HynixCJR/LZ-1-Backplane/dp_to_hdmi.kicad_sch

## KiCad design dp_to_hdmi.kicad_sch (2026-07-11)

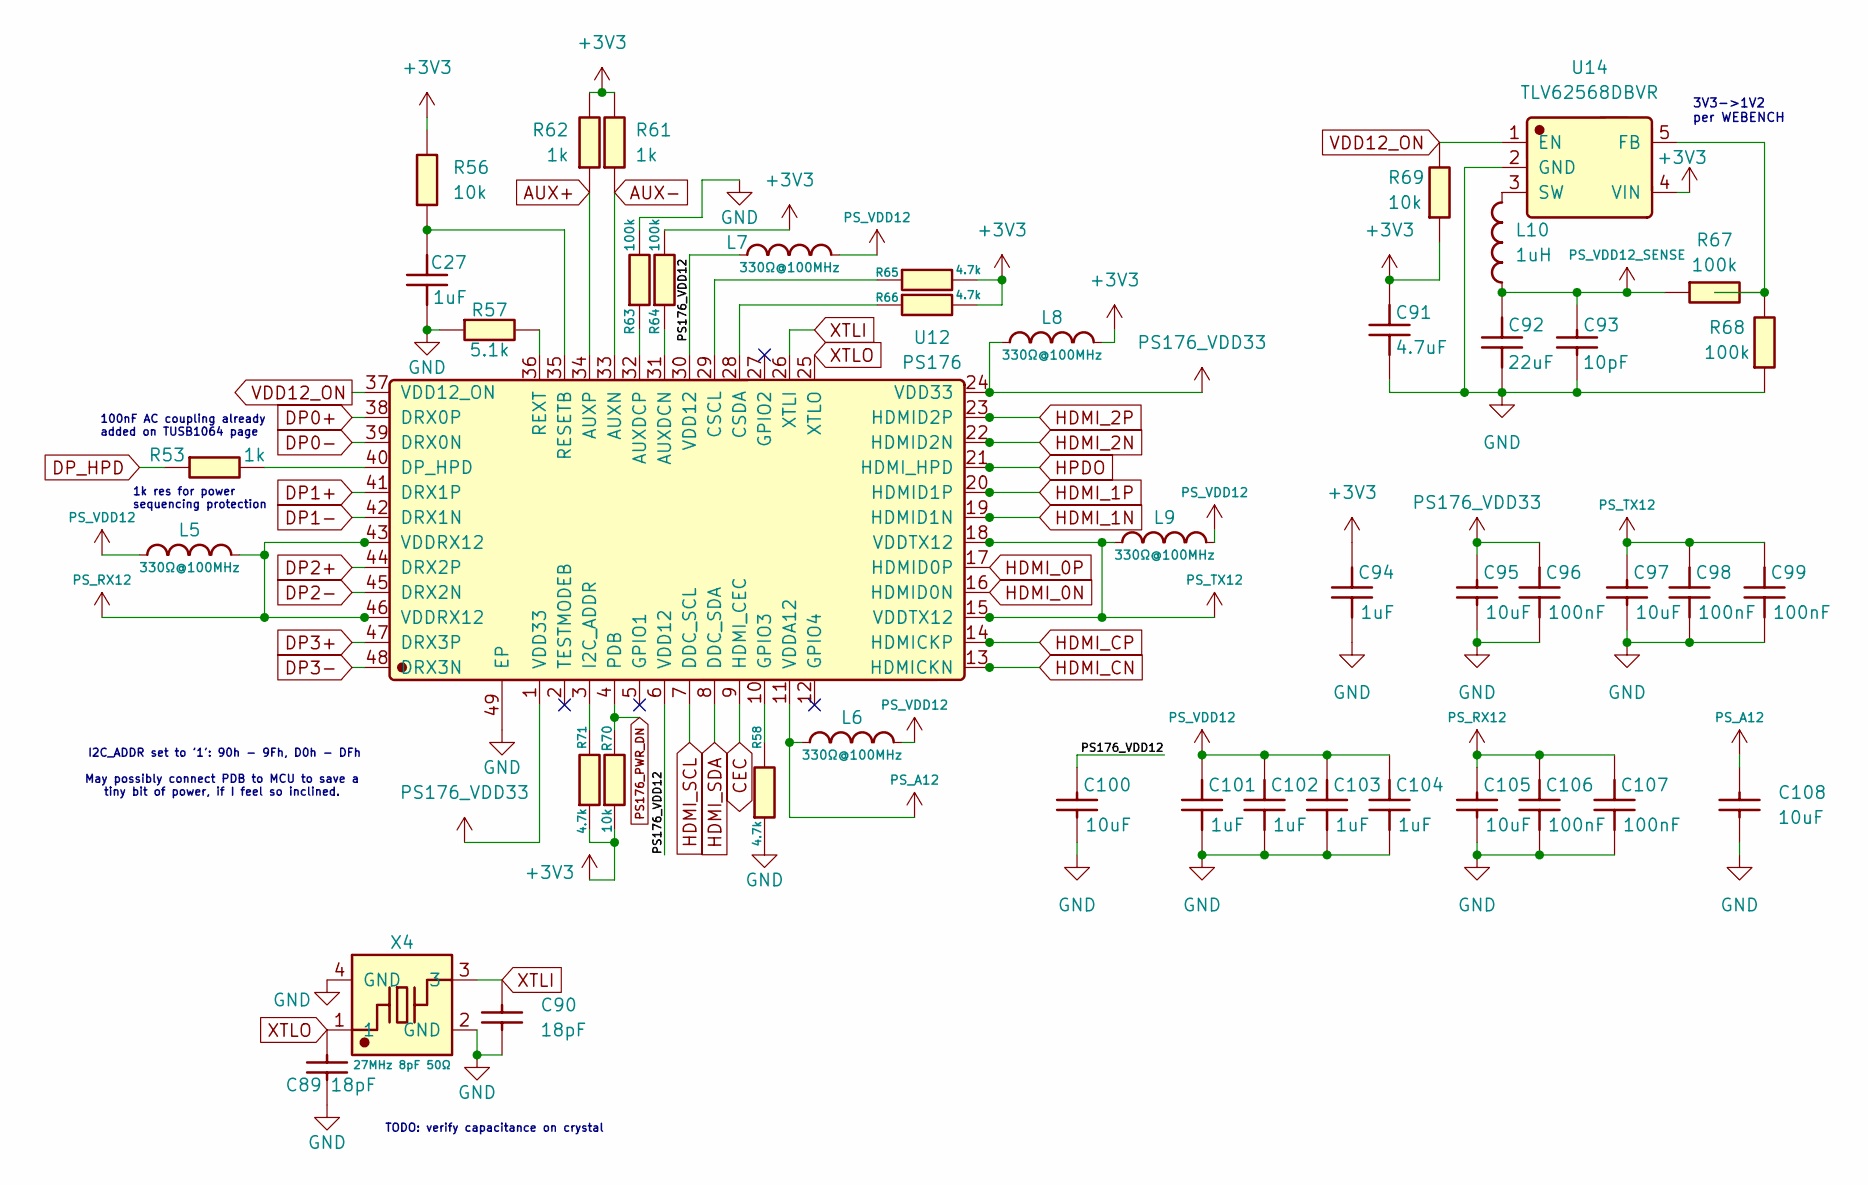
[picture p3: schematic dp_to_hdmi.kicad_sch]

Parts:
C27, C94, C101, C102, C103, C104: 1uF; C_0402_1005Metric; Manufacturer Part CL05A105KA5NQNC; LCSC C52923
C89, C90: 18pF; C_0402_1005Metric; Manufacturer Part 0402CG180J500NT; LCSC C1549
C91: 4.7uF; C_0603_1608Metric; Manufacturer Part CL10A475KO8NNNC; LCSC C19666
C92: 22uF; C_0603_1608Metric; Manufacturer Part CL10A226MQ8NRNC; LCSC C59461
C93: 10pF; C_0603_1608Metric; Manufacturer Part CL10C100JB8NNNC; LCSC C1634
C95, C97, C100, C105, C108: 10uF; C_0402_1005Metric; Manufacturer Part CL05A106MQ5NUNC; LCSC C15525
C96, C98, C99, C106, C107: 100nF; C_0402_1005Metric; Manufacturer Part CL05B104KB54PNC; LCSC C307331
L5, L6, L7, L8, L9: 330Ω@100MHz; BLM18KG331SN1D; Manufacturer Part BLM18KG331SN1D; LCSC C85832
L10: 1uH; TerminalBlock_Phoenix_PTSM-0,5-2-2,5-V-SMD_1x02-1MP_P2.50mm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; Manufacturer Part FTC252012S1R0MBCA; LCSC C5832370
R53: 1k; R_0402_1005Metric; Manufacturer Part 0402WGF1001TCE; LCSC C11702
R56, R69, R70: 10k; R_0402_1005Metric; Manufacturer Part 0402WGF1002TCE; LCSC C25744
R57: 5.1k; R_0402_1005Metric; Manufacturer Part 0402WGF5101TCE; LCSC C25905
R58, R65, R66, R71: 4.7k; R_0402_1005Metric; Manufacturer Part 0402WGF4701TCE; LCSC C25900
R61, R62: 1k; R_0402_1005Metric; Manufacturer Part 0402WGF5101TCE; LCSC C25905
R63, R64, R67, R68: 100k; R_0402_1005Metric; Manufacturer Part 0402WGF1003TCE; LCSC C25741
U12: PS176; Manufacturer Part PS176; LCSC C209703
U14: TLV62568DBVR; Manufacturer Part TLV62568DBVR; LCSC C163219
X4: 27MHz 8pF 50Ω; 5YMA27000121IF50E1; Manufacturer Part 5YMA27000121IF50E1; LCSC C3003248

Connections:
+3V3: C91.2, C94.2, L8.2, R56.2, R61.2, R62.2, R64.2, R65.2, R66.2, R69.1, R70.1, R71.1, U14.4 (VIN)
AUX+: R62.1, U12.34 (AUXP)
AUX-: R61.1, U12.33 (AUXN)
CEC: U12.9 (HDMI_CEC)
DP0+: U12.38 (DRX0P)
DP0-: U12.39 (DRX0N)
DP1+: U12.41 (DRX1P)
DP1-: U12.42 (DRX1N)
DP2+: U12.44 (DRX2P)
DP2-: U12.45 (DRX2N)
DP3+: U12.47 (DRX3P)
DP3-: U12.48 (DRX3N)
DP_HPD: R53.1
GND: C27.1, C89.1, C90.1, C91.1, C92.1, C93.1, C94.1, C95.1, C96.1, C97.1, C98.1, C99.1, C100.1, C101.1, C102.1, C103.1, C104.1, C105.1, C106.1, C107.1, C108.1, R57.1, R58.1, R63.2, R68.1, U12.49 (EP), U14.2 (GND), X4.2 (GND), X4.4 (GND)
HDMI_0N: U12.16 (HDMID0N)
HDMI_0P: U12.17 (HDMID0P)
HDMI_1N: U12.19 (HDMID1N)
HDMI_1P: U12.20 (HDMID1P)
HDMI_2N: U12.22 (HDMID2N)
HDMI_2P: U12.23 (HDMID2P)
HDMI_CN: U12.13 (HDMICKN)
HDMI_CP: U12.14 (HDMICKP)
HDMI_SCL: U12.7 (DDC_SCL)
HDMI_SDA: U12.8 (DDC_SDA)
HPDO: U12.21 (HDMI_HPD)
unnamed: C27.2, R56.1, U12.35 (RESETB)
unnamed: L10.2, U14.3 (SW)
unnamed: R53.2, U12.40 (DP_HPD)
unnamed: R57.2, U12.36 (REXT)
unnamed: R58.2, U12.10 (GPIO3)
unnamed: R63.1, U12.32 (AUXDCP)
unnamed: R64.1, U12.31 (AUXDCN)
unnamed: R65.1, U12.29 (CSCL)
unnamed: R66.1, U12.28 (CSDA)
unnamed: R67.2, R68.2, U14.5 (FB)
unnamed: R71.2, U12.3 (I2C_ADDR)
PS176_PWR_DN: R70.2, U12.4 (PDB)
PS176_VDD12: C100.2, L7.1, U12.6 (VDD12), U12.30 (VDD12)
PS176_VDD33: C95.2, C96.2, L8.1, U12.1 (VDD33), U12.24 (VDD33)
PS_A12: C108.2, L6.1, U12.11 (VDDA12)
PS_RX12: C105.2, C106.2, C107.2, L5.2, U12.43 (VDDRX12), U12.46 (VDDRX12)
PS_TX12: C97.2, C98.2, C99.2, L9.1, U12.15 (VDDTX12), U12.18 (VDDTX12)
PS_VDD12: C101.2, C102.2, C103.2, C104.2, L5.1, L6.2, L7.2, L9.2
PS_VDD12_SENSE: C92.2, C93.2, L10.1, R67.1
VDD12_ON: R69.2, U12.37 (VDD12_ON), U14.1 (EN)
XTLI: C90.2, U12.26 (XTLI), X4.3
XTLO: C89.2, U12.25 (XTLO), X4.1

Notes on the sheet:
1k res for power sequencing protection
3V3->1V2 per WEBENCH
May possibly connect PDB to MCU to save a tiny bit of power, if I feel so inclined.
I2C_ADDR set to '1': 90h - 9Fh, D0h - DFh
100nF AC coupling already added on TUSB1064 page
TODO: verify capacitance on crystal
