HynixCJR/LZ-1-Backplane/hdmi_to_csi.kicad_sch

## KiCad design hdmi_to_csi.kicad_sch (2026-07-11)

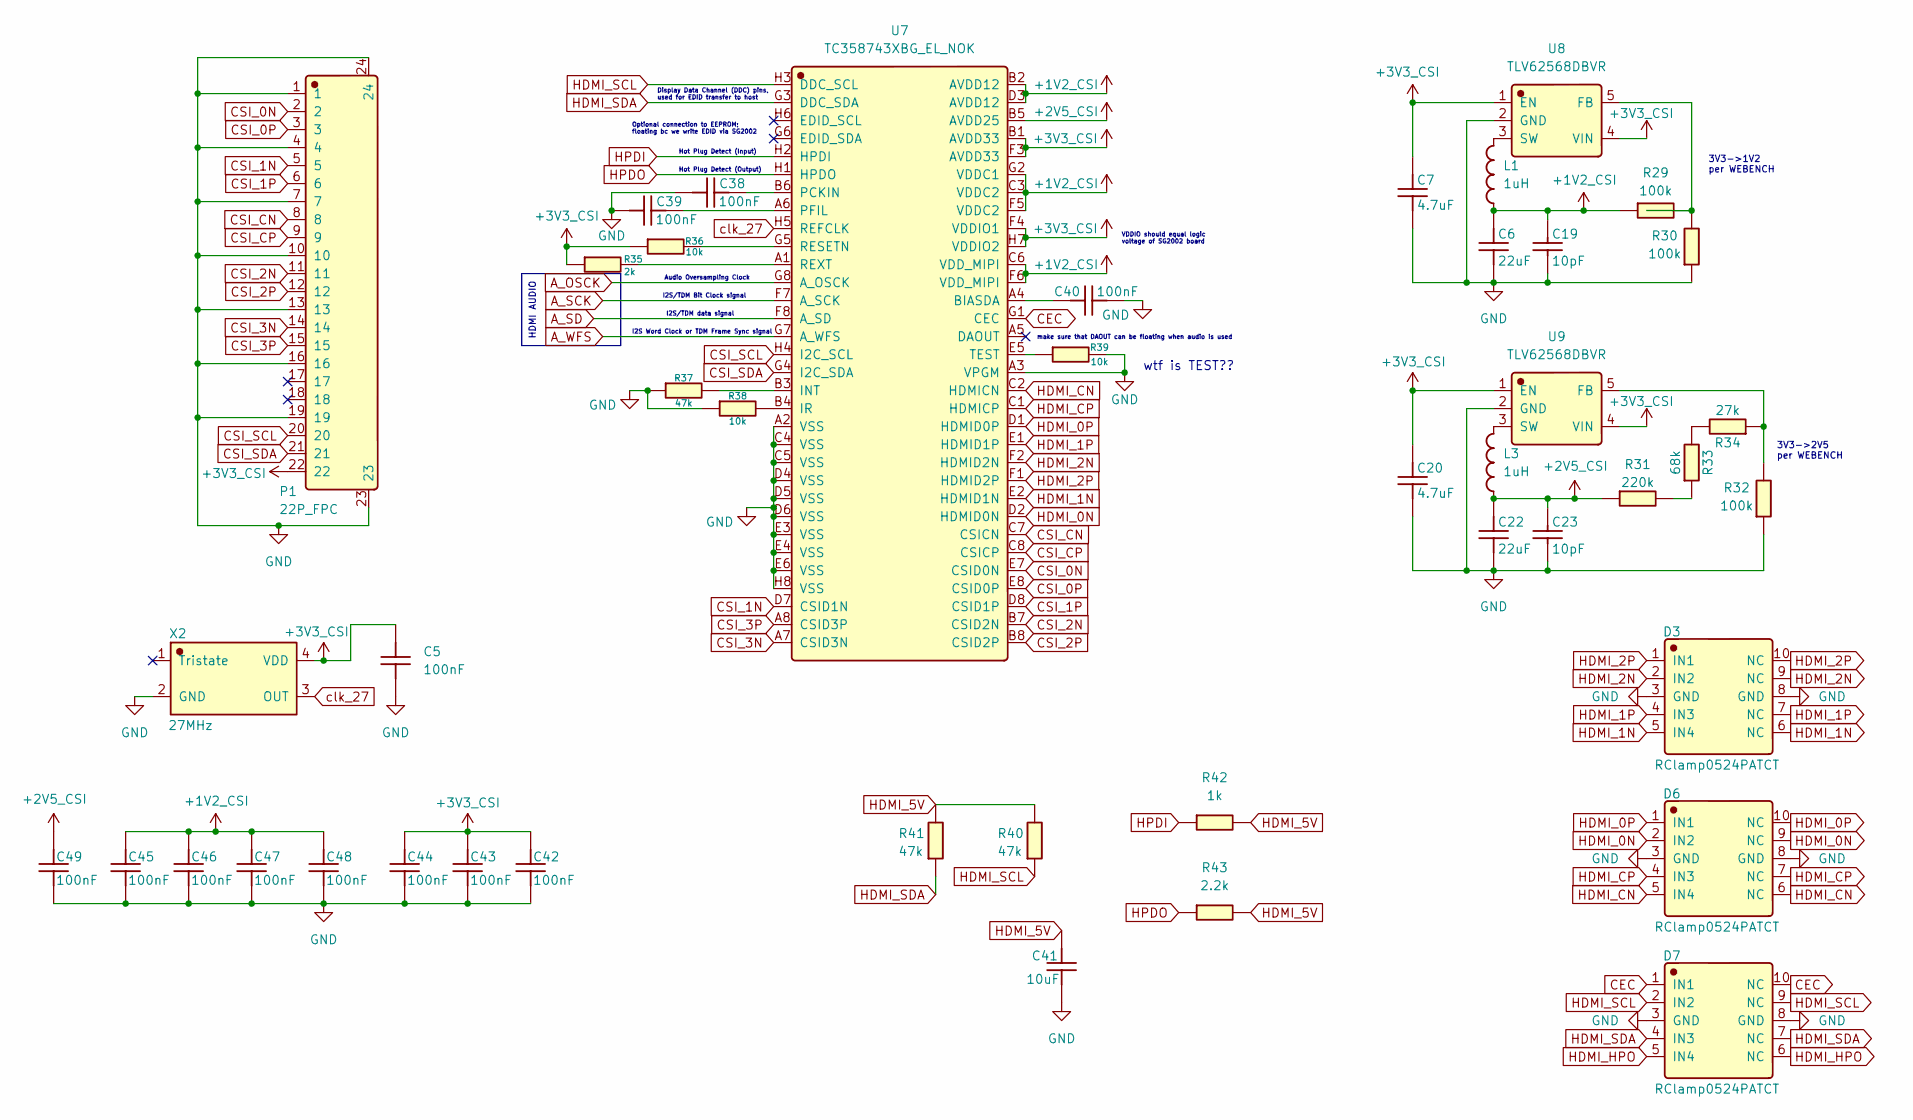
[picture p4: schematic hdmi_to_csi.kicad_sch]

Parts:
C5, C38, C39, C40, C42, C43, C44, C45, C46, C47, C48, C49: 100nF; C_0402_1005Metric; Manufacturer Part CL05B104KB54PNC; LCSC C307331
C6, C22: 22uF; C_0603_1608Metric; Manufacturer Part CL10A226MQ8NRNC; LCSC C59461
C7, C20: 4.7uF; C_0603_1608Metric; Manufacturer Part CL10A475KO8NNNC; LCSC C19666
C19, C23: 10pF; C_0603_1608Metric; Manufacturer Part CL10C100JB8NNNC; LCSC C1634
C41: 10uF; C_0603_1608Metric; Manufacturer Part CL10A106KP8NNNC; LCSC C19702
D3, D6, D7: RClamp0524PATCT; Manufacturer Part RClAMP0524PATCT; LCSC C40960
L1, L3: 1uH; TerminalBlock_Phoenix_PTSM-0,5-2-2,5-V-SMD_1x02-1MP_P2.50mm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; Manufacturer Part FTC252012S1R0MBCA; LCSC C5832370
P1: 22P_FPC; TSSOP-50_4.4x12.5mm_P0.5mm; Manufacturer Part AFC07-S22ECC-00; LCSC C11091
R29, R30, R32: 100k; R_0402_1005Metric; Manufacturer Part 0402WGF1003TCE; LCSC C25741
R31: 220k; R_0603_1608Metric; Manufacturer Part 0603WAF2203T5E; LCSC C22961
R33: 68k; R_0603_1608Metric; Manufacturer Part 0603WAF6802T5E; LCSC C23231
R34: 27k; R_0603_1608Metric; Manufacturer Part 0603WAF2702T5E; LCSC C22967
R35: 2k; R_0603_1608Metric; Manufacturer Part 0603WAF2001T5E; LCSC C22975
R36, R38, R39: 10k; R_0402_1005Metric; Manufacturer Part 0402WGF1002TCE; LCSC C25744
R37, R40, R41: 47k; R_0402_1005Metric; Manufacturer Part 0402WGF4702TCE; LCSC C25792
R42: 1k; R_0402_1005Metric; Manufacturer Part 0402WGF1001TCE; LCSC C11702
R43: 2.2k; R_0402_1005Metric; Manufacturer Part 0402WGF2201TCE; LCSC C25879
U7: TC358743XBG_EL_NOK; Manufacturer Part TC358743XBG(EL,NOK; LCSC C3008606
U8, U9: TLV62568DBVR; Manufacturer Part TLV62568DBVR; LCSC C163219
X2: 27MHz; Oscillator_SMD_Silicon_Labs_LGA-6_2.5x3.2mm_P1.25mm; Manufacturer Part XOS32027000LT00351005; LCSC C37635418

Connections:
+1V2_CSI: C6.2, C19.2, C45.2, C46.2, C47.2, C48.2, L1.1, R29.1, U7.B2 (AVDD12), U7.C3 (VDDC2), U7.C6 (VDD_MIPI), U7.D3 (AVDD12), U7.F5 (VDDC2), U7.F6 (VDD_MIPI), U7.G2 (VDDC1)
+2V5_CSI: C22.2, C23.2, C49.2, L3.1, R31.1, U7.B5 (AVDD25)
+3V3_CSI: C5.2, C7.2, C20.2, C42.2, C43.2, C44.2, P1.22, R35.1, R36.1, U7.B1 (AVDD33), U7.F3 (AVDD33), U7.F4 (VDDIO1), U7.H7 (VDDIO2), U8.1 (EN), U8.4 (VIN), U9.1 (EN), U9.4 (VIN), X2.4 (VDD)
A_OSCK: U7.G8 (A_OSCK)
A_SCK: U7.F7 (A_SCK)
A_SD: U7.F8 (A_SD)
A_WFS: U7.G7 (A_WFS)
CEC: D7.1 (IN1), D7.10 (NC), U7.G1 (CEC)
CSI_0N: P1.2, U7.E7 (CSID0N)
CSI_0P: P1.3, U7.E8 (CSID0P)
CSI_1N: P1.5, U7.D7 (CSID1N)
CSI_1P: P1.6, U7.D8 (CSID1P)
CSI_2N: P1.11, U7.B7 (CSID2N)
CSI_2P: P1.12, U7.B8 (CSID2P)
CSI_3N: P1.14, U7.A7 (CSID3N)
CSI_3P: P1.15, U7.A8 (CSID3P)
CSI_CN: P1.8, U7.C7 (CSICN)
CSI_CP: P1.9, U7.C8 (CSICP)
CSI_SCL: P1.20, U7.H4 (I2C_SCL)
CSI_SDA: P1.21, U7.G4 (I2C_SDA)
GND: C5.1, C6.1, C7.1, C19.1, C20.1, C22.1, C23.1, C38.1, C39.1, C40.2, C41.1, C42.1, C43.1, C44.1, C45.1, C46.1, C47.1, C48.1, C49.1, D3.3 (GND), D3.8 (GND), D6.3 (GND), D6.8 (GND), D7.3 (GND), D7.8 (GND), P1.1, P1.4, P1.7, P1.10, P1.13, P1.16, P1.19, P1.23, P1.24, R30.1, R32.1, R37.1, R38.1, R39.2, U7.A2 (VSS), U7.A3 (VPGM), U7.C4 (VSS), U7.C5 (VSS), U7.D4 (VSS), U7.D5 (VSS), U7.D6 (VSS), U7.E3 (VSS), U7.E4 (VSS), U7.E6 (VSS), U7.H8 (VSS), U8.2 (GND), U9.2 (GND), X2.2 (GND)
HDMI_0N: D6.2 (IN2), D6.9 (NC), U7.D2 (HDMID0N)
HDMI_0P: D6.1 (IN1), D6.10 (NC), U7.D1 (HDMID0P)
HDMI_1N: D3.5 (IN4), D3.6 (NC), U7.E2 (HDMID1N)
HDMI_1P: D3.4 (IN3), D3.7 (NC), U7.E1 (HDMID1P)
HDMI_2N: D3.2 (IN2), D3.9 (NC), U7.F2 (HDMID2N)
HDMI_2P: D3.1 (IN1), D3.10 (NC), U7.F1 (HDMID2P)
HDMI_5V: C41.2, R40.2, R41.2, R42.2, R43.2
HDMI_CN: D6.5 (IN4), D6.6 (NC), U7.C2 (HDMICN)
HDMI_CP: D6.4 (IN3), D6.7 (NC), U7.C1 (HDMICP)
HDMI_HPO: D7.5 (IN4), D7.6 (NC)
HDMI_SCL: D7.2 (IN2), D7.9 (NC), R40.1, U7.H3 (DDC_SCL)
HDMI_SDA: D7.4 (IN3), D7.7 (NC), R41.1, U7.G3 (DDC_SDA)
HPDI: R42.1, U7.H2 (HPDI)
HPDO: R43.1, U7.H1 (HPDO)
unnamed: C38.2, U7.B6 (PCKIN)
unnamed: C39.2, U7.A6 (PFIL)
unnamed: C40.1, U7.A4 (BIASDA)
unnamed: L1.2, U8.3 (SW)
unnamed: L3.2, U9.3 (SW)
unnamed: R29.2, R30.2, U8.5 (FB)
unnamed: R31.2, R33.1
unnamed: R32.2, R34.1, U9.5 (FB)
unnamed: R33.2, R34.2
unnamed: R35.2, U7.A1 (REXT)
unnamed: R36.2, U7.G5 (RESETN)
unnamed: R37.2, U7.B3 (INT)
unnamed: R38.2, U7.B4 (IR)
unnamed: R39.1, U7.E5 (TEST)
clk_27: U7.H5 (REFCLK), X2.3 (OUT)

Notes on the sheet:
Hot Plug Detect (Output)
wtf is TEST??
Optional connection to EEPROM; floating bc we write EDID via SG2002
VDDIO should equal logic voltage of SG2002 board
make sure that DAOUT can be floating when audio is used
HDMI AUDIO
3V3->2V5 per WEBENCH
Hot Plug Detect (Input)
I2S/TDM Bit Clock signal
I2S Word Clock or TDM Frame Sync signal
Audio Oversampling Clock
Display Data Channel (DDC) pins, used for EDID transfer to host
3V3->1V2 per WEBENCH
I2S/TDM data signal
