HynixCJR/LZ-1-Backplane/pcb_files/FAN_HEADER.kicad_sch

## KiCad design pcb_files/FAN_HEADER.kicad_sch (2026-08-20)

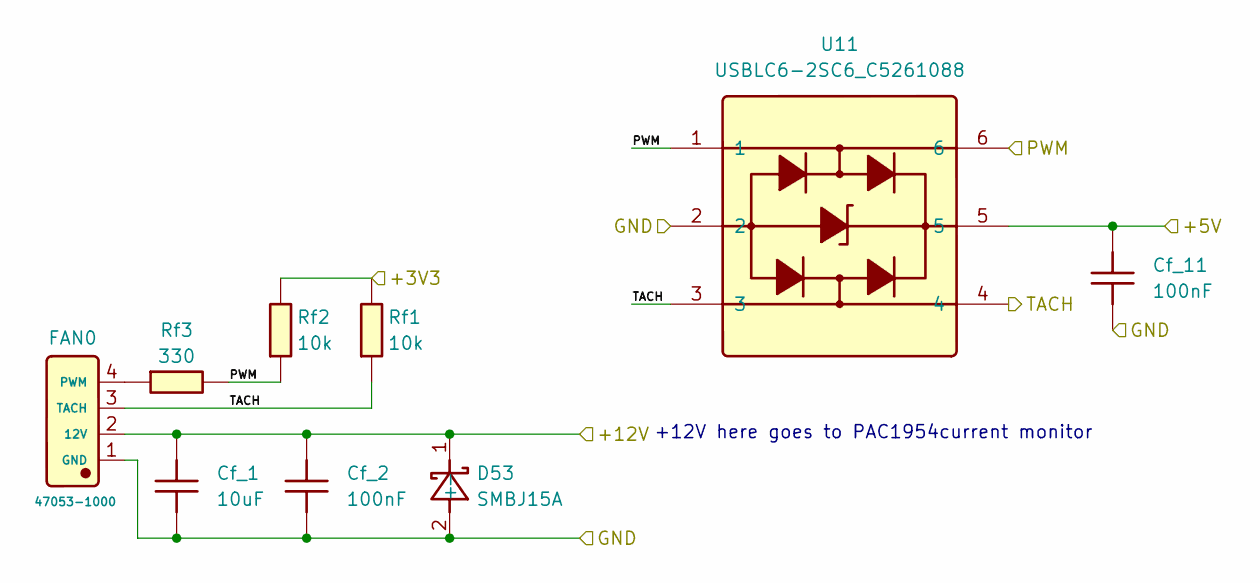
[picture p5: schematic FAN_HEADER.kicad_sch]

Parts:
Cf_1: 10uF; C_0603_1608Metric; Manufacturer Part CL10A106KP8NNNC; LCSC C19702
Cf_2, Cf_11: 100nF; C_0402_1005Metric; Manufacturer Part CL05B104KB54PNC; LCSC C307331
D53: SMBJ15A; SMBJ15A_C42370523; Manufacturer Part SMBJ15A; LCSC C42370523
FAN0: 47053-1000; Manufacturer Part 470531000; LCSC C240840
Rf1, Rf2: 10k; R_0402_1005Metric; Manufacturer Part 0402WGF1002TCE; LCSC C25744
Rf3: 330; R_0402_1005Metric; Manufacturer Part 0402WGF3300TCE; LCSC C25104
U11: USBLC6-2SC6_C5261088; Manufacturer Part USBLC6-2SC6; LCSC C5261088

Connections:
+3V3: Rf1.2, Rf2.2
+5V: Cf_11.2, U11.5
+12V: Cf_1.2, Cf_2.2, D53.1 (-), FAN0.2 (12V)
GND: Cf_1.1, Cf_2.1, Cf_11.1, D53.2 (+), FAN0.1 (GND), U11.2
unnamed: FAN0.4 (PWM), Rf3.1
PWM: Rf2.1, Rf3.2, U11.1, U11.6
TACH: FAN0.3 (TACH), Rf1.1, U11.3, U11.4

Notes on the sheet:
+12V here goes to PAC1954current monitor
