HynixCJR/LZ-1-Backplane/pcb_files/LT6911UXC.kicad_sch

## KiCad design pcb_files/LT6911UXC.kicad_sch (2026-07-25)

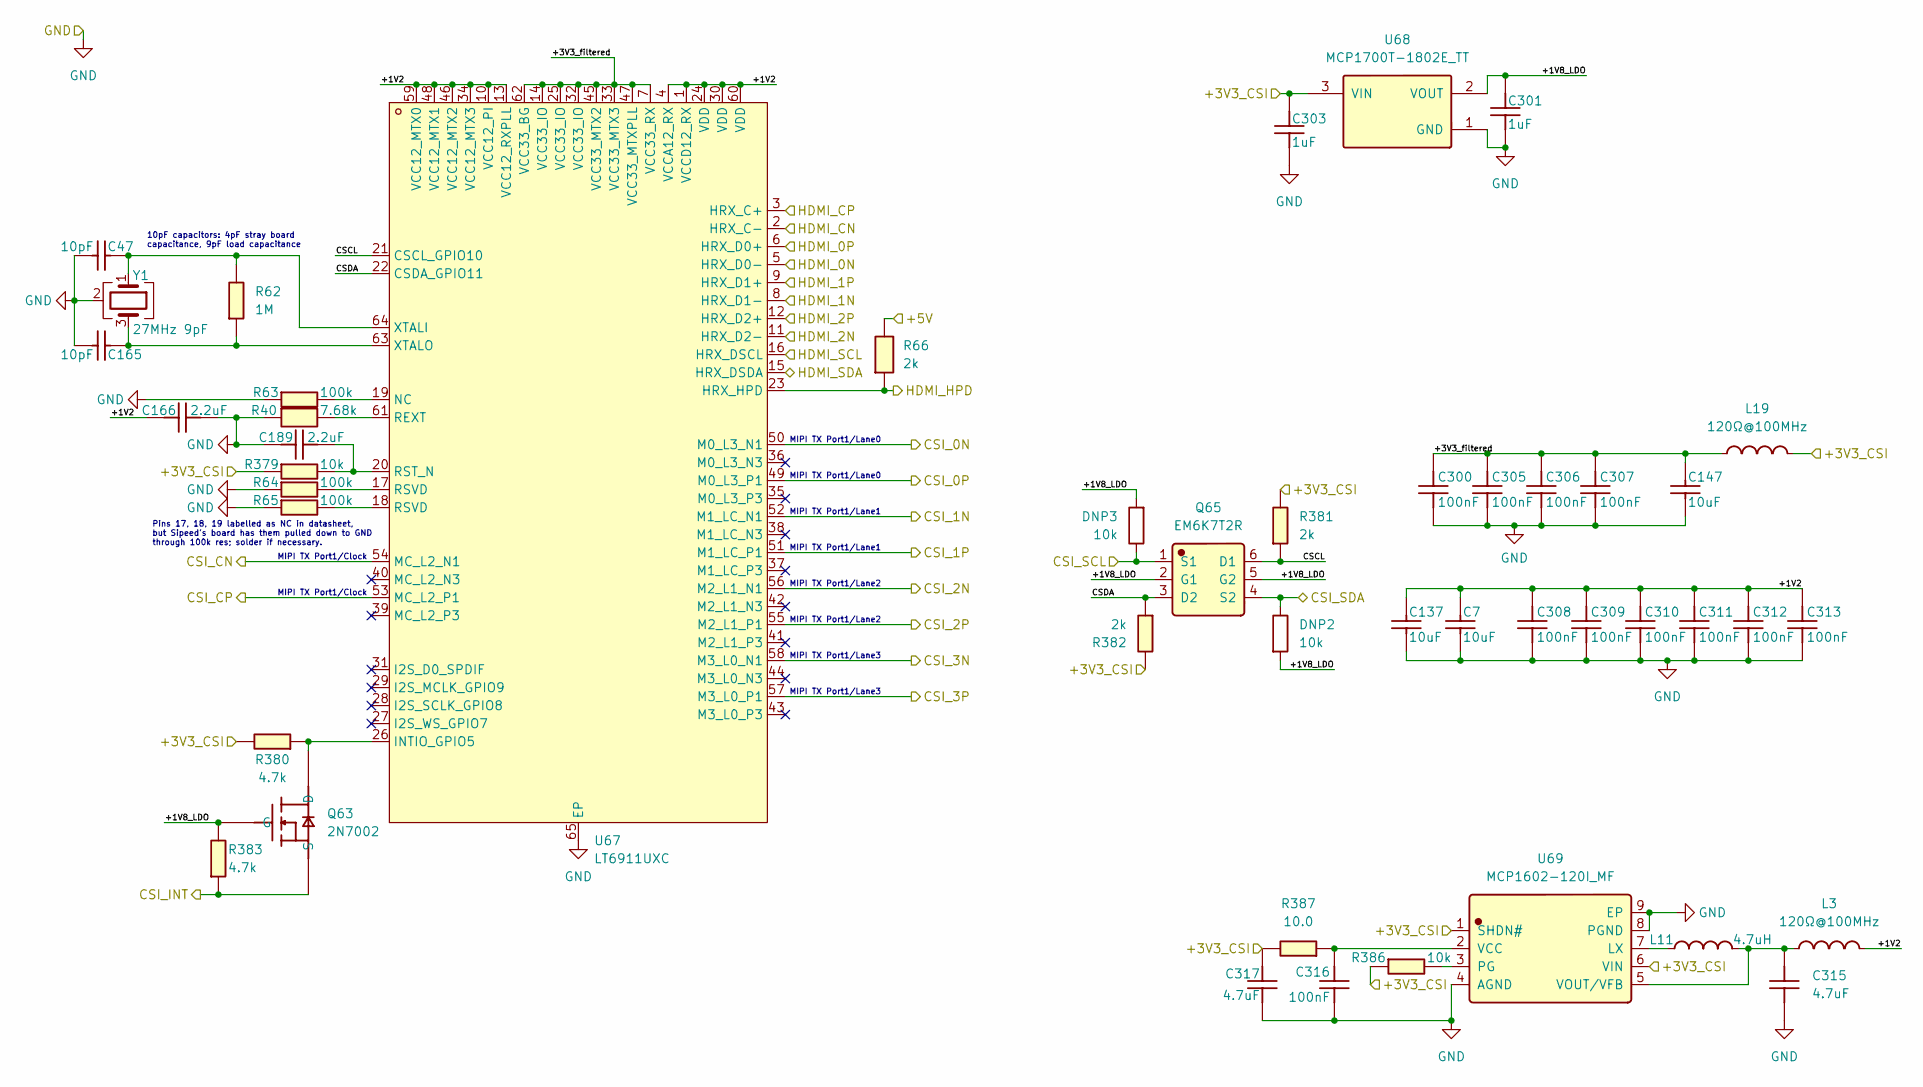
[picture p6: schematic LT6911UXC.kicad_sch]

Parts:
C7, C137, C147: 10uF; C_0402_1005Metric; Manufacturer Part CL05A106MQ5NUNC; LCSC C15525
C47, C165: 10pF; C_0603_1608Metric; Manufacturer Part CL10C100JB8NNNC; LCSC C1634
C166, C189: 2.2uF; C_0402_1005Metric; Manufacturer Part JMK105BJ225MVHF; LCSC C386010
C300, C305, C306, C307, C308, C309, C310, C311, C312, C313, C316: 100nF; C_0402_1005Metric; Manufacturer Part CL05B104KB54PNC; LCSC C307331
C301, C303: 1uF; C_0402_1005Metric; Manufacturer Part CL05A105KA5NQNC; LCSC C52923
C315, C317: 4.7uF; C_0402_1005Metric; Manufacturer Part CL05A475MP5NRNC; LCSC C23733
DNP2, DNP3: 10k; R_0402_1005Metric
L3, L19: 120Ω@100MHz; L_0805_2012Metric; Manufacturer Part GDPZ2012M121-4A0TF; LCSC C51018428
L11: 4.7uH; PIM201608S4R7MBCA; Manufacturer Part PIM201608S4R7MBCA; LCSC C53514738
Q63: 2N7002; 2N7002_C916396; Manufacturer Part 2N7002; LCSC C916396
Q65: EM6K7T2R; Manufacturer Part EM6K7T2R; LCSC C253325
R40: 7.68k; R_0402_1005Metric; Manufacturer Part CL0402FN7K68P; LCSC C48996795
R62: 1M; R_0402_1005Metric; Manufacturer Part 0402WGF1004TCE; LCSC C26083
R63, R64, R65: 100k; R_0402_1005Metric; Manufacturer Part 0402WGF1003TCE; LCSC C25741
R66: 2k; R_0402_1005Metric; Manufacturer Part 1RC0402J0202; LCSC C54531046
R379, R386: 10k; R_0402_1005Metric; Manufacturer Part 0402WGF1002TCE; LCSC C25744
R380, R383: 4.7k; R_0402_1005Metric; Manufacturer Part 0402WGF4701TCE; LCSC C25900
R381, R382: 2k; R_0603_1608Metric; Manufacturer Part 0603WAF2001T5E; LCSC C22975
R387: 10.0; R_0402_1005Metric; Manufacturer Part 0402WGF100JTCE; LCSC C25077
U67: LT6911UXC; QFN-64_L7.5-W7.5-P0.40-TL-EP6.2; MPN LT6911UXC; LCSC Part C9900155845
U68: MCP1700T-1802E_TT; Manufacturer Part MCP1700T-1802E/TT; LCSC C150796
U69: MCP1602-120I_MF; Manufacturer Part MCP1602-120I/MF; LCSC C635082
Y1: 27MHz 9pF; Crystal_SMD_3225-4Pin_3.2x2.5mm; MPN XTM32027000FT00351001; LCSC C37635384

Connections:
+1V2: C7.2, C137.2, C166.2, C308.2, C309.2, C310.2, C311.2, C312.2, C313.2, L3.2, U67.1 (VCCD12_RX), U67.4 (VCCA12_RX), U67.10 (VCC12_PI), U67.13 (VCC12_RXPLL), U67.24 (VDD), U67.30 (VDD), U67.34 (VCC12_MTX3), U67.46 (VCC12_MTX2), U67.48 (VCC12_MTX1), U67.59 (VCC12_MTX0), U67.60 (VDD)
+1V8_LDO: C301.2, DNP2.2, DNP3.2, Q63.1 (G), Q65.2 (G1), Q65.5 (G2), R383.2, U68.2 (VOUT)
+3V3_CSI: C303.2, C317.2, L19.2, R379.1, R380.2, R381.2, R382.2, R386.1, R387.2, U68.3 (VIN), U69.1 (SHDN#), U69.6 (VIN)
+3V3_filtered: C147.2, C300.2, C305.2, C306.2, C307.2, L19.1, U67.7 (VCC33_RX), U67.14 (VCC33_IO), U67.25 (VCC33_IO), U67.32 (VCC33_IO), U67.33 (VCC33_MTX3), U67.45 (VCC33_MTX2), U67.47 (VCC33_MTXPLL), U67.62 (VCC33_BG)
+5V: R66.2
CSCL: Q65.6 (D1), R381.1, U67.21 (CSCL_GPIO10)
CSDA: Q65.3 (D2), R382.1, U67.22 (CSDA_GPIO11)
CSI_0N: U67.50 (M0_L3_N1)
CSI_0P: U67.49 (M0_L3_P1)
CSI_1N: U67.52 (M1_LC_N1)
CSI_1P: U67.51 (M1_LC_P1)
CSI_2N: U67.56 (M2_L1_N1)
CSI_2P: U67.55 (M2_L1_P1)
CSI_3N: U67.58 (M3_L0_N1)
CSI_3P: U67.57 (M3_L0_P1)
CSI_CN: U67.54 (MC_L2_N1)
CSI_CP: U67.53 (MC_L2_P1)
CSI_INT: Q63.2 (S), R383.1
CSI_SCL: DNP3.1, Q65.1 (S1)
CSI_SDA: DNP2.1, Q65.4 (S2)
GND: C7.1, C47.1, C137.1, C147.1, C165.2, C166.1, C189.2, C300.1, C301.1, C303.1, C305.1, C306.1, C307.1, C308.1, C309.1, C310.1, C311.1, C312.1, C313.1, C315.1, C316.1, C317.1, R40.1, R63.1, R64.1, R65.1, U67.65 (EP), U68.1 (GND), U69.4 (AGND), U69.8 (PGND), U69.9 (EP), Y1.2 (G), Y1.4 (G)
HDMI_0N: U67.5 (HRX_D0-)
HDMI_0P: U67.6 (HRX_D0+)
HDMI_1N: U67.8 (HRX_D1-)
HDMI_1P: U67.9 (HRX_D1+)
HDMI_2N: U67.11 (HRX_D2-)
HDMI_2P: U67.12 (HRX_D2+)
HDMI_CN: U67.2 (HRX_C-)
HDMI_CP: U67.3 (HRX_C+)
HDMI_HPD: R66.1, U67.23 (HRX_HPD)
HDMI_SCL: U67.16 (HRX_DSCL)
HDMI_SDA: U67.15 (HRX_DSDA)
unnamed: C47.2, R62.2, U67.64 (XTALI), Y1.1
unnamed: C165.1, R62.1, U67.63 (XTALO), Y1.3
unnamed: C189.1, R379.2, U67.20 (RST_N)
unnamed: C315.2, L3.1, L11.2, U69.5 (VOUT/VFB)
unnamed: C316.2, R387.1, U69.2 (VCC)
unnamed: L11.1, U69.7 (LX)
unnamed: Q63.3 (D), R380.1, U67.26 (INTIO_GPIO5)
unnamed: R40.2, U67.61 (REXT)
unnamed: R63.2, U67.19 (NC)
unnamed: R64.2, U67.17 (RSVD)
unnamed: R65.2, U67.18 (RSVD)
unnamed: R386.2, U69.3 (PG)

Notes on the sheet:
MIPI TX Port1/Lane0
MIPI TX Port1/Lane2
MIPI TX Port1/Lane3
MIPI TX Port1/Lane1
MIPI TX Port1/Clock
10pF capacitors: 4pF stray board capacitance, 9pF load capacitance
Pins 17, 18, 19 labelled as NC in datasheet, but Sipeed's board has them pulled down to GND through 100k res; solder if necessary.
