HynixCJR/LZ-1-Backplane/pcb_files/MCP6002.kicad_sch

## KiCad design pcb_files/MCP6002.kicad_sch (2026-07-26)

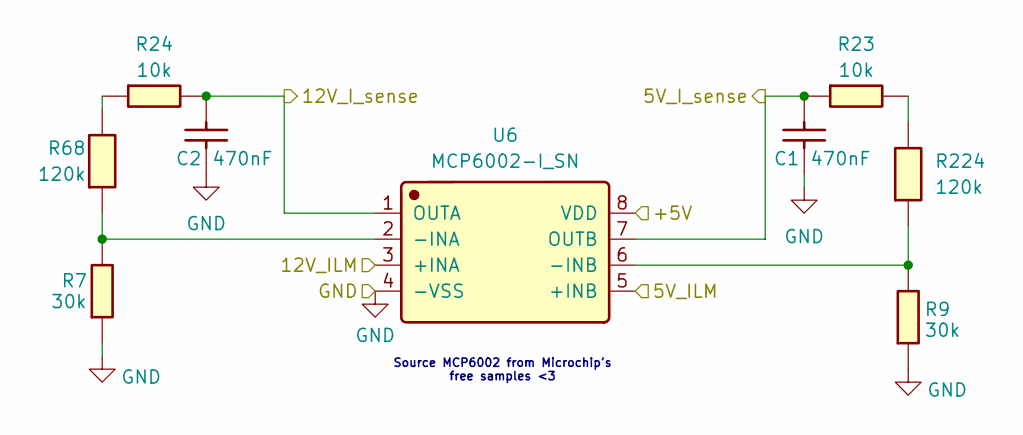
[picture p8: schematic MCP6002.kicad_sch]

Parts:
C1, C2: 470nF; C_0603_1608Metric; Manufacturer Part CL10B474KA8NNNC; LCSC C1623
R7, R9: 30k; R_0603_1608Metric; Manufacturer Part 0603WAF3002T5E; LCSC C22984
R23, R24: 10k; R_0402_1005Metric; Manufacturer Part 0402WGF1002TCE; LCSC C25744
R68, R224: 120k; R_0402_1005Metric; Manufacturer Part HRC0402F1203DNTO; LCSC C54920620
U6: MCP6002-I_SN; Manufacturer Part MCP6002-I/SN; LCSC C116706

Connections:
5V_ILM: U6.5 (+INB)
5V_I_sense: C1.2, R23.1, U6.7 (OUTB)
12V_ILM: U6.3 (+INA)
12V_I_sense: C2.2, R24.2, U6.1 (OUTA)
+5V: U6.8 (VDD)
GND: C1.1, C2.1, R7.1, R9.1, U6.4 (-VSS)
unnamed: R24.1, R68.2
unnamed: R7.2, R68.1, U6.2 (-INA)
unnamed: R9.2, R224.1, U6.6 (-INB)
unnamed: R23.2, R224.2

Notes on the sheet:
Source MCP6002 from Microchip's free samples <3
