HynixCJR/LZ-1-Backplane/pcb_files/MCP9808.kicad_sch

## KiCad design pcb_files/MCP9808.kicad_sch (2026-08-17)

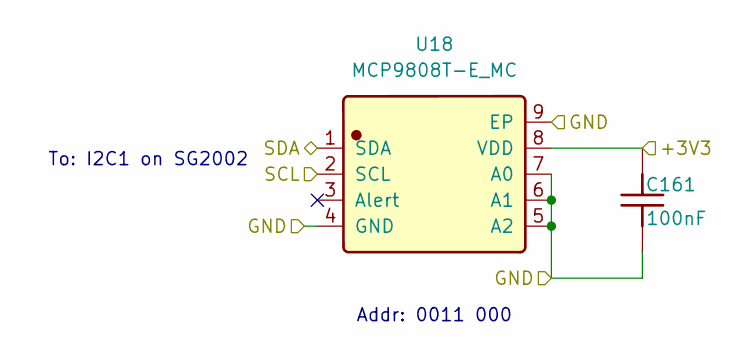
[picture p9: schematic MCP9808.kicad_sch]

Parts:
C161: 100nF; C_0402_1005Metric; Manufacturer Part CL05B104KB54PNC; LCSC C307331
U18: MCP9808T-E_MC; Manufacturer Part MCP9808T-E/MC; LCSC C194710

Connections:
+3V3: C161.1, U18.8 (VDD)
GND: C161.2, U18.4 (GND), U18.5 (A2), U18.6 (A1), U18.7 (A0), U18.9 (EP)
SCL: U18.2 (SCL)
SDA: U18.1 (SDA)

Notes on the sheet:
To: I2C1 on SG2002
Addr: 0011 000
