HynixCJR/LZ-1-Backplane/pcb_files/PAC1954_FANS.kicad_sch

## KiCad design pcb_files/PAC1954_FANS.kicad_sch (2026-08-20)

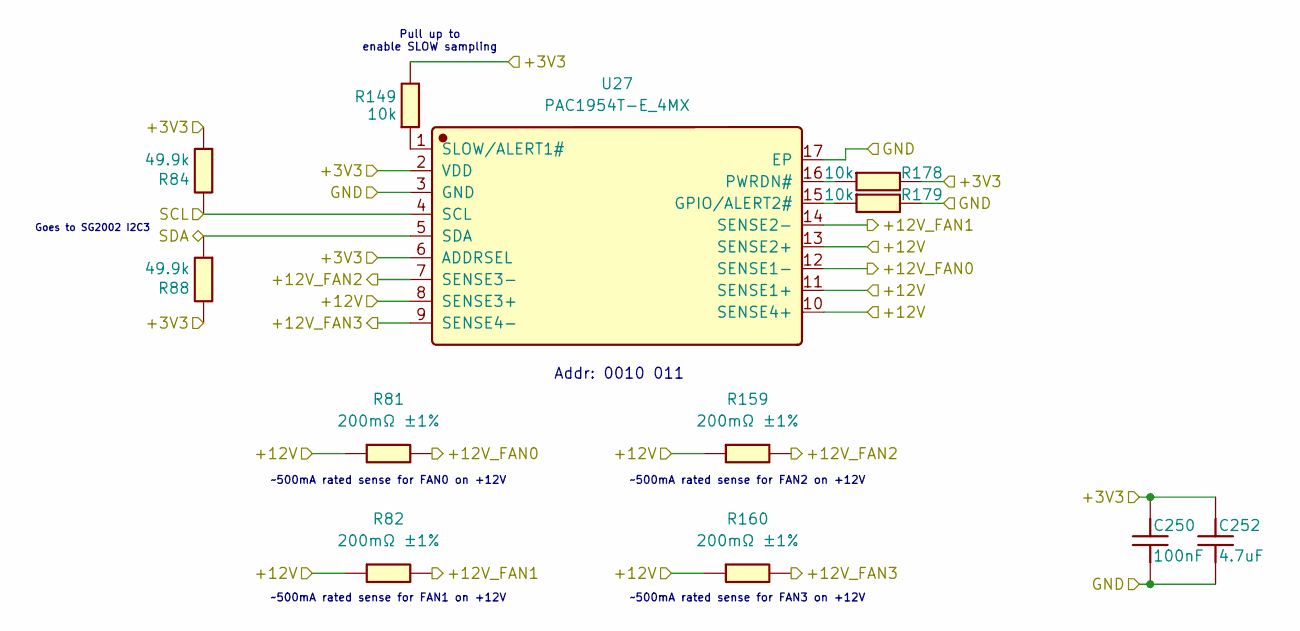
[picture p10: schematic PAC1954_FANS.kicad_sch]

Parts:
C250: 100nF; C_0402_1005Metric; Manufacturer Part CL05B104KB54PNC; LCSC C307331
C252: 4.7uF; C_0402_1005Metric; Manufacturer Part CL05A475MP5NRNC; LCSC C23733
R81, R82, R159, R160: 200mΩ ±1%; RL12FTNR200; Manufacturer Part RL12FTNR200; LCSC C160920
R84, R88: 49.9k; R_0402_1005Metric; Manufacturer Part RMS04FT4992; LCSC C208898
R149, R178, R179: 10k; R_0402_1005Metric; Manufacturer Part 0402WGF1002TCE; LCSC C25744
U27: PAC1954T-E_4MX; Manufacturer Part PAC1954T-E/4MX; LCSC C3687526

Connections:
+3V3: C250.2, C252.2, R84.1, R88.2, R149.2, R178.2, U27.2 (VDD), U27.6 (ADDRSEL)
+12V: R81.1, R82.1, R159.1, R160.1, U27.8 (SENSE3+), U27.10 (SENSE4+), U27.11 (SENSE1+), U27.13 (SENSE2+)
+12V_FAN0: R81.2, U27.12 (SENSE1-)
+12V_FAN1: R82.2, U27.14 (SENSE2-)
+12V_FAN2: R159.2, U27.7 (SENSE3-)
+12V_FAN3: R160.2, U27.9 (SENSE4-)
GND: C250.1, C252.1, R179.2, U27.3 (GND), U27.17 (EP)
unnamed: R149.1, U27.1 (SLOW/ALERT1#)
unnamed: R178.1, U27.16 (PWRDN#)
unnamed: R179.1, U27.15 (GPIO/ALERT2#)
SCL: R84.2, U27.4 (SCL)
SDA: R88.1, U27.5 (SDA)

Notes on the sheet:
~500mA rated sense for FAN3 on +12V
~500mA rated sense for FAN1 on +12V
Addr: 0010 011
Goes to SG2002 I2C3
~500mA rated sense for FAN2 on +12V
~500mA rated sense for FAN0 on +12V
Pull up to enable SLOW sampling
