HynixCJR/LZ-1-Backplane/pcb_files/PAC1954_HUB.kicad_sch

## KiCad design pcb_files/PAC1954_HUB.kicad_sch (2026-08-20)

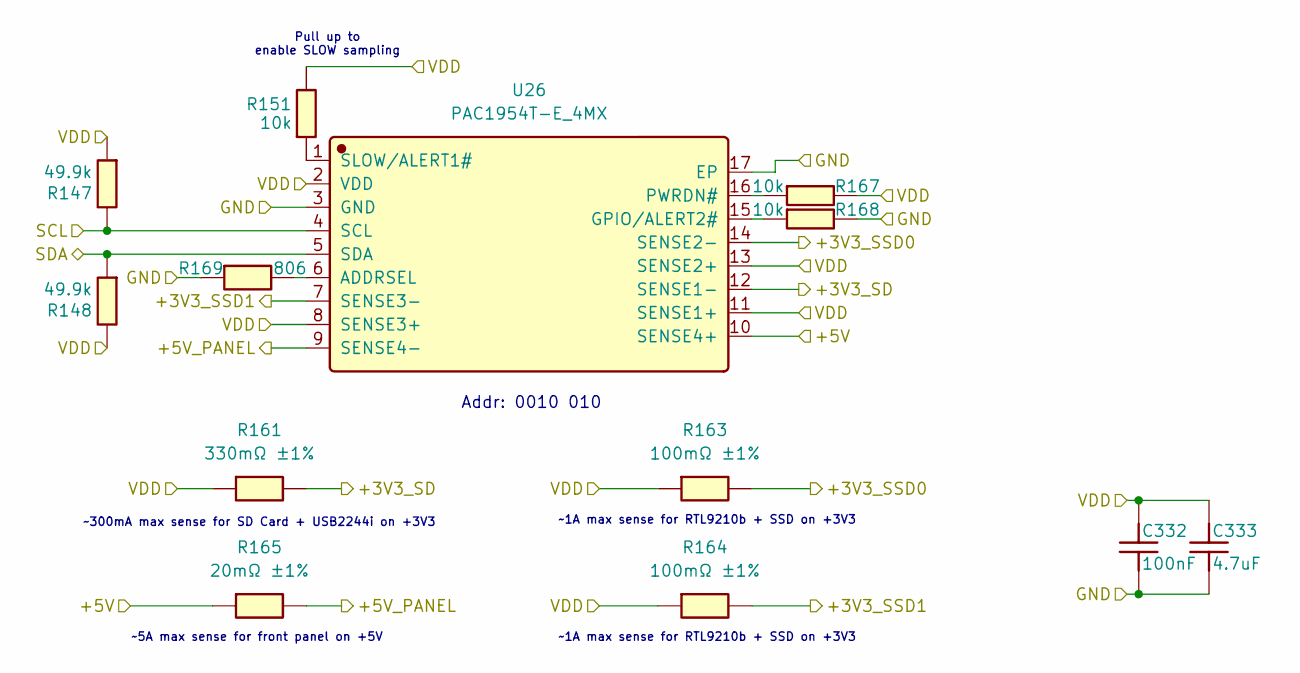
[picture p11: schematic PAC1954_HUB.kicad_sch]

Parts:
C332: 100nF; C_0402_1005Metric; Manufacturer Part CL05B104KB54PNC; LCSC C307331
C333: 4.7uF; C_0402_1005Metric; Manufacturer Part CL05A475MP5NRNC; LCSC C23733
R147, R148: 49.9k; R_0402_1005Metric; Manufacturer Part RMS04FT4992; LCSC C208898
R151, R167, R168: 10k; R_0402_1005Metric; Manufacturer Part 0402WGF1002TCE; LCSC C25744
R161: 330mΩ ±1%; R_2512_6332Metric; Manufacturer Part RBJ-12MR330FT; LCSC C19269965
R163, R164: 100mΩ ±1%; R_2512_6332Metric; Manufacturer Part JER2512F2R100; LCSC C49164916
R165: 20mΩ ±1%; R_0603_1608Metric; Manufacturer Part RBL06FTR020; LCSC C911681
R169: 806; R_0402_1005Metric; Manufacturer Part CR0402FF8060G; LCSC C5452451
U26: PAC1954T-E_4MX; Manufacturer Part PAC1954T-E/4MX; LCSC C3687526

Connections:
+3V3_SD: R161.2, U26.12 (SENSE1-)
+3V3_SSD0: R163.2, U26.14 (SENSE2-)
+3V3_SSD1: R164.2, U26.7 (SENSE3-)
+5V: R165.1, U26.10 (SENSE4+)
+5V_PANEL: R165.2, U26.9 (SENSE4-)
GND: C332.1, C333.1, R168.2, R169.1, U26.3 (GND), U26.17 (EP)
unnamed: R151.1, U26.1 (SLOW/ALERT1#)
unnamed: R167.1, U26.16 (PWRDN#)
unnamed: R168.1, U26.15 (GPIO/ALERT2#)
unnamed: R169.2, U26.6 (ADDRSEL)
SCL: R147.2, U26.4 (SCL)
SDA: R148.1, U26.5 (SDA)
VDD: C332.2, C333.2, R147.1, R148.2, R151.2, R161.1, R163.1, R164.1, R167.2, U26.2 (VDD), U26.8 (SENSE3+), U26.11 (SENSE1+), U26.13 (SENSE2+)

Notes on the sheet:
~1A max sense for RTL9210b + SSD on +3V3
~5A max sense for front panel on +5V
Pull up to enable SLOW sampling
Addr: 0010 010
~300mA max sense for SD Card + USB2244i on +3V3
