HynixCJR/LZ-1-Backplane/pcb_files/PAC1954_IPKVM_DISP.kicad_sch

## KiCad design pcb_files/PAC1954_IPKVM_DISP.kicad_sch (2026-08-31, an earlier design)

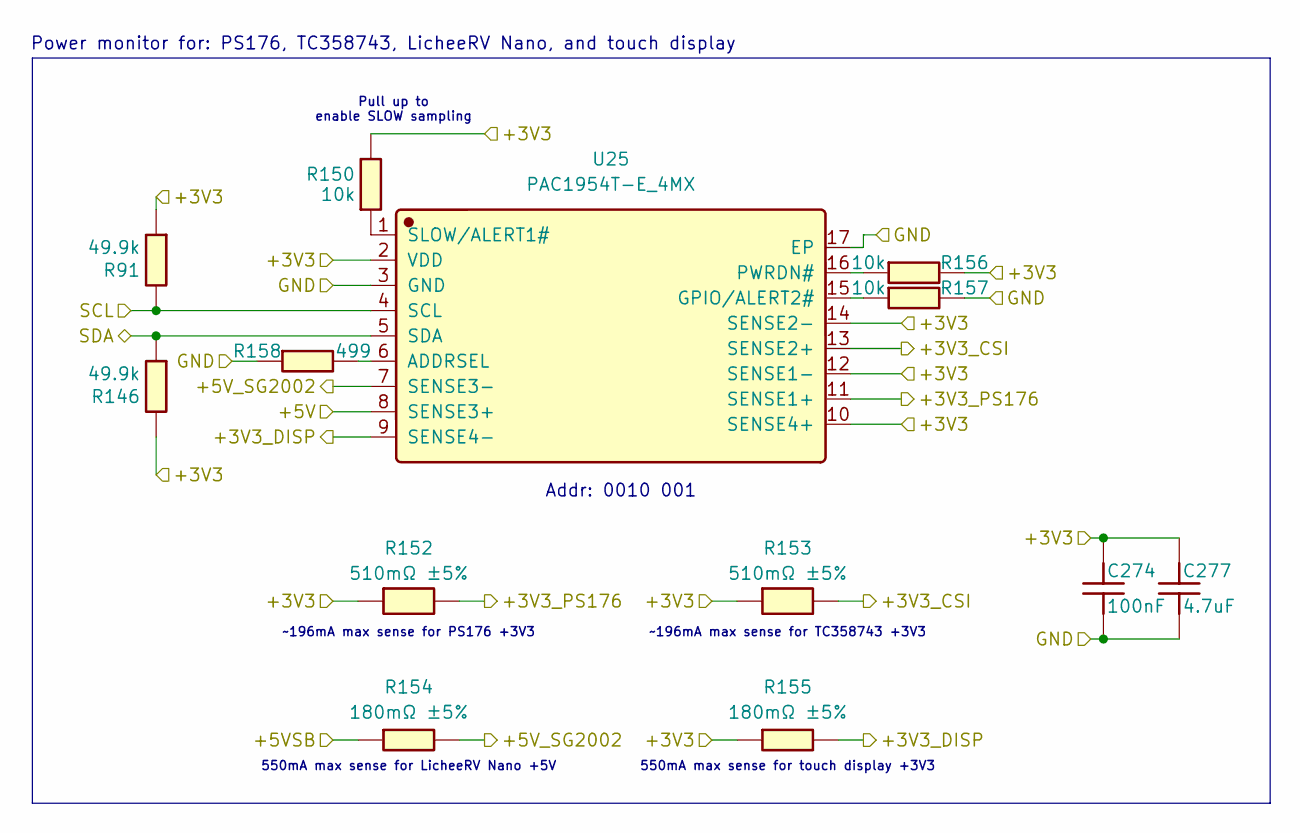
[picture p12: schematic PAC1954_IPKVM_DISP.kicad_sch]

Parts:
C274: 100nF; C_0402_1005Metric; Manufacturer Part CL05B104KB54PNC; LCSC C307331
C277: 4.7uF; C_0402_1005Metric; Manufacturer Part CL05A475MP5NRNC; LCSC C23733
R91, R146: 49.9k; R_0402_1005Metric; Manufacturer Part RMS04FT4992; LCSC C208898
R150, R156, R157: 10k; R_0402_1005Metric; Manufacturer Part 0402WGF1002TCE; LCSC C25744
R152, R153: 510mΩ ±5%; R_1210_3225Metric; Manufacturer Part RBR-1210SR510JT; LCSC C19269960
R154, R155: 180mΩ ±5%; R_0508_1220Metric; Manufacturer Part LTR10EVHJLR18; LCSC C253348
R158: 499; R_0402_1005Metric; Manufacturer Part CL0402FN499RP; LCSC C48996782
U25: PAC1954T-E_4MX; Manufacturer Part PAC1954T-E/4MX; LCSC C3687526

Connections:
+3V3: C274.2, C277.2, R91.1, R146.2, R150.2, R152.1, R153.1, R155.1, R156.2, U25.2 (VDD), U25.10 (SENSE4+), U25.12 (SENSE1-), U25.14 (SENSE2-)
+3V3_CSI: R153.2, U25.13 (SENSE2+)
+3V3_DISP: R155.2, U25.9 (SENSE4-)
+3V3_PS176: R152.2, U25.11 (SENSE1+)
+5V: U25.8 (SENSE3+)
+5VSB: R154.1
+5V_SG2002: R154.2, U25.7 (SENSE3-)
GND: C274.1, C277.1, R157.2, R158.1, U25.3 (GND), U25.17 (EP)
unnamed: R150.1, U25.1 (SLOW/ALERT1#)
unnamed: R156.1, U25.16 (PWRDN#)
unnamed: R157.1, U25.15 (GPIO/ALERT2#)
unnamed: R158.2, U25.6 (ADDRSEL)
SCL: R91.2, U25.4 (SCL)
SDA: R146.1, U25.5 (SDA)

Notes on the sheet:
550mA max sense for touch display +3V3
~196mA max sense for TC358743 +3V3
Power monitor for: PS176, TC358743, LicheeRV Nano, and touch display
~196mA max sense for PS176 +3V3
Pull up to enable SLOW sampling
Addr: 0010 001
550mA max sense for LicheeRV Nano +5V
