HynixCJR/LZ-1-Backplane/pcb_files/PAC1954_PSU_PD.kicad_sch

## KiCad design pcb_files/PAC1954_PSU_PD.kicad_sch (2026-08-26)

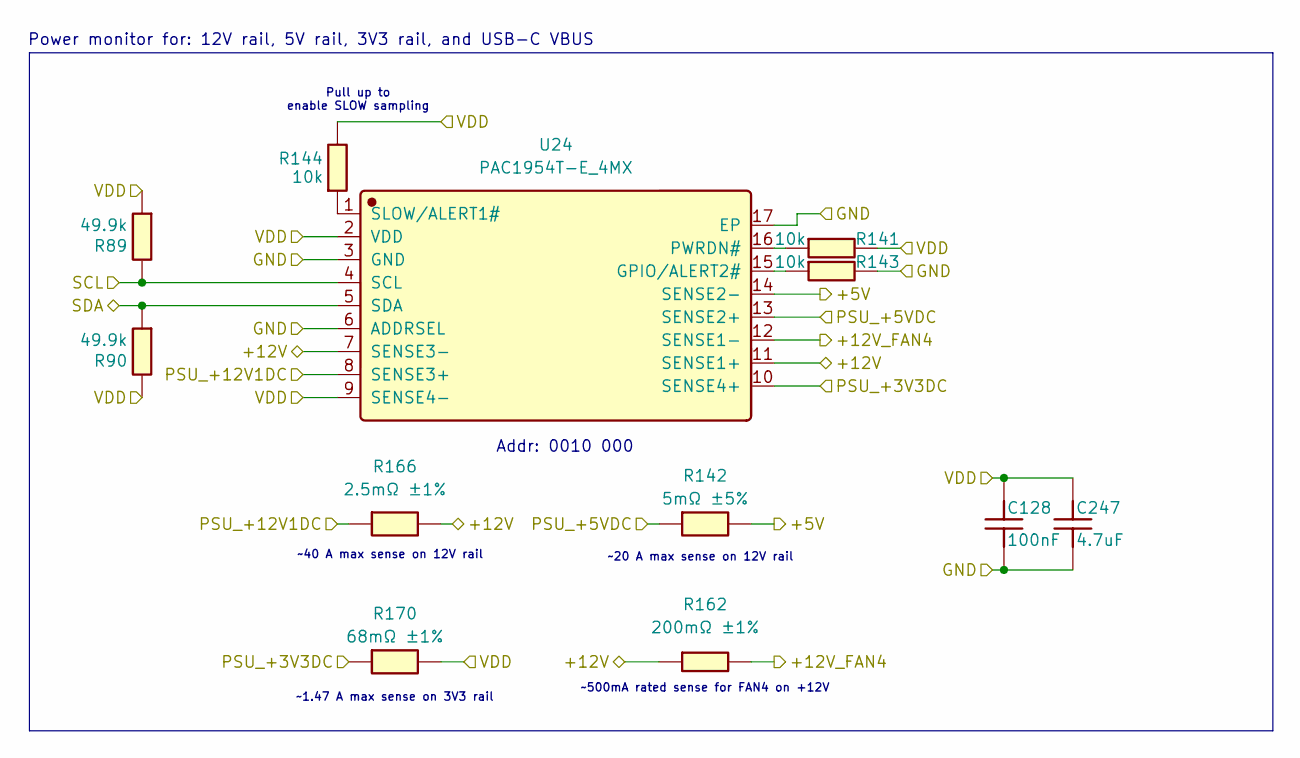
[picture p13: schematic PAC1954_PSU_PD.kicad_sch]

Parts:
C128: 100nF; C_0402_1005Metric; Manufacturer Part CL05B104KB54PNC; LCSC C307331
C247: 4.7uF; C_0402_1005Metric; Manufacturer Part CL05A475MP5NRNC; LCSC C23733
R89, R90: 49.9k; R_0402_1005Metric; Manufacturer Part RMS04FT4992; LCSC C208898
R141, R143, R144: 10k; R_0402_1005Metric; Manufacturer Part 0402WGF1002TCE; LCSC C25744
R142: 5mΩ ±5%; R_1206_3216Metric; Manufacturer Part FMF06JTHR005-LH; LCSC C2874764
R162: 200mΩ ±1%; RL12FTNR200; Manufacturer Part RL12FTNR200; LCSC C160920
R166: 2.5mΩ ±1%; R_2512_6332Metric; Manufacturer Part JER2512F3R2R5L; LCSC C49164684
R170: 68mΩ ±1%; R_1206_3216Metric; Manufacturer Part YHR1206SE1WR068F5; LCSC C42454045
U24: PAC1954T-E_4MX; Manufacturer Part PAC1954T-E/4MX; LCSC C3687526

Connections:
+5V: R142.2, U24.14 (SENSE2-)
+12V: R162.1, R166.2, U24.7 (SENSE3-), U24.11 (SENSE1+)
+12V_FAN4: R162.2, U24.12 (SENSE1-)
GND: C128.1, C247.1, R143.2, U24.3 (GND), U24.6 (ADDRSEL), U24.17 (EP)
unnamed: R141.1, U24.16 (PWRDN#)
unnamed: R143.1, U24.15 (GPIO/ALERT2#)
unnamed: R144.1, U24.1 (SLOW/ALERT1#)
PSU_+3V3DC: R170.1, U24.10 (SENSE4+)
PSU_+5VDC: R142.1, U24.13 (SENSE2+)
PSU_+12V1DC: R166.1, U24.8 (SENSE3+)
SCL: R89.2, U24.4 (SCL)
SDA: R90.1, U24.5 (SDA)
VDD: C128.2, C247.2, R89.1, R90.2, R141.2, R144.2, R170.2, U24.2 (VDD), U24.9 (SENSE4-)

Notes on the sheet:
~40 A max sense on 12V rail
~500mA rated sense for FAN4 on +12V
Addr: 0010 000
Pull up to enable SLOW sampling
~20 A max sense on 12V rail
~1.47 A max sense on 3V3 rail
Power monitor for: 12V rail, 5V rail, 3V3 rail, and USB-C VBUS
