HynixCJR/LZ-1-Backplane/pcb_files/PORT4_USB.kicad_sch

## KiCad design pcb_files/PORT4_USB.kicad_sch (2026-07-31)

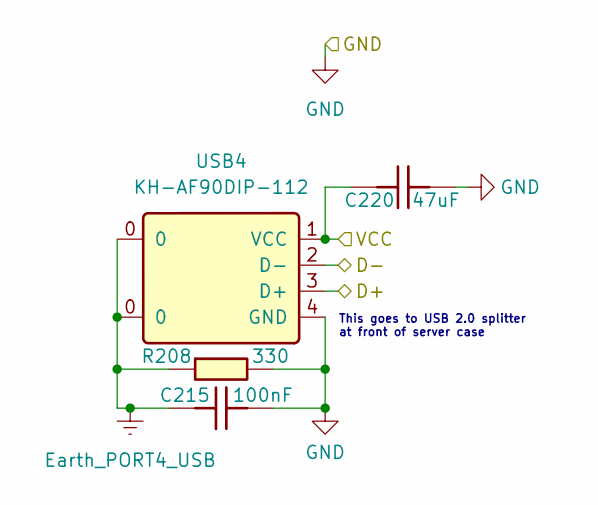
[picture p14: schematic PORT4_USB.kicad_sch]

Parts:
C215: 100nF; C_0402_1005Metric; Manufacturer Part CL05B104KB54PNC; LCSC C307331
C220: 47uF; C_1206_3216Metric; Manufacturer Part CL31A476MPHNNNE; LCSC C96123
R208: 330; R_0402_1005Metric; Manufacturer Part 0402WGF3300TCE; LCSC C25104
USB4: KH-AF90DIP-112; Manufacturer Part KH-AF90DIP-112; LCSC C503996

Connections:
D+: USB4.3 (D+)
D-: USB4.2 (D-)
Earth_PORT4_USB: C215.1, R208.1, USB4.0
GND: C215.2, C220.1, R208.2, USB4.4 (GND)
VCC: C220.2, USB4.1 (VCC)

Notes on the sheet:
This goes to USB 2.0 splitter at front of server case
