HynixCJR/LZ-1-Backplane/pcb_files/PORT5_USB.kicad_sch

## KiCad design pcb_files/PORT5_USB.kicad_sch (2026-08-01)

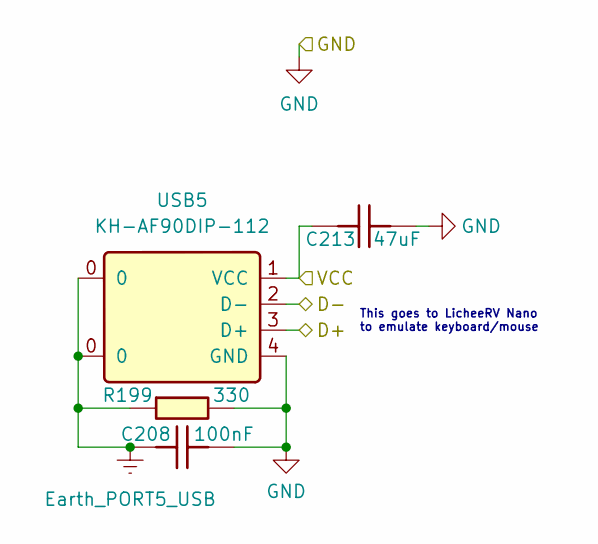
[picture p15: schematic PORT5_USB.kicad_sch]

Parts:
C208: 100nF; C_0402_1005Metric; Manufacturer Part CL05B104KB54PNC; LCSC C307331
C213: 47uF; C_1206_3216Metric; Manufacturer Part CL31A476MPHNNNE; LCSC C96123
R199: 330; R_0402_1005Metric; Manufacturer Part 0402WGF3300TCE; LCSC C25104
USB5: KH-AF90DIP-112; Manufacturer Part KH-AF90DIP-112; LCSC C503996

Connections:
D+: USB5.3 (D+)
D-: USB5.2 (D-)
Earth_PORT5_USB: C208.1, R199.1, USB5.0
GND: C208.2, C213.1, R199.2, USB5.4 (GND)
VCC: C213.2, USB5.1 (VCC)

Notes on the sheet:
This goes to LicheeRV Nano to emulate keyboard/mouse
