HynixCJR/LZ-1-Backplane/pcb_files/PS176.kicad_sch

## KiCad design pcb_files/PS176.kicad_sch (2026-07-25)

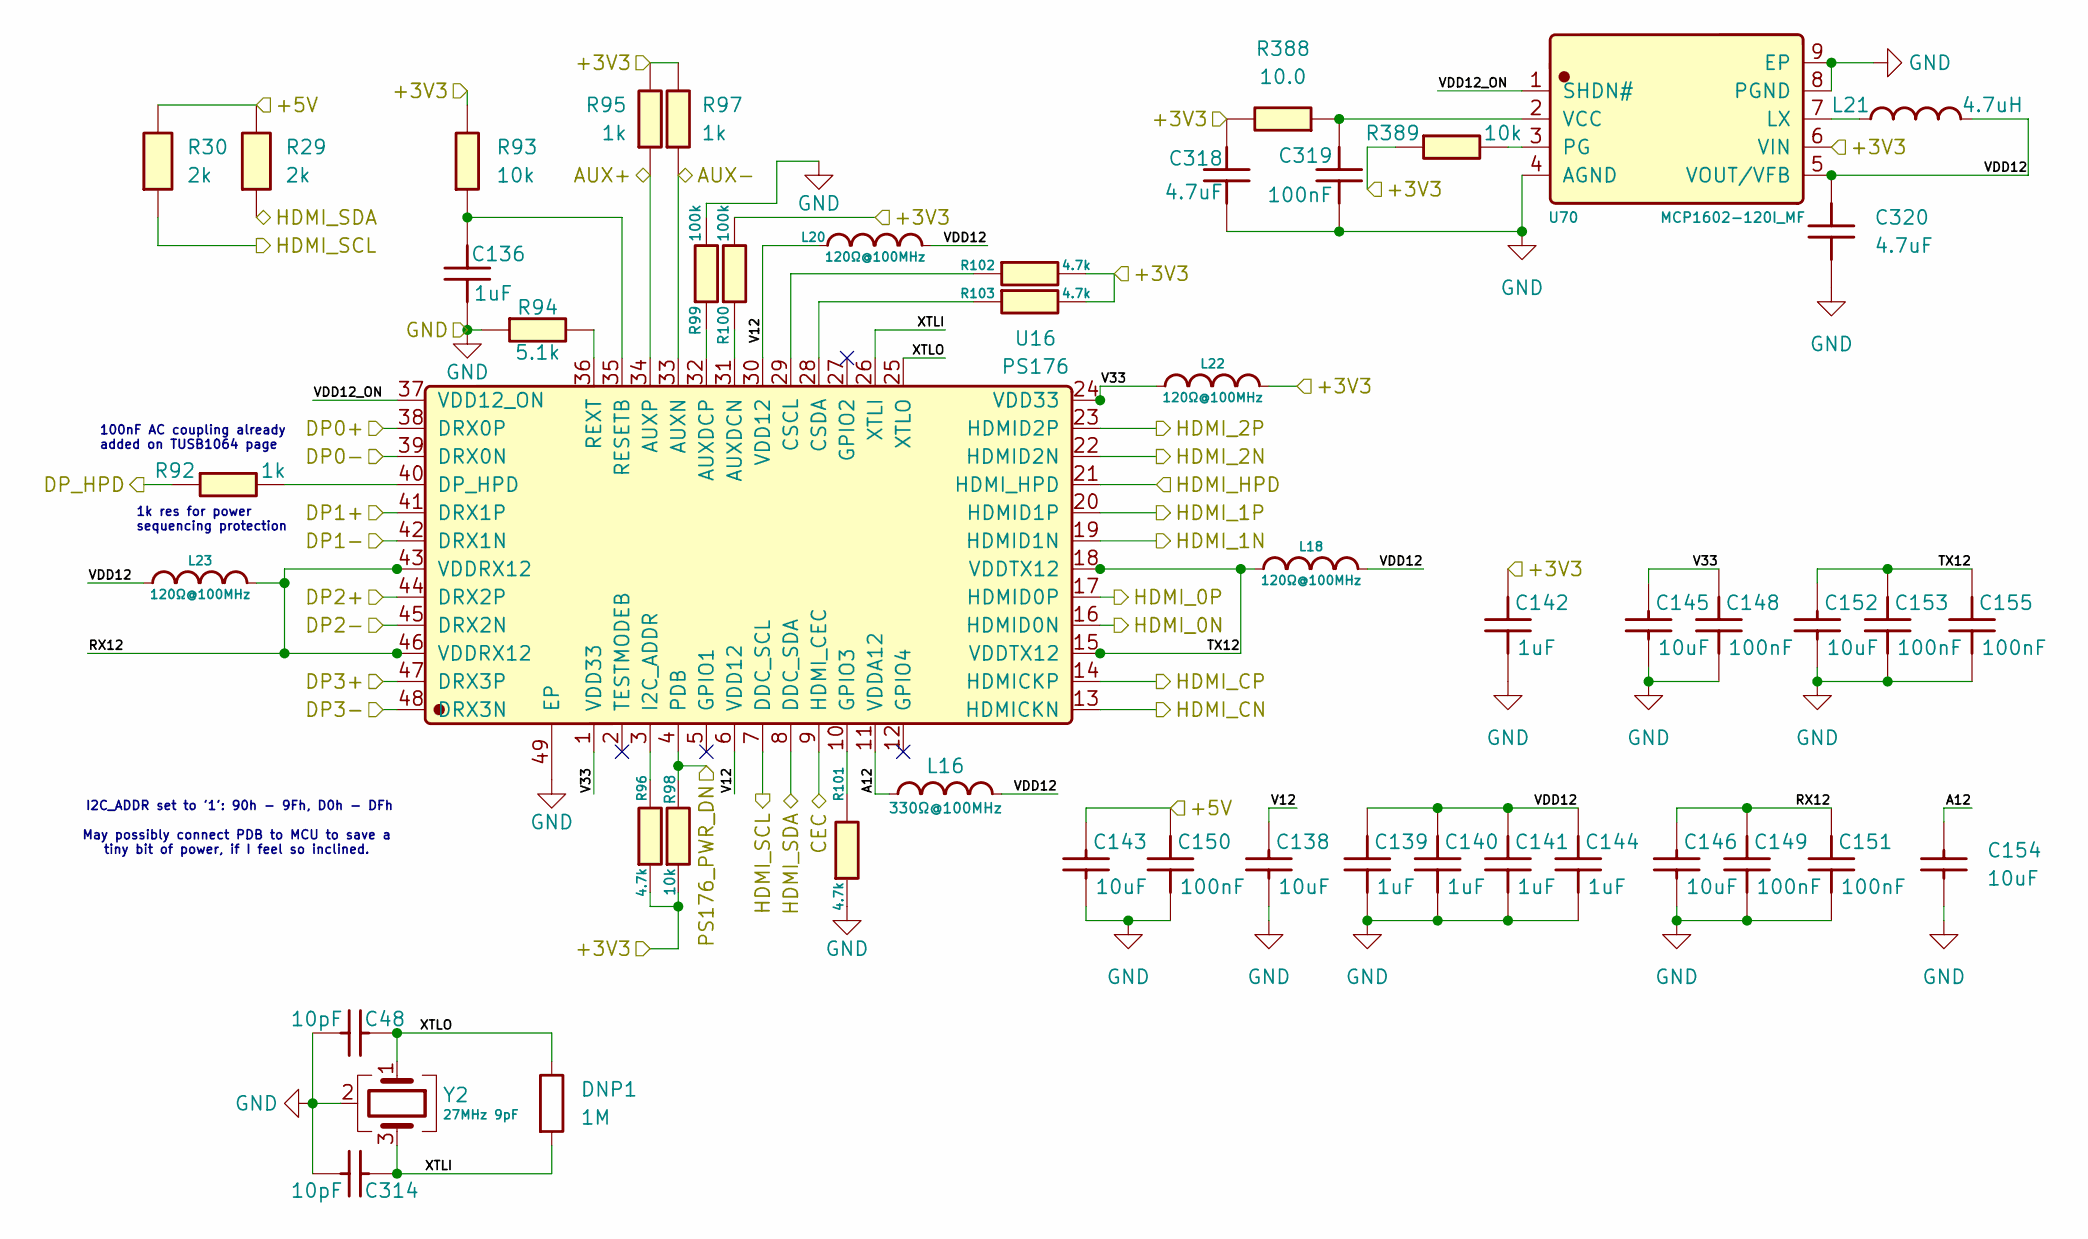
[picture p17: schematic PS176.kicad_sch]

Parts:
C48, C314: 10pF; C_0603_1608Metric; Manufacturer Part CL10C100JB8NNNC; LCSC C1634
C136, C139, C140, C141, C142, C144: 1uF; C_0402_1005Metric; Manufacturer Part CL05A105KA5NQNC; LCSC C52923
C138, C143, C145, C146, C152, C154: 10uF; C_0402_1005Metric; Manufacturer Part CL05A106MQ5NUNC; LCSC C15525
C148, C149, C150, C151, C153, C155, C319: 100nF; C_0402_1005Metric; Manufacturer Part CL05B104KB54PNC; LCSC C307331
C318, C320: 4.7uF; C_0402_1005Metric; Manufacturer Part CL05A475MP5NRNC; LCSC C23733
DNP1: 1M; R_0402_1005Metric
L16: 330Ω@100MHz; BLM18KG331SN1D; Manufacturer Part BLM18KG331SN1D; LCSC C85832
L18, L20, L22, L23: 120Ω@100MHz; L_0805_2012Metric; Manufacturer Part GDPZ2012M121-4A0TF; LCSC C51018428
L21: 4.7uH; PIM201608S4R7MBCA; Manufacturer Part PIM201608S4R7MBCA; LCSC C53514738
R29, R30: 2k; R_0402_1005Metric; Manufacturer Part 1RC0402J0202; LCSC C54531046
R92: 1k; R_0402_1005Metric; Manufacturer Part 0402WGF1001TCE; LCSC C11702
R93, R98, R389: 10k; R_0402_1005Metric; Manufacturer Part 0402WGF1002TCE; LCSC C25744
R94: 5.1k; R_0402_1005Metric; Manufacturer Part 0402WGF5101TCE; LCSC C25905
R95, R97: 1k; R_0402_1005Metric; Manufacturer Part 0402WGF5101TCE; LCSC C25905
R96, R101, R102, R103: 4.7k; R_0402_1005Metric; Manufacturer Part 0402WGF4701TCE; LCSC C25900
R99, R100: 100k; R_0402_1005Metric; Manufacturer Part 0402WGF1003TCE; LCSC C25741
R388: 10.0; R_0402_1005Metric; Manufacturer Part 0402WGF100JTCE; LCSC C25077
U16: PS176; Manufacturer Part PS176; LCSC C209703
U70: MCP1602-120I_MF; Manufacturer Part MCP1602-120I/MF; LCSC C635082
Y2: 27MHz 9pF; Crystal_SMD_3225-4Pin_3.2x2.5mm; MPN XTM32027000FT00351001; LCSC C37635384

Connections:
+3V3: C142.2, C318.2, L22.2, R93.2, R95.2, R96.1, R97.2, R98.1, R100.2, R102.2, R103.2, R388.2, R389.1, U70.6 (VIN)
+5V: C143.2, C150.2, R29.2, R30.2
A12: C154.2, L16.1, U16.11 (VDDA12)
AUX+: R95.1, U16.34 (AUXP)
AUX-: R97.1, U16.33 (AUXN)
CEC: U16.9 (HDMI_CEC)
DP0+: U16.38 (DRX0P)
DP0-: U16.39 (DRX0N)
DP1+: U16.41 (DRX1P)
DP1-: U16.42 (DRX1N)
DP2+: U16.44 (DRX2P)
DP2-: U16.45 (DRX2N)
DP3+: U16.47 (DRX3P)
DP3-: U16.48 (DRX3N)
DP_HPD: R92.1
GND: C48.1, C136.1, C138.1, C139.1, C140.1, C141.1, C142.1, C143.1, C144.1, C145.1, C146.1, C148.1, C149.1, C150.1, C151.1, C152.1, C153.1, C154.1, C155.1, C314.2, C318.1, C319.1, C320.1, R94.1, R99.2, R101.1, U16.49 (EP), U70.4 (AGND), U70.8 (PGND), U70.9 (EP), Y2.2 (G), Y2.4 (G)
HDMI_0N: U16.16 (HDMID0N)
HDMI_0P: U16.17 (HDMID0P)
HDMI_1N: U16.19 (HDMID1N)
HDMI_1P: U16.20 (HDMID1P)
HDMI_2N: U16.22 (HDMID2N)
HDMI_2P: U16.23 (HDMID2P)
HDMI_CN: U16.13 (HDMICKN)
HDMI_CP: U16.14 (HDMICKP)
HDMI_HPD: U16.21 (HDMI_HPD)
HDMI_SCL: R30.1, U16.7 (DDC_SCL)
HDMI_SDA: R29.1, U16.8 (DDC_SDA)
unnamed: C136.2, R93.1, U16.35 (RESETB)
unnamed: C319.2, R388.1, U70.2 (VCC)
unnamed: L21.1, U70.7 (LX)
unnamed: R92.2, U16.40 (DP_HPD)
unnamed: R94.2, U16.36 (REXT)
unnamed: R96.2, U16.3 (I2C_ADDR)
unnamed: R99.1, U16.32 (AUXDCP)
unnamed: R100.1, U16.31 (AUXDCN)
unnamed: R101.2, U16.10 (GPIO3)
unnamed: R102.1, U16.29 (CSCL)
unnamed: R103.1, U16.28 (CSDA)
unnamed: R389.2, U70.3 (PG)
PS176_PWR_DN: R98.2, U16.4 (PDB)
RX12: C146.2, C149.2, C151.2, L23.2, U16.43 (VDDRX12), U16.46 (VDDRX12)
TX12: C152.2, C153.2, C155.2, L18.1, U16.15 (VDDTX12), U16.18 (VDDTX12)
V12: C138.2, L20.1, U16.6 (VDD12), U16.30 (VDD12)
V33: C145.2, C148.2, L22.1, U16.1 (VDD33), U16.24 (VDD33)
VDD12: C139.2, C140.2, C141.2, C144.2, C320.2, L16.2, L18.2, L20.2, L21.2, L23.1, U70.5 (VOUT/VFB)
VDD12_ON: U16.37 (VDD12_ON), U70.1 (SHDN#)
XTLI: C314.1, DNP1.2, U16.26 (XTLI), Y2.3
XTLO: C48.2, DNP1.1, U16.25 (XTLO), Y2.1

Notes on the sheet:
1k res for power sequencing protection
May possibly connect PDB to MCU to save a tiny bit of power, if I feel so inclined.
I2C_ADDR set to '1': 90h - 9Fh, D0h - DFh
100nF AC coupling already added on TUSB1064 page
