HynixCJR/LZ-1-Backplane/pcb_files/PSU_CONN.kicad_sch

## KiCad design pcb_files/PSU_CONN.kicad_sch (2026-07-21)

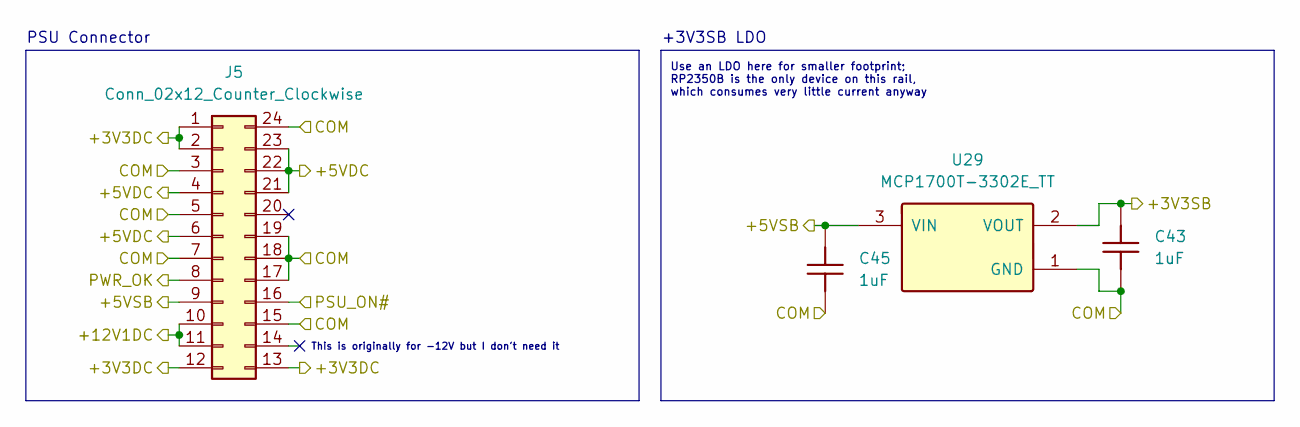
[picture p18: schematic PSU_CONN.kicad_sch]

Parts:
C43, C45: 1uF; C_0402_1005Metric; Manufacturer Part CL05A105KA5NQNC; LCSC C52923
J5: Conn_02x12_Counter_Clockwise; Molex_Mini-Fit_Jr_5566-24A_2x12_P4.20mm_Vertical
U29: MCP1700T-3302E_TT; Manufacturer Part MCP1700T-3302E/TT; LCSC C39051

Connections:
+3V3DC: J5.1, J5.2, J5.12, J5.13
+3V3SB: C43.2, U29.2 (VOUT)
+5VDC: J5.4, J5.6, J5.21, J5.22, J5.23
+5VSB: C45.2, J5.9, U29.3 (VIN)
+12V1DC: J5.10, J5.11
COM: C43.1, C45.1, J5.3, J5.5, J5.7, J5.15, J5.17, J5.18, J5.19, J5.24, U29.1 (GND)
PSU_ON#: J5.16
PWR_OK: J5.8

Notes on the sheet:
This is originally for -12V but I don't need it
Use an LDO here for smaller footprint; RP2350B is the only device on this rail, which consumes very little current anyway
PSU Connector
+3V3SB LDO
