HynixCJR/LZ-1-Backplane/pcb_files/RP2350B_0.kicad_sch

## KiCad design pcb_files/RP2350B_0.kicad_sch (2026-08-26)

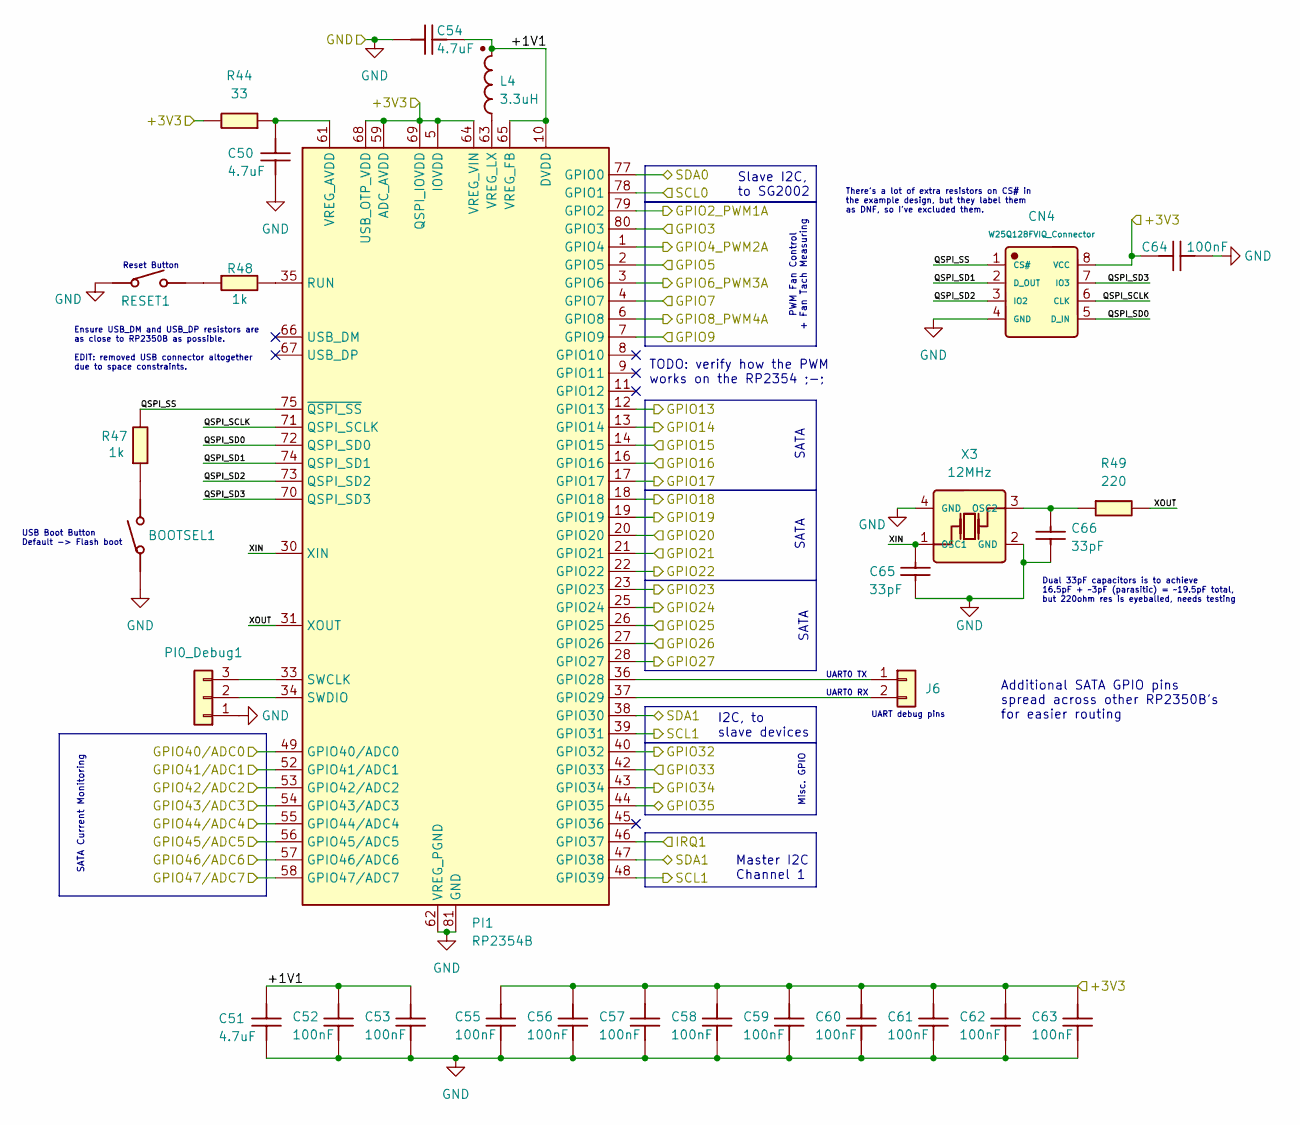
[picture p19: schematic RP2350B_0.kicad_sch]

Parts:
BOOTSEL1: TS-1088-AR02016; Manufacturer Part TS-1088-AR02016; LCSC C720477
C50, C51, C54: 4.7uF; C_0402_1005Metric; Manufacturer Part CL05A475MP5NRNC; LCSC C23733
C52, C53, C55, C56, C57, C58, C59, C60, C61, C62, C63, C64: 100nF; C_0402_1005Metric; Manufacturer Part CL05B104KB54PNC; LCSC C307331
C65, C66: 33pF; C_0402_1005Metric; Manufacturer Part 0402CG330J500NT; LCSC C1562
CN4: W25Q128FVIQ_Connector; H2541FV-C762-2X04P; Manufacturer Part H2541FV-C762-2x04P; LCSC C22387106
J6: Conn_01x02; PinHeader_1x02_P2.54mm_Vertical
L4: 3.3uH; AOTA-B201610S3R3-101-T; Manufacturer Part AOTA-B201610S3R3-101-T; LCSC C42411119
PI0_Debug1: Conn_01x03; PinHeader_1x03_P2.54mm_Vertical
PI1: RP2354B; RP2350B_C42415655
R44: 33; R_0402_1005Metric; Manufacturer Part 0402WGF330JTCE; LCSC C25105
R47, R48: 1k; R_0402_1005Metric; Manufacturer Part 0402WGF1001TCE; LCSC C11702
R49: 220; R_0603_1608Metric; Manufacturer Part 0603WAF2200T5E; LCSC C22962
RESET1: TS-1088-AR02016; Manufacturer Part TS-1088-AR02016; LCSC C720477
X3: 12MHz; X322512MSB4SI; Manufacturer Part X322512MSB4SI; LCSC C9002

Connections:
+1V1: C51.1, C52.2, C53.2, C54.2, L4.2, PI1.10 (DVDD), PI1.32 (DVDD), PI1.51 (DVDD), PI1.65 (VREG_FB)
+3V3: C55.2, C56.2, C57.2, C58.2, C59.2, C60.2, C61.2, C62.2, C63.2, C64.2, CN4.8 (VCC), PI1.5 (IOVDD), PI1.15 (IOVDD), PI1.24 (IOVDD), PI1.29 (IOVDD), PI1.41 (IOVDD), PI1.50 (IOVDD), PI1.59 (ADC_AVDD), PI1.60 (IOVDD), PI1.64 (VREG_VIN), PI1.68 (USB_OTP_VDD), PI1.69 (QSPI_IOVDD), PI1.76 (IOVDD), R44.2
GND: BOOTSEL1.1, C50.2, C51.2, C52.1, C53.1, C54.1, C55.1, C56.1, C57.1, C58.1, C59.1, C60.1, C61.1, C62.1, C63.1, C64.1, C65.1, C66.1, CN4.4 (GND), PI0_Debug1.1, PI1.62 (VREG_PGND), PI1.81 (GND), RESET1.1, X3.2 (GND), X3.4 (GND)
GPIO2_PWM1A: PI1.79 (GPIO2)
GPIO3: PI1.80 (GPIO3)
GPIO4_PWM2A: PI1.1 (GPIO4)
GPIO5: PI1.2 (GPIO5)
GPIO6_PWM3A: PI1.3 (GPIO6)
GPIO7: PI1.4 (GPIO7)
GPIO8_PWM4A: PI1.6 (GPIO8)
GPIO9: PI1.7 (GPIO9)
GPIO13: PI1.12 (GPIO13)
GPIO14: PI1.13 (GPIO14)
GPIO15: PI1.14 (GPIO15)
GPIO16: PI1.16 (GPIO16)
GPIO17: PI1.17 (GPIO17)
GPIO18: PI1.18 (GPIO18)
GPIO19: PI1.19 (GPIO19)
GPIO20: PI1.20 (GPIO20)
GPIO21: PI1.21 (GPIO21)
GPIO22: PI1.22 (GPIO22)
GPIO23: PI1.23 (GPIO23)
GPIO24: PI1.25 (GPIO24)
GPIO25: PI1.26 (GPIO25)
GPIO26: PI1.27 (GPIO26)
GPIO27: PI1.28 (GPIO27)
GPIO32: PI1.40 (GPIO32)
GPIO33: PI1.42 (GPIO33)
GPIO34: PI1.43 (GPIO34)
GPIO35: PI1.44 (GPIO35)
GPIO40/ADC0: PI1.49 (GPIO40/ADC0)
GPIO41/ADC1: PI1.52 (GPIO41/ADC1)
GPIO42/ADC2: PI1.53 (GPIO42/ADC2)
GPIO43/ADC3: PI1.54 (GPIO43/ADC3)
GPIO44/ADC4: PI1.55 (GPIO44/ADC4)
GPIO45/ADC5: PI1.56 (GPIO45/ADC5)
GPIO46/ADC6: PI1.57 (GPIO46/ADC6)
GPIO47/ADC7: PI1.58 (GPIO47/ADC7)
IRQ1: PI1.46 (GPIO37)
unnamed: BOOTSEL1.2, R47.1
unnamed: C50.1, PI1.61 (VREG_AVDD), R44.1
unnamed: C66.2, R49.1, X3.3 (OSC2)
unnamed: J6.1, PI1.36 (GPIO28)
unnamed: J6.2, PI1.37 (GPIO29)
unnamed: L4.1, PI1.63 (VREG_LX)
unnamed: PI0_Debug1.2, PI1.34 (SWDIO)
unnamed: PI0_Debug1.3, PI1.33 (SWCLK)
unnamed: PI1.35 (RUN), R48.2
unnamed: R48.1, RESET1.2
QSPI_SCLK: CN4.6 (CLK), PI1.71 (QSPI_SCLK)
QSPI_SD0: CN4.5 (D_IN), PI1.72 (QSPI_SD0)
QSPI_SD1: CN4.2 (D_OUT), PI1.74 (QSPI_SD1)
QSPI_SD2: CN4.3 (IO2), PI1.73 (QSPI_SD2)
QSPI_SD3: CN4.7 (IO3), PI1.70 (QSPI_SD3)
QSPI_SS: CN4.1 (CS#), PI1.75 (~QSPI_SS), R47.2
SCL0: PI1.78 (GPIO1)
SCL1: PI1.39 (GPIO31), PI1.48 (GPIO39)
SDA0: PI1.77 (GPIO0)
SDA1: PI1.38 (GPIO30), PI1.47 (GPIO38)
XIN: C65.2, PI1.30 (XIN), X3.1 (OSC1)
XOUT: PI1.31 (XOUT), R49.2

Notes on the sheet:
Additional SATA GPIO pins spread across other RP2350B's for easier routing
Reset Button
I2C, to slave devices
Dual 33pF capacitors is to achieve 16.5pF + ~3pF (parasitic) = ~19.5pF total, but 220ohm res is eyeballed, needs testing
UART debug pins
SATA
There's a lot of extra resistors on CS# in the example design, but they label them as DNF, so I've excluded them.
TODO: verify how the PWM works on the RP2354 ;-;
Ensure USB_DM and USB_DP resistors are as close to RP2350B as possible. EDIT: removed USB connector altogether due to space constraints.
Misc. GPIO
Slave I2C, to SG2002
PWM Fan Control + Fan Tach Measuring
SATA Current Monitoring
UART0 TX
USB Boot Button Default -> Flash boot
UART0 RX
Master I2C Channel 1
