HynixCJR/LZ-1-Backplane/pcb_files/RP2354B_0.kicad_sch

## KiCad design pcb_files/RP2354B_0.kicad_sch (2026-08-20)

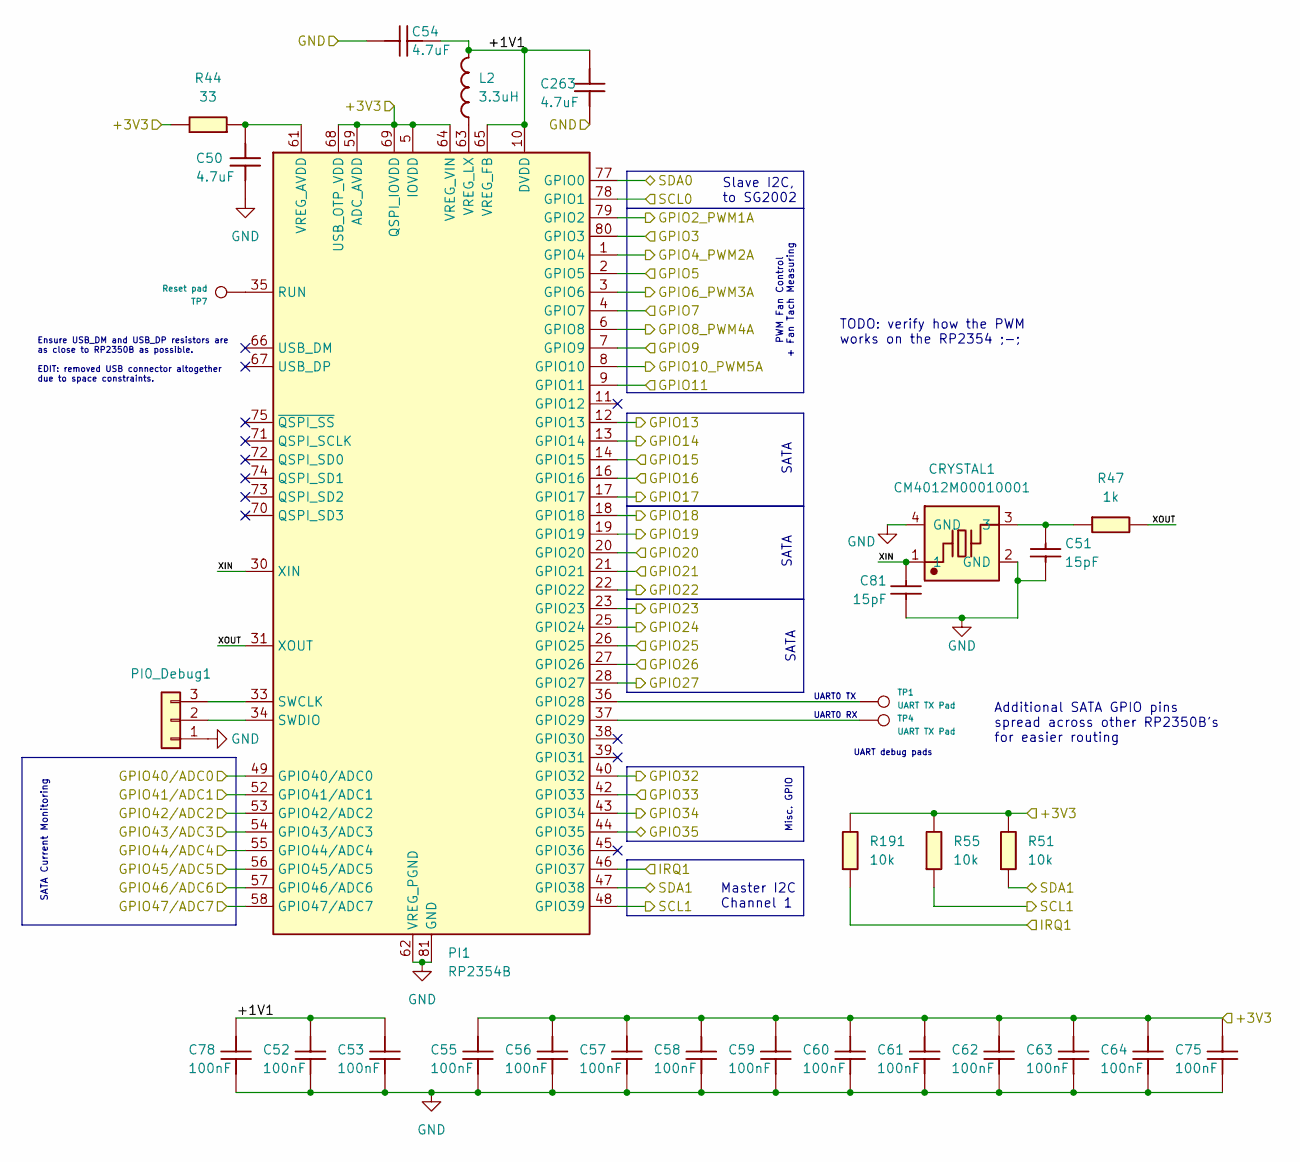
[picture p20: schematic RP2354B_0.kicad_sch]

Parts:
C50, C54, C263: 4.7uF; C_0402_1005Metric; Manufacturer Part CL05A475MP5NRNC; LCSC C23733
C51, C81: 15pF; C_0402_1005Metric; Manufacturer Part 0402CG150J500NT; LCSC C1548
C52, C53, C55, C56, C57, C58, C59, C60, C61, C62, C63, C64, C75, C78: 100nF; C_0402_1005Metric; Manufacturer Part CL05B104KB54PNC; LCSC C307331
CRYSTAL1: CM4012M00010001; Crystal_SMD_2520-4Pin_2.5x2.0mm; Manufacturer Part CM4012M00010001; LCSC C7294610
L2: 3.3uH; PIM252010S3R3MBCA; Manufacturer Part PIM252010S3R3MBCA; LCSC C53514805
PI0_Debug1: Conn_01x03; PinHeader_1x03_P2.54mm_Vertical
PI1: RP2354B; RP2350B_C42415655; LCSC C39843328
R44: 33; R_0402_1005Metric; Manufacturer Part 0402WGF330JTCE; LCSC C25105
R47: 1k; R_0402_1005Metric; Manufacturer Part 0402WGF1001TCE; LCSC C11702
R51, R55, R191: 10k; R_0402_1005Metric; Manufacturer Part 0402WGF1002TCE; LCSC C25744
TP1, TP4: UART TX Pad; TestPoint_Pad_2.0x2.0mm
TP7: Reset pad; TestPoint_Pad_2.0x2.0mm

Connections:
+1V1: C52.2, C53.2, C54.2, C78.2, C263.1, L2.2, PI1.10 (DVDD), PI1.32 (DVDD), PI1.51 (DVDD), PI1.65 (VREG_FB)
+3V3: C55.2, C56.2, C57.2, C58.2, C59.2, C60.2, C61.2, C62.2, C63.2, C64.2, C75.2, PI1.5 (IOVDD), PI1.15 (IOVDD), PI1.24 (IOVDD), PI1.29 (IOVDD), PI1.41 (IOVDD), PI1.50 (IOVDD), PI1.59 (ADC_AVDD), PI1.60 (IOVDD), PI1.64 (VREG_VIN), PI1.68 (USB_OTP_VDD), PI1.69 (QSPI_IOVDD), PI1.76 (IOVDD), R44.2, R51.2, R55.2, R191.2
GND: C50.2, C51.1, C52.1, C53.1, C54.1, C55.1, C56.1, C57.1, C58.1, C59.1, C60.1, C61.1, C62.1, C63.1, C64.1, C75.1, C78.1, C81.1, C263.2, CRYSTAL1.2 (GND), CRYSTAL1.4 (GND), PI0_Debug1.1, PI1.62 (VREG_PGND), PI1.81 (GND)
GPIO2_PWM1A: PI1.79 (GPIO2)
GPIO3: PI1.80 (GPIO3)
GPIO4_PWM2A: PI1.1 (GPIO4)
GPIO5: PI1.2 (GPIO5)
GPIO6_PWM3A: PI1.3 (GPIO6)
GPIO7: PI1.4 (GPIO7)
GPIO8_PWM4A: PI1.6 (GPIO8)
GPIO9: PI1.7 (GPIO9)
GPIO10_PWM5A: PI1.8 (GPIO10)
GPIO11: PI1.9 (GPIO11)
GPIO13: PI1.12 (GPIO13)
GPIO14: PI1.13 (GPIO14)
GPIO15: PI1.14 (GPIO15)
GPIO16: PI1.16 (GPIO16)
GPIO17: PI1.17 (GPIO17)
GPIO18: PI1.18 (GPIO18)
GPIO19: PI1.19 (GPIO19)
GPIO20: PI1.20 (GPIO20)
GPIO21: PI1.21 (GPIO21)
GPIO22: PI1.22 (GPIO22)
GPIO23: PI1.23 (GPIO23)
GPIO24: PI1.25 (GPIO24)
GPIO25: PI1.26 (GPIO25)
GPIO26: PI1.27 (GPIO26)
GPIO27: PI1.28 (GPIO27)
GPIO32: PI1.40 (GPIO32)
GPIO33: PI1.42 (GPIO33)
GPIO34: PI1.43 (GPIO34)
GPIO35: PI1.44 (GPIO35)
GPIO40/ADC0: PI1.49 (GPIO40/ADC0)
GPIO41/ADC1: PI1.52 (GPIO41/ADC1)
GPIO42/ADC2: PI1.53 (GPIO42/ADC2)
GPIO43/ADC3: PI1.54 (GPIO43/ADC3)
GPIO44/ADC4: PI1.55 (GPIO44/ADC4)
GPIO45/ADC5: PI1.56 (GPIO45/ADC5)
GPIO46/ADC6: PI1.57 (GPIO46/ADC6)
GPIO47/ADC7: PI1.58 (GPIO47/ADC7)
IRQ1: PI1.46 (GPIO37), R191.1
unnamed: C50.1, PI1.61 (VREG_AVDD), R44.1
unnamed: C51.2, CRYSTAL1.3, R47.1
unnamed: L2.1, PI1.63 (VREG_LX)
unnamed: PI0_Debug1.2, PI1.34 (SWDIO)
unnamed: PI0_Debug1.3, PI1.33 (SWCLK)
unnamed: PI1.35 (RUN), TP7.1
unnamed: PI1.36 (GPIO28), TP1.1
unnamed: PI1.37 (GPIO29), TP4.1
SCL0: PI1.78 (GPIO1)
SCL1: PI1.48 (GPIO39), R55.1
SDA0: PI1.77 (GPIO0)
SDA1: PI1.47 (GPIO38), R51.1
XIN: C81.2, CRYSTAL1.1, PI1.30 (XIN)
XOUT: PI1.31 (XOUT), R47.2

Notes on the sheet:
Additional SATA GPIO pins spread across other RP2350B's for easier routing
UART debug pads
SATA
TODO: verify how the PWM works on the RP2354 ;-;
Ensure USB_DM and USB_DP resistors are as close to RP2350B as possible. EDIT: removed USB connector altogether due to space constraints.
Misc. GPIO
Slave I2C, to SG2002
PWM Fan Control + Fan Tach Measuring
SATA Current Monitoring
UART0 TX
UART0 RX
Master I2C Channel 1
