HynixCJR/LZ-1-Backplane/pcb_files/RTL9210b_0.kicad_sch

## KiCad design pcb_files/RTL9210b_0.kicad_sch (2026-07-22)

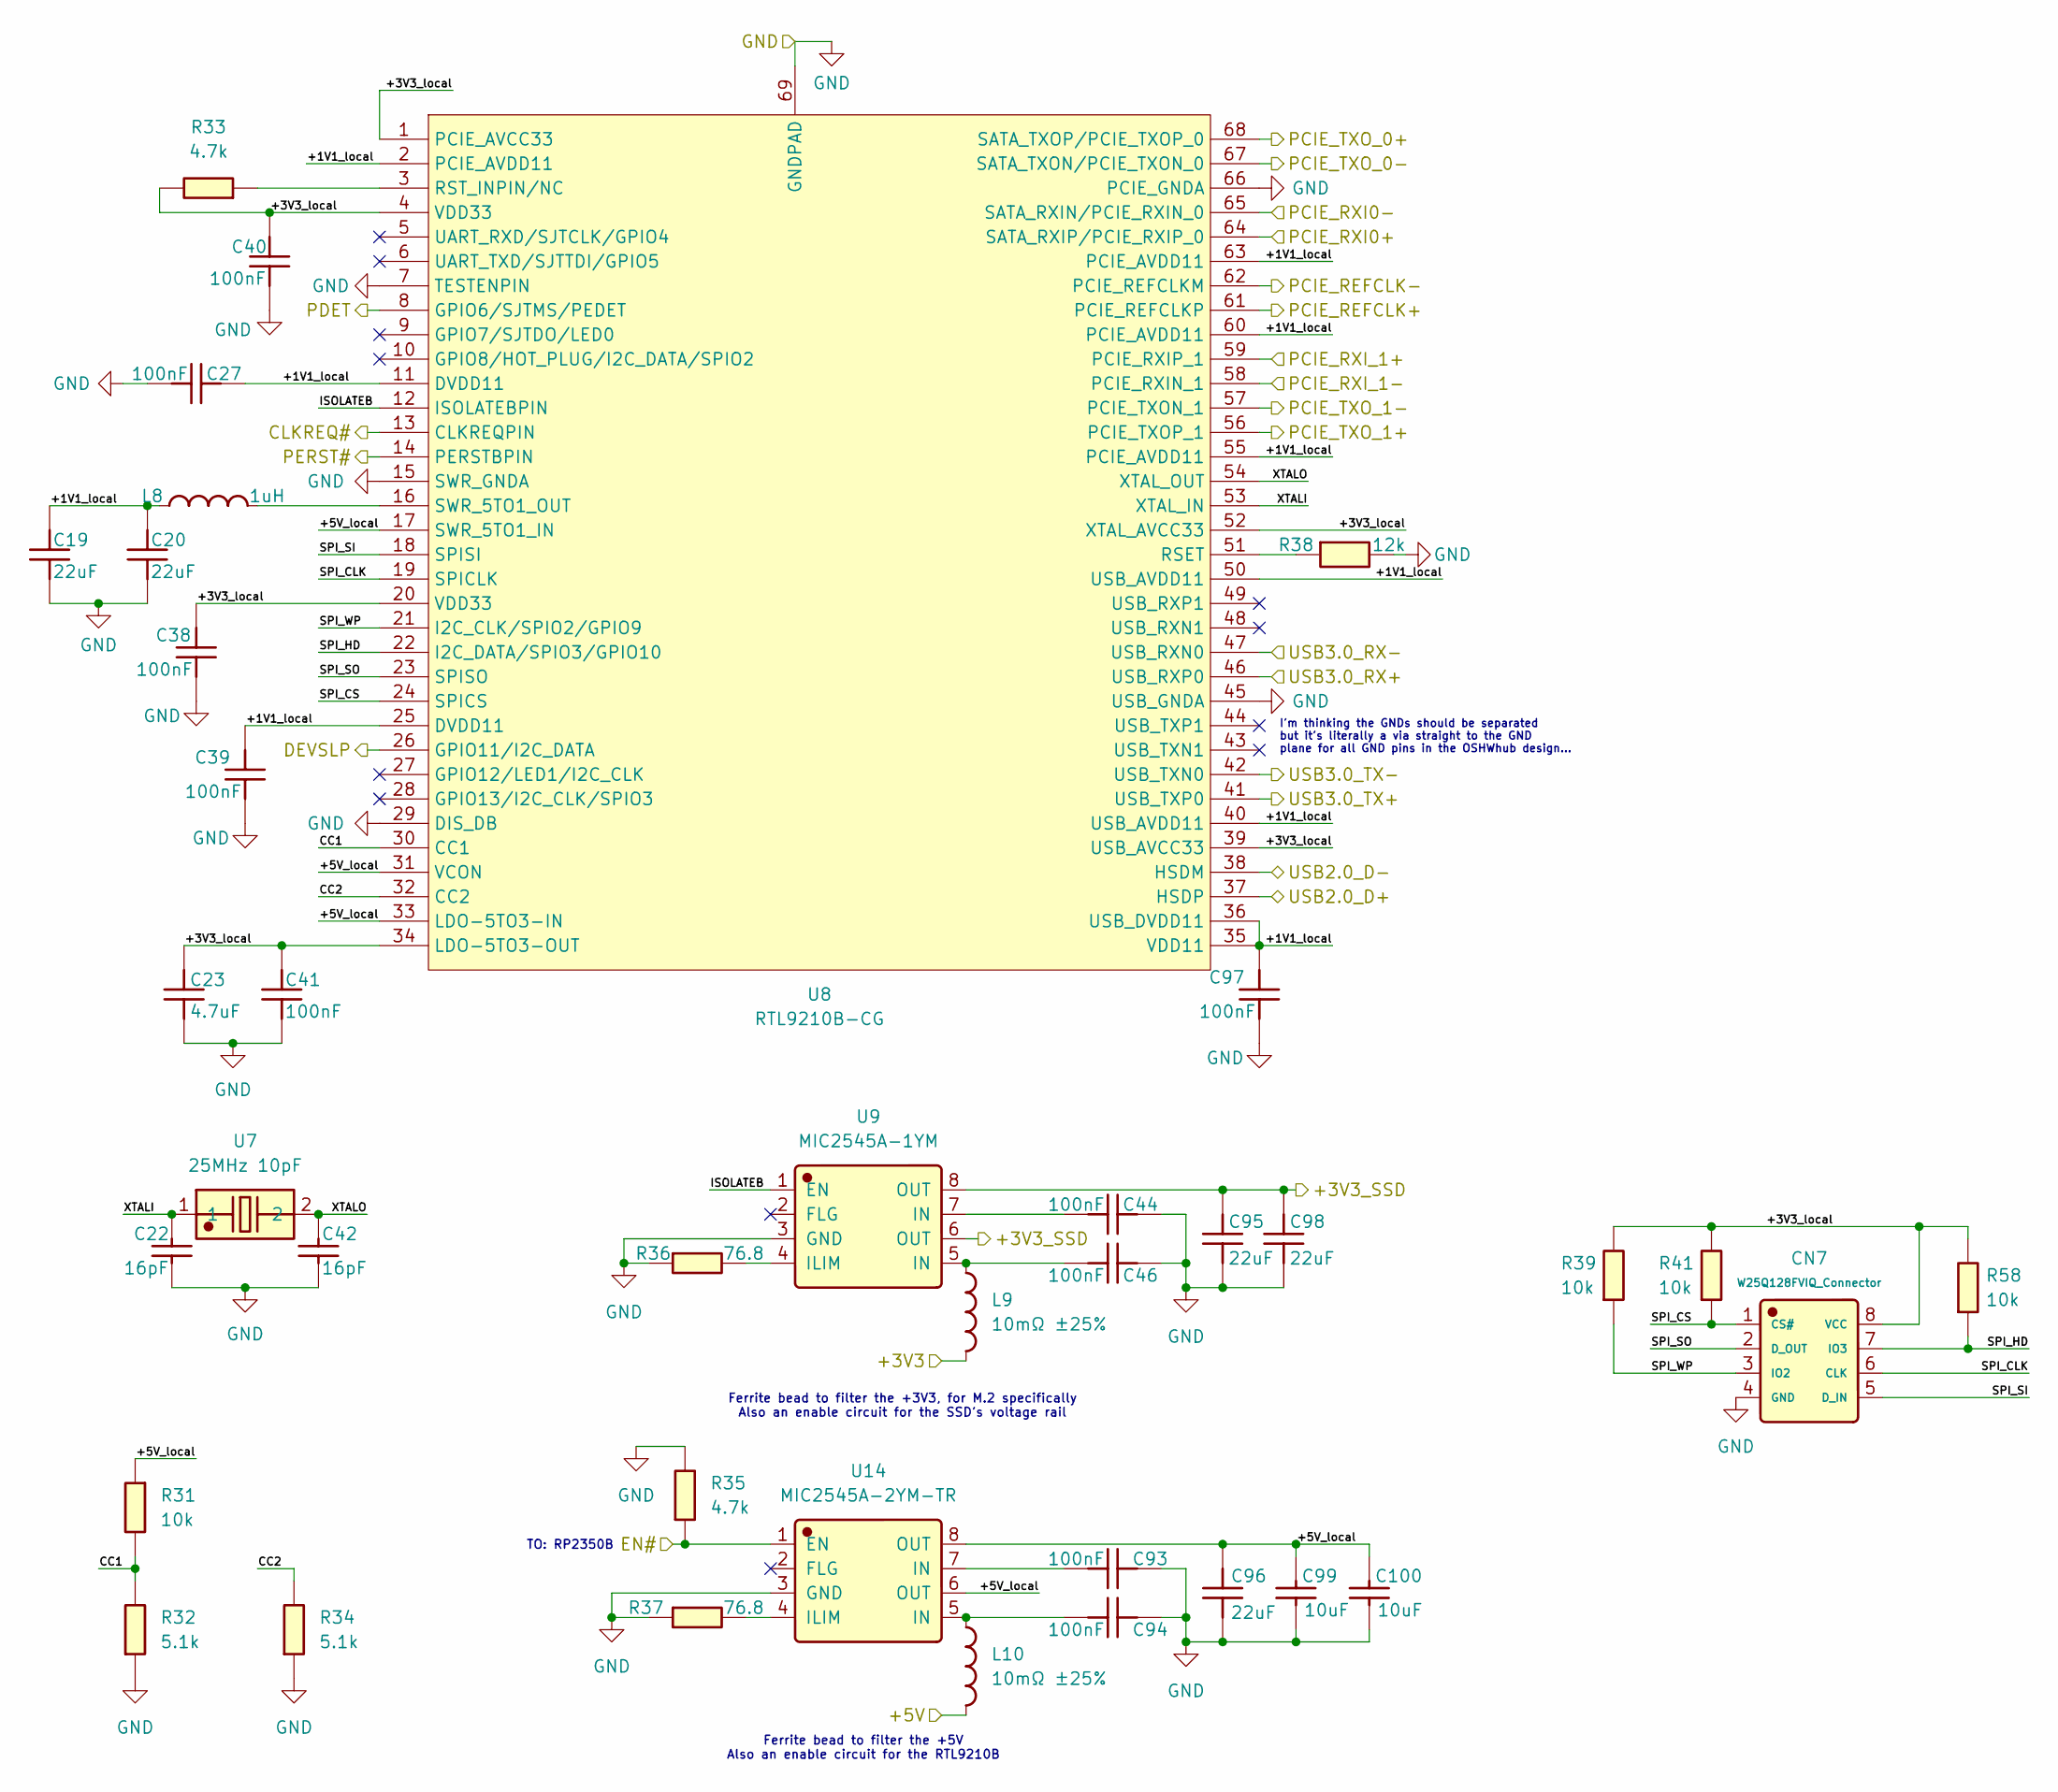
[picture p21: schematic RTL9210b_0.kicad_sch]

Parts:
C19, C20, C95, C96, C98: 22uF; C_0603_1608Metric; Manufacturer Part CL10A226MQ8NRNC; LCSC C59461
C22, C42: 16pF; C_0402_1005Metric; Manufacturer Part 0402CG160J500NT; LCSC C48836
C23: 4.7uF; C_0402_1005Metric; Manufacturer Part CL05A475MP5NRNC; LCSC C23733
C27, C38, C39, C40, C41, C44, C46, C93, C94, C97: 100nF; C_0402_1005Metric; Manufacturer Part CL05B104KB54PNC; LCSC C307331
C99, C100: 10uF; C_0402_1005Metric; Manufacturer Part CL05A106MQ5NUNC; LCSC C15525
CN7: W25Q128FVIQ_Connector; H2541FV-C762-2X04P; Manufacturer Part H2541FV-C762-2x04P; LCSC C22387106
L8: 1uH; TerminalBlock_Phoenix_PTSM-0,5-2-2,5-V-SMD_1x02-1MP_P2.50mm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; Manufacturer Part PIM252012S1R0MBCA; LCSC C46970566
L9, L10: 10mΩ ±25%; L_1206_3216Metric; Manufacturer Part SRLB.1206.600TT60; LCSC C53309025
R31, R39, R41, R58: 10k; R_0402_1005Metric; Manufacturer Part 0402WGF1002TCE; LCSC C25744
R32, R34: 5.1k; R_0402_1005Metric; Manufacturer Part 0402WGF5101TCE; LCSC C25905
R33, R35: 4.7k; R_0402_1005Metric; Manufacturer Part 0402WGF4701TCE; LCSC C25900
R36, R37: 76.8; R_0402_1005Metric; Manufacturer Part RC-02K76R8FT; LCSC C48971957
R38: 12k; R_0402_1005Metric; Manufacturer Part CR0402F12K0Q10Z; LCSC C881068
U7: 25MHz 10pF; 25M_10PF_50PPM; Manufacturer Part 25M 10PF 50PPM; LCSC C4944018
U8: RTL9210B-CG; QFN-68_L8.0-W8.0-P0.40-BL-EP4.8; MPN RTL9210B-CG; LCSC Part C5143573
U9: MIC2545A-1YM; Manufacturer Part MIC2545A-1YM; LCSC C637455
U14: MIC2545A-2YM-TR; Manufacturer Part MIC2545A-2YM-TR; LCSC C627837

Connections:
+1V1_local: C19.2, C20.2, C27.2, C39.2, C97.2, L8.1, U8.2 (PCIE_AVDD11), U8.11 (DVDD11), U8.25 (DVDD11), U8.35 (VDD11), U8.36 (USB_DVDD11), U8.40 (USB_AVDD11), U8.50 (USB_AVDD11), U8.55 (PCIE_AVDD11), U8.60 (PCIE_AVDD11), U8.63 (PCIE_AVDD11)
+3V3: L9.2
+3V3_SSD: C95.2, C98.2, U9.6 (OUT), U9.8 (OUT)
+3V3_local: C23.2, C38.2, C40.2, C41.2, CN7.8 (VCC), R33.2, R39.2, R41.2, R58.2, U8.1 (PCIE_AVCC33), U8.4 (VDD33), U8.20 (VDD33), U8.34 (LDO-5TO3-OUT), U8.39 (USB_AVCC33), U8.52 (XTAL_AVCC33)
+5V: L10.2
+5V_local: C96.2, C99.2, C100.2, R31.1, U8.17 (SWR_5TO1_IN), U8.31 (VCON), U8.33 (LDO-5TO3-IN), U14.6 (OUT), U14.8 (OUT)
CC1: R31.2, R32.2, U8.30 (CC1)
CC2: R34.2, U8.32 (CC2)
CLKREQ#: U8.13 (CLKREQPIN)
DEVSLP: U8.26 (GPIO11/I2C_DATA)
EN#: R35.1, U14.1 (EN)
GND: C19.1, C20.1, C22.1, C23.1, C27.1, C38.1, C39.1, C40.1, C41.1, C42.1, C44.2, C46.2, C93.2, C94.2, C95.1, C96.1, C97.1, C98.1, C99.1, C100.1, CN7.4 (GND), R32.1, R34.1, R35.2, R36.1, R37.1, R38.2, U8.7 (TESTENPIN), U8.15 (SWR_GNDA), U8.29 (DIS_DB), U8.45 (USB_GNDA), U8.66 (PCIE_GNDA), U8.69 (GNDPAD), U9.3 (GND), U14.3 (GND)
ISOLATEB: U8.12 (ISOLATEBPIN), U9.1 (EN)
unnamed: C44.1, U9.7 (IN)
unnamed: C46.1, L9.1, U9.5 (IN)
unnamed: C93.1, U14.7 (IN)
unnamed: C94.1, L10.1, U14.5 (IN)
unnamed: L8.2, U8.16 (SWR_5TO1_OUT)
unnamed: R33.1, U8.3 (RST_INPIN/NC)
unnamed: R36.2, U9.4 (ILIM)
unnamed: R37.2, U14.4 (ILIM)
unnamed: R38.1, U8.51 (RSET)
PCIE_REFCLK+: U8.61 (PCIE_REFCLKP)
PCIE_REFCLK-: U8.62 (PCIE_REFCLKM)
PCIE_RXI0+: U8.64 (SATA_RXIP/PCIE_RXIP_0)
PCIE_RXI0-: U8.65 (SATA_RXIN/PCIE_RXIN_0)
PCIE_RXI_1+: U8.59 (PCIE_RXIP_1)
PCIE_RXI_1-: U8.58 (PCIE_RXIN_1)
PCIE_TXO_0+: U8.68 (SATA_TXOP/PCIE_TXOP_0)
PCIE_TXO_0-: U8.67 (SATA_TXON/PCIE_TXON_0)
PCIE_TXO_1+: U8.56 (PCIE_TXOP_1)
PCIE_TXO_1-: U8.57 (PCIE_TXON_1)
PDET: U8.8 (GPIO6/SJTMS/PEDET)
PERST#: U8.14 (PERSTBPIN)
SPI_CLK: CN7.6 (CLK), U8.19 (SPICLK)
SPI_CS: CN7.1 (CS#), R41.1, U8.24 (SPICS)
SPI_HD: CN7.7 (IO3), R58.1, U8.22 (I2C_DATA/SPIO3/GPIO10)
SPI_SI: CN7.5 (D_IN), U8.18 (SPISI)
SPI_SO: CN7.2 (D_OUT), U8.23 (SPISO)
SPI_WP: CN7.3 (IO2), R39.1, U8.21 (I2C_CLK/SPIO2/GPIO9)
USB2.0_D+: U8.37 (HSDP)
USB2.0_D-: U8.38 (HSDM)
USB3.0_RX+: U8.46 (USB_RXP0)
USB3.0_RX-: U8.47 (USB_RXN0)
USB3.0_TX+: U8.41 (USB_TXP0)
USB3.0_TX-: U8.42 (USB_TXN0)
XTALI: C22.2, U7.1, U8.53 (XTAL_IN)
XTALO: C42.2, U7.2, U8.54 (XTAL_OUT)

Notes on the sheet:
Ferrite bead to filter the +5V Also an enable circuit for the RTL9210B
Ferrite bead to filter the +3V3, for M.2 specifically Also an enable circuit for the SSD's voltage rail
TO: RP2350B
I'm thinking the GNDs should be separated but it's literally a via straight to the GND plane for all GND pins in the OSHWhub design...
