HynixCJR/LZ-1-Backplane/pcb_files/SATA_PORT_DOWNSTREAM.kicad_sch

## KiCad design pcb_files/SATA_PORT_DOWNSTREAM.kicad_sch (2026-08-04)

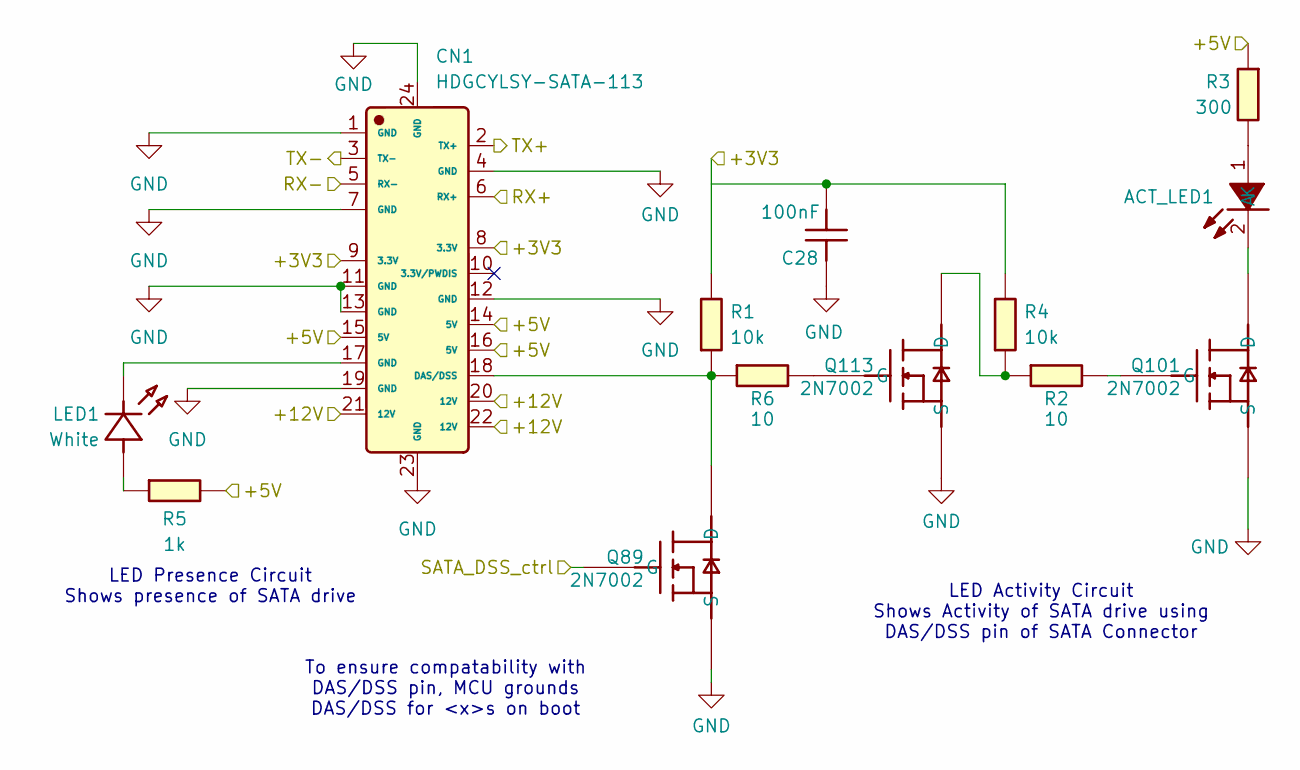
[picture p22: schematic SATA_PORT_DOWNSTREAM.kicad_sch]

Parts:
ACT_LED1: 0805G_Green; Manufacturer Part KT-0805G; LCSC C2297
C28: 100nF; C_0402_1005Metric; Manufacturer Part CL05B104KB54PNC; LCSC C307331
CN1: HDGCYLSY-SATA-113; Manufacturer Part HDGCYLSY-SATA-113; LCSC C22438715
LED1: White; GL0603UW01; Manufacturer Part GL0603UW01; LCSC C51933297
Q89, Q101, Q113: 2N7002; 2N7002_C916396; Manufacturer Part 2N7002; LCSC C916396
R1, R4: 10k; R_0402_1005Metric; Manufacturer Part 0402WGF1002TCE; LCSC C25744
R2, R6: 10; R_0402_1005Metric; Manufacturer Part 0402WGF100JTCE; LCSC C25077
R3: 300; R_0603_1608Metric; Manufacturer Part 0603WAF3000T5E; LCSC C23025
R5: 1k; R_0402_1005Metric; Manufacturer Part 0402WGF1001TCE; LCSC C11702

Connections:
+3V3: CN1.8 (3.3V), CN1.9 (3.3V), R1.2
+5V: CN1.14 (5V), CN1.15 (5V), CN1.16 (5V), R3.1, R5.2
+12V: CN1.20 (12V), CN1.21 (12V), CN1.22 (12V)
GND: C28.1, CN1.1 (GND), CN1.4 (GND), CN1.7 (GND), CN1.11 (GND), CN1.12 (GND), CN1.13 (GND), CN1.19 (GND), CN1.23 (GND), CN1.24 (GND), Q89.2 (S), Q101.2 (S), Q113.2 (S)
unnamed: ACT_LED1.1 (A), R3.2
unnamed: ACT_LED1.2 (K), Q101.3 (D)
unnamed: C28.2, R4.2
unnamed: CN1.17 (GND), LED1.2 (C)
unnamed: CN1.18 (DAS/DSS), Q89.3 (D), R1.1, R6.1
unnamed: LED1.1 (A), R5.1
unnamed: Q101.1 (G), R2.2
unnamed: Q113.1 (G), R6.2
unnamed: Q113.3 (D), R2.1, R4.1
RX+: CN1.6 (RX+)
RX-: CN1.5 (RX-)
SATA_DSS_ctrl: Q89.1 (G)
TX+: CN1.2 (TX+)
TX-: CN1.3 (TX-)

Notes on the sheet:
To ensure compatability with DAS/DSS pin, MCU grounds DAS/DSS for <x>s on boot
LED Activity Circuit Shows Activity of SATA drive using DAS/DSS pin of SATA Connector
LED Presence Circuit Shows presence of SATA drive
