HynixCJR/LZ-1-Backplane/pcb_files/SD_SLOT.kicad_sch

## KiCad design pcb_files/SD_SLOT.kicad_sch (2026-07-19)

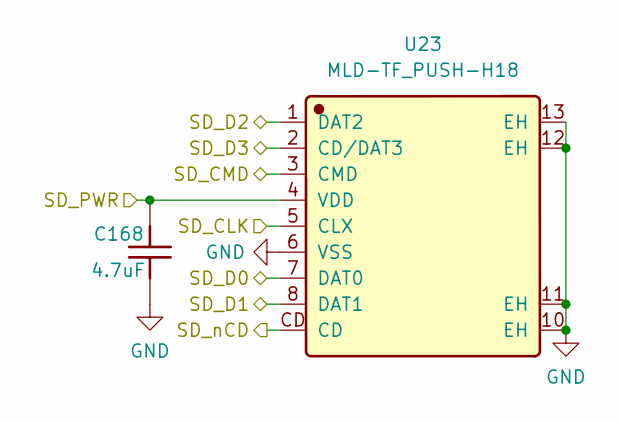
[picture p23: schematic SD_SLOT.kicad_sch]

Parts:
C168: 4.7uF; C_0402_1005Metric; Manufacturer Part CL05A475MP5NRNC; LCSC C23733
U23: MLD-TF_PUSH-H18; Manufacturer Part MLD-TF PUSH-H18; LCSC C52750848

Connections:
GND: C168.1, U23.6 (VSS), U23.10 (EH), U23.11 (EH), U23.12 (EH), U23.13 (EH)
SD_CLK: U23.5 (CLX)
SD_CMD: U23.3 (CMD)
SD_D0: U23.7 (DAT0)
SD_D1: U23.8 (DAT1)
SD_D2: U23.1 (DAT2)
SD_D3: U23.2 (CD/DAT3)
SD_PWR: C168.2, U23.4 (VDD)
SD_nCD: U23.CD
