HynixCJR/LZ-1-Backplane/pcb_files/SG2002_HEADER.kicad_sch

## KiCad design pcb_files/SG2002_HEADER.kicad_sch (2026-08-16)

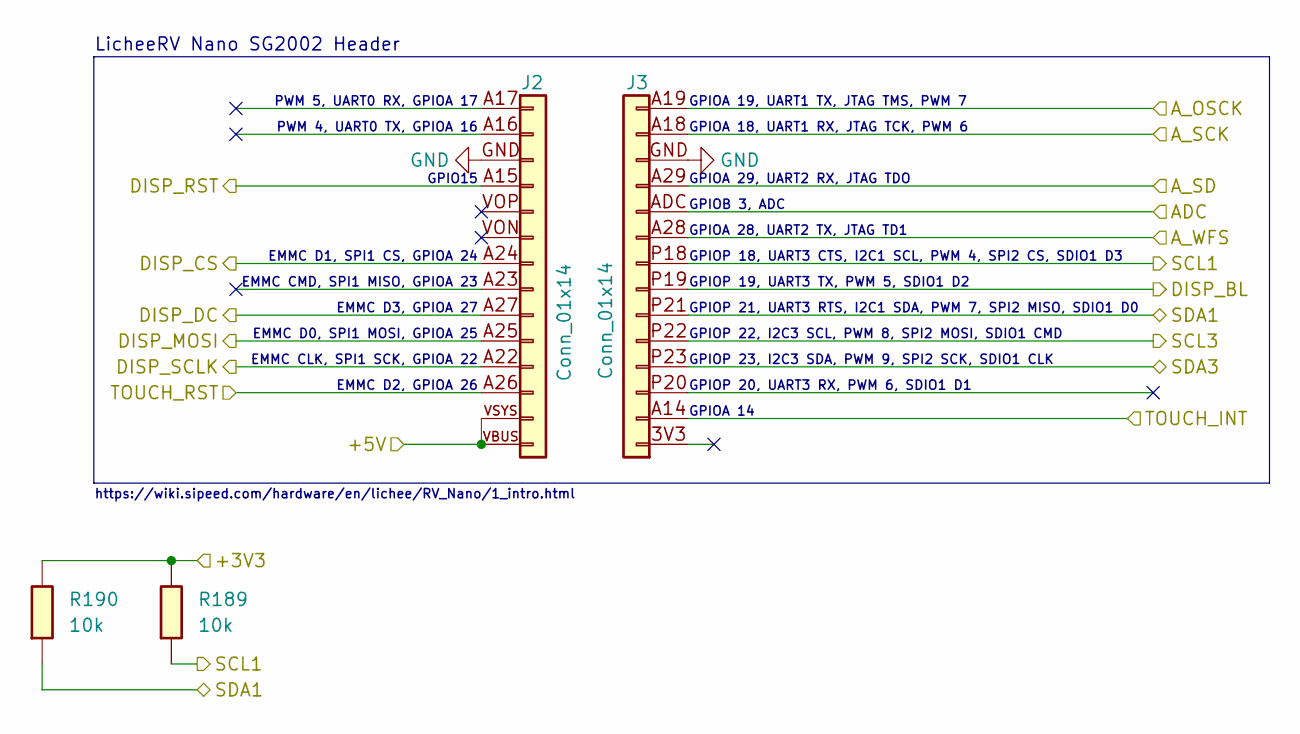
[picture p24: schematic SG2002_HEADER.kicad_sch]

Parts:
J2, J3: Conn_01x14; PinSocket_1x14_P2.54mm_Vertical
R189, R190: 10k; R_0402_1005Metric; Manufacturer Part 0402WGF1002TCE; LCSC C25744

Connections:
+3V3: R189.2, R190.2
+5V: J2.VBUS (Pin_14), J2.VSYS (Pin_13)
ADC: J3.ADC (Pin_10)
A_OSCK: J3.A19 (Pin_14)
A_SCK: J3.A18 (Pin_13)
A_SD: J3.A29 (Pin_11)
A_WFS: J3.A28 (Pin_9)
DISP_BL: J3.P19 (Pin_7)
DISP_CS: J2.A24 (Pin_7)
DISP_DC: J2.A27 (Pin_9)
DISP_MOSI: J2.A25 (Pin_10)
DISP_RST: J2.A15 (Pin_4)
DISP_SCLK: J2.A22 (Pin_11)
GND: J2.GND (Pin_3), J3.GND (Pin_12)
SCL1: J3.P18 (Pin_8), R189.1
SCL3: J3.P22 (Pin_5)
SDA1: J3.P21 (Pin_6), R190.1
SDA3: J3.P23 (Pin_4)
TOUCH_INT: J3.A14 (Pin_2)
TOUCH_RST: J2.A26 (Pin_12)

Notes on the sheet:
EMMC D0, SPI1 MOSI, GPIOA 25
EMMC D2, GPIOA 26
LicheeRV Nano SG2002 Header
EMMC CMD, SPI1 MISO, GPIOA 23
GPIOA 18, UART1 RX, JTAG TCK, PWM 6
https://wiki.sipeed.com/hardware/en/lichee/RV_Nano/1_intro.html
GPIOA 19, UART1 TX, JTAG TMS, PWM 7
GPIOP 20, UART3 RX, PWM 6, SDIO1 D1
GPIOP 23, I2C3 SDA, PWM 9, SPI2 SCK, SDIO1 CLK
EMMC D1, SPI1 CS, GPIOA 24
GPIOA 28, UART2 TX, JTAG TD1
PWM 4, UART0 TX, GPIOA 16
GPIOA 14
GPIOP 18, UART3 CTS, I2C1 SCL, PWM 4, SPI2 CS, SDIO1 D3
PWM 5, UART0 RX, GPIOA 17
EMMC CLK, SPI1 SCK, GPIOA 22
GPIOP 21, UART3 RTS, I2C1 SDA, PWM 7, SPI2 MISO, SDIO1 D0
GPIOB 3, ADC
GPIOA 29, UART2 RX, JTAG TDO
GPIOP 19, UART3 TX, PWM 5, SDIO1 D2
GPIOP 22, I2C3 SCL, PWM 8, SPI2 MOSI, SDIO1 CMD
EMMC D3, GPIOA 27
GPIO15
