HynixCJR/LZ-1-Backplane/pcb_files/TC358743.kicad_sch

## KiCad design pcb_files/TC358743.kicad_sch (2026-08-26)

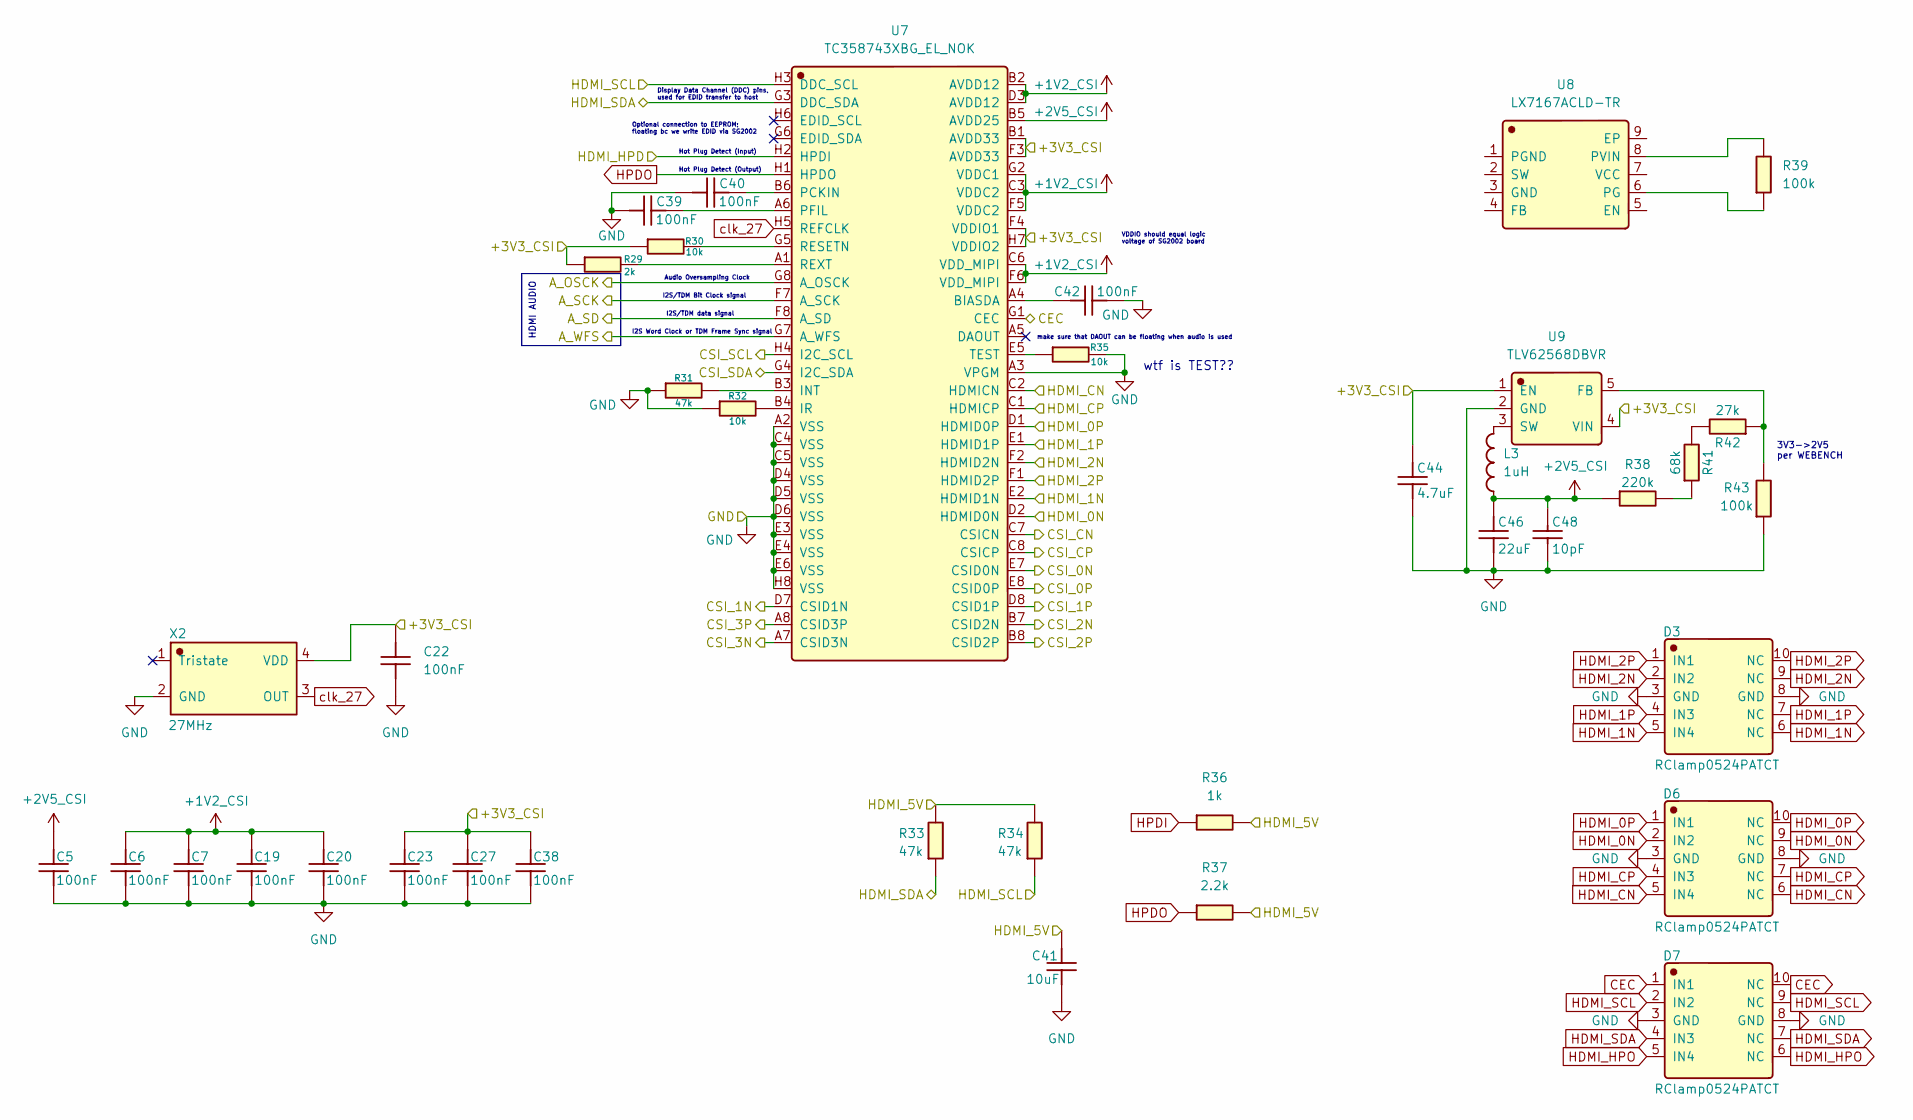
[picture p25: schematic TC358743.kicad_sch]

Parts:
C5, C6, C7, C19, C20, C22, C23, C27, C38, C39, C40, C42: 100nF; C_0402_1005Metric; Manufacturer Part CL05B104KB54PNC; LCSC C307331
C41: 10uF; C_0603_1608Metric; Manufacturer Part CL10A106KP8NNNC; LCSC C19702
C44: 4.7uF; C_0603_1608Metric; Manufacturer Part CL10A475KO8NNNC; LCSC C19666
C46: 22uF; C_0603_1608Metric; Manufacturer Part CL10A226MQ8NRNC; LCSC C59461
C48: 10pF; C_0603_1608Metric; Manufacturer Part CL10C100JB8NNNC; LCSC C1634
D3, D6, D7: RClamp0524PATCT; Manufacturer Part RClAMP0524PATCT; LCSC C40960
L3: 1uH; TerminalBlock_Phoenix_PTSM-0,5-2-2,5-V-SMD_1x02-1MP_P2.50mm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; Manufacturer Part FTC252012S1R0MBCA; LCSC C5832370
R29: 2k; R_0603_1608Metric; Manufacturer Part 0603WAF2001T5E; LCSC C22975
R30, R32, R35: 10k; R_0402_1005Metric; Manufacturer Part 0402WGF1002TCE; LCSC C25744
R31, R33, R34: 47k; R_0402_1005Metric; Manufacturer Part 0402WGF4702TCE; LCSC C25792
R36: 1k; R_0402_1005Metric; Manufacturer Part 0402WGF1001TCE; LCSC C11702
R37: 2.2k; R_0402_1005Metric; Manufacturer Part 0402WGF2201TCE; LCSC C25879
R38: 220k; R_0603_1608Metric; Manufacturer Part 0603WAF2203T5E; LCSC C22961
R39, R43: 100k; R_0402_1005Metric; Manufacturer Part 0402WGF1003TCE; LCSC C25741
R41: 68k; R_0603_1608Metric; Manufacturer Part 0603WAF6802T5E; LCSC C23231
R42: 27k; R_0603_1608Metric; Manufacturer Part 0603WAF2702T5E; LCSC C22967
U7: TC358743XBG_EL_NOK; Manufacturer Part TC358743XBG(EL,NOK; LCSC C3008606
U8: LX7167ACLD-TR; Manufacturer Part LX7167ACLD-TR; LCSC C5229463
U9: TLV62568DBVR; Manufacturer Part TLV62568DBVR; LCSC C163219
X2: 27MHz; Oscillator_SMD_Silicon_Labs_LGA-6_2.5x3.2mm_P1.25mm; Manufacturer Part XOS32027000LT00351005; LCSC C37635418

Connections:
+1V2_CSI: C6.2, C7.2, C19.2, C20.2, U7.B2 (AVDD12), U7.C3 (VDDC2), U7.C6 (VDD_MIPI), U7.D3 (AVDD12), U7.F5 (VDDC2), U7.F6 (VDD_MIPI), U7.G2 (VDDC1)
+2V5_CSI: C5.2, C46.2, C48.2, L3.1, R38.1, U7.B5 (AVDD25)
+3V3_CSI: C22.2, C23.2, C27.2, C38.2, C44.2, R29.1, R30.1, U7.B1 (AVDD33), U7.F3 (AVDD33), U7.F4 (VDDIO1), U7.H7 (VDDIO2), U9.1 (EN), U9.4 (VIN), X2.4 (VDD)
A_OSCK: U7.G8 (A_OSCK)
A_SCK: U7.F7 (A_SCK)
A_SD: U7.F8 (A_SD)
A_WFS: U7.G7 (A_WFS)
CEC: D7.1 (IN1), D7.10 (NC), U7.G1 (CEC)
CSI_0N: U7.E7 (CSID0N)
CSI_0P: U7.E8 (CSID0P)
CSI_1N: U7.D7 (CSID1N)
CSI_1P: U7.D8 (CSID1P)
CSI_2N: U7.B7 (CSID2N)
CSI_2P: U7.B8 (CSID2P)
CSI_3N: U7.A7 (CSID3N)
CSI_3P: U7.A8 (CSID3P)
CSI_CN: U7.C7 (CSICN)
CSI_CP: U7.C8 (CSICP)
CSI_SCL: U7.H4 (I2C_SCL)
CSI_SDA: U7.G4 (I2C_SDA)
GND: C5.1, C6.1, C7.1, C19.1, C20.1, C22.1, C23.1, C27.1, C38.1, C39.1, C40.1, C41.1, C42.2, C44.1, C46.1, C48.1, D3.3 (GND), D3.8 (GND), D6.3 (GND), D6.8 (GND), D7.3 (GND), D7.8 (GND), R31.1, R32.1, R35.2, R43.1, U7.A2 (VSS), U7.A3 (VPGM), U7.C4 (VSS), U7.C5 (VSS), U7.D4 (VSS), U7.D5 (VSS), U7.D6 (VSS), U7.E3 (VSS), U7.E4 (VSS), U7.E6 (VSS), U7.H8 (VSS), U9.2 (GND), X2.2 (GND)
HDMI_0N: D6.2 (IN2), D6.9 (NC), U7.D2 (HDMID0N)
HDMI_0P: D6.1 (IN1), D6.10 (NC), U7.D1 (HDMID0P)
HDMI_1N: D3.5 (IN4), D3.6 (NC), U7.E2 (HDMID1N)
HDMI_1P: D3.4 (IN3), D3.7 (NC), U7.E1 (HDMID1P)
HDMI_2N: D3.2 (IN2), D3.9 (NC), U7.F2 (HDMID2N)
HDMI_2P: D3.1 (IN1), D3.10 (NC), U7.F1 (HDMID2P)
HDMI_5V: C41.2, R33.2, R34.2, R36.2, R37.2
HDMI_CN: D6.5 (IN4), D6.6 (NC), U7.C2 (HDMICN)
HDMI_CP: D6.4 (IN3), D6.7 (NC), U7.C1 (HDMICP)
HDMI_HPD: U7.H2 (HPDI)
HDMI_HPO: D7.5 (IN4), D7.6 (NC)
HDMI_SCL: D7.2 (IN2), D7.9 (NC), R34.1, U7.H3 (DDC_SCL)
HDMI_SDA: D7.4 (IN3), D7.7 (NC), R33.1, U7.G3 (DDC_SDA)
HPDI: R36.1
HPDO: R37.1, U7.H1 (HPDO)
unnamed: C39.2, U7.A6 (PFIL)
unnamed: C40.2, U7.B6 (PCKIN)
unnamed: C42.1, U7.A4 (BIASDA)
unnamed: L3.2, U9.3 (SW)
unnamed: R29.2, U7.A1 (REXT)
unnamed: R30.2, U7.G5 (RESETN)
unnamed: R31.2, U7.B3 (INT)
unnamed: R32.2, U7.B4 (IR)
unnamed: R35.1, U7.E5 (TEST)
unnamed: R38.2, R41.1
unnamed: R39.1, U8.6 (PG)
unnamed: R39.2, U8.8 (PVIN)
unnamed: R41.2, R42.2
unnamed: R42.1, R43.2, U9.5 (FB)
clk_27: U7.H5 (REFCLK), X2.3 (OUT)

Notes on the sheet:
Hot Plug Detect (Output)
wtf is TEST??
Optional connection to EEPROM; floating bc we write EDID via SG2002
VDDIO should equal logic voltage of SG2002 board
make sure that DAOUT can be floating when audio is used
HDMI AUDIO
3V3->2V5 per WEBENCH
Hot Plug Detect (Input)
I2S/TDM Bit Clock signal
I2S Word Clock or TDM Frame Sync signal
Audio Oversampling Clock
Display Data Channel (DDC) pins, used for EDID transfer to host
I2S/TDM data signal
