HynixCJR/LZ-1-Backplane/pcb_files/TPS55288.kicad_sch

## KiCad design pcb_files/TPS55288.kicad_sch (2026-08-17)

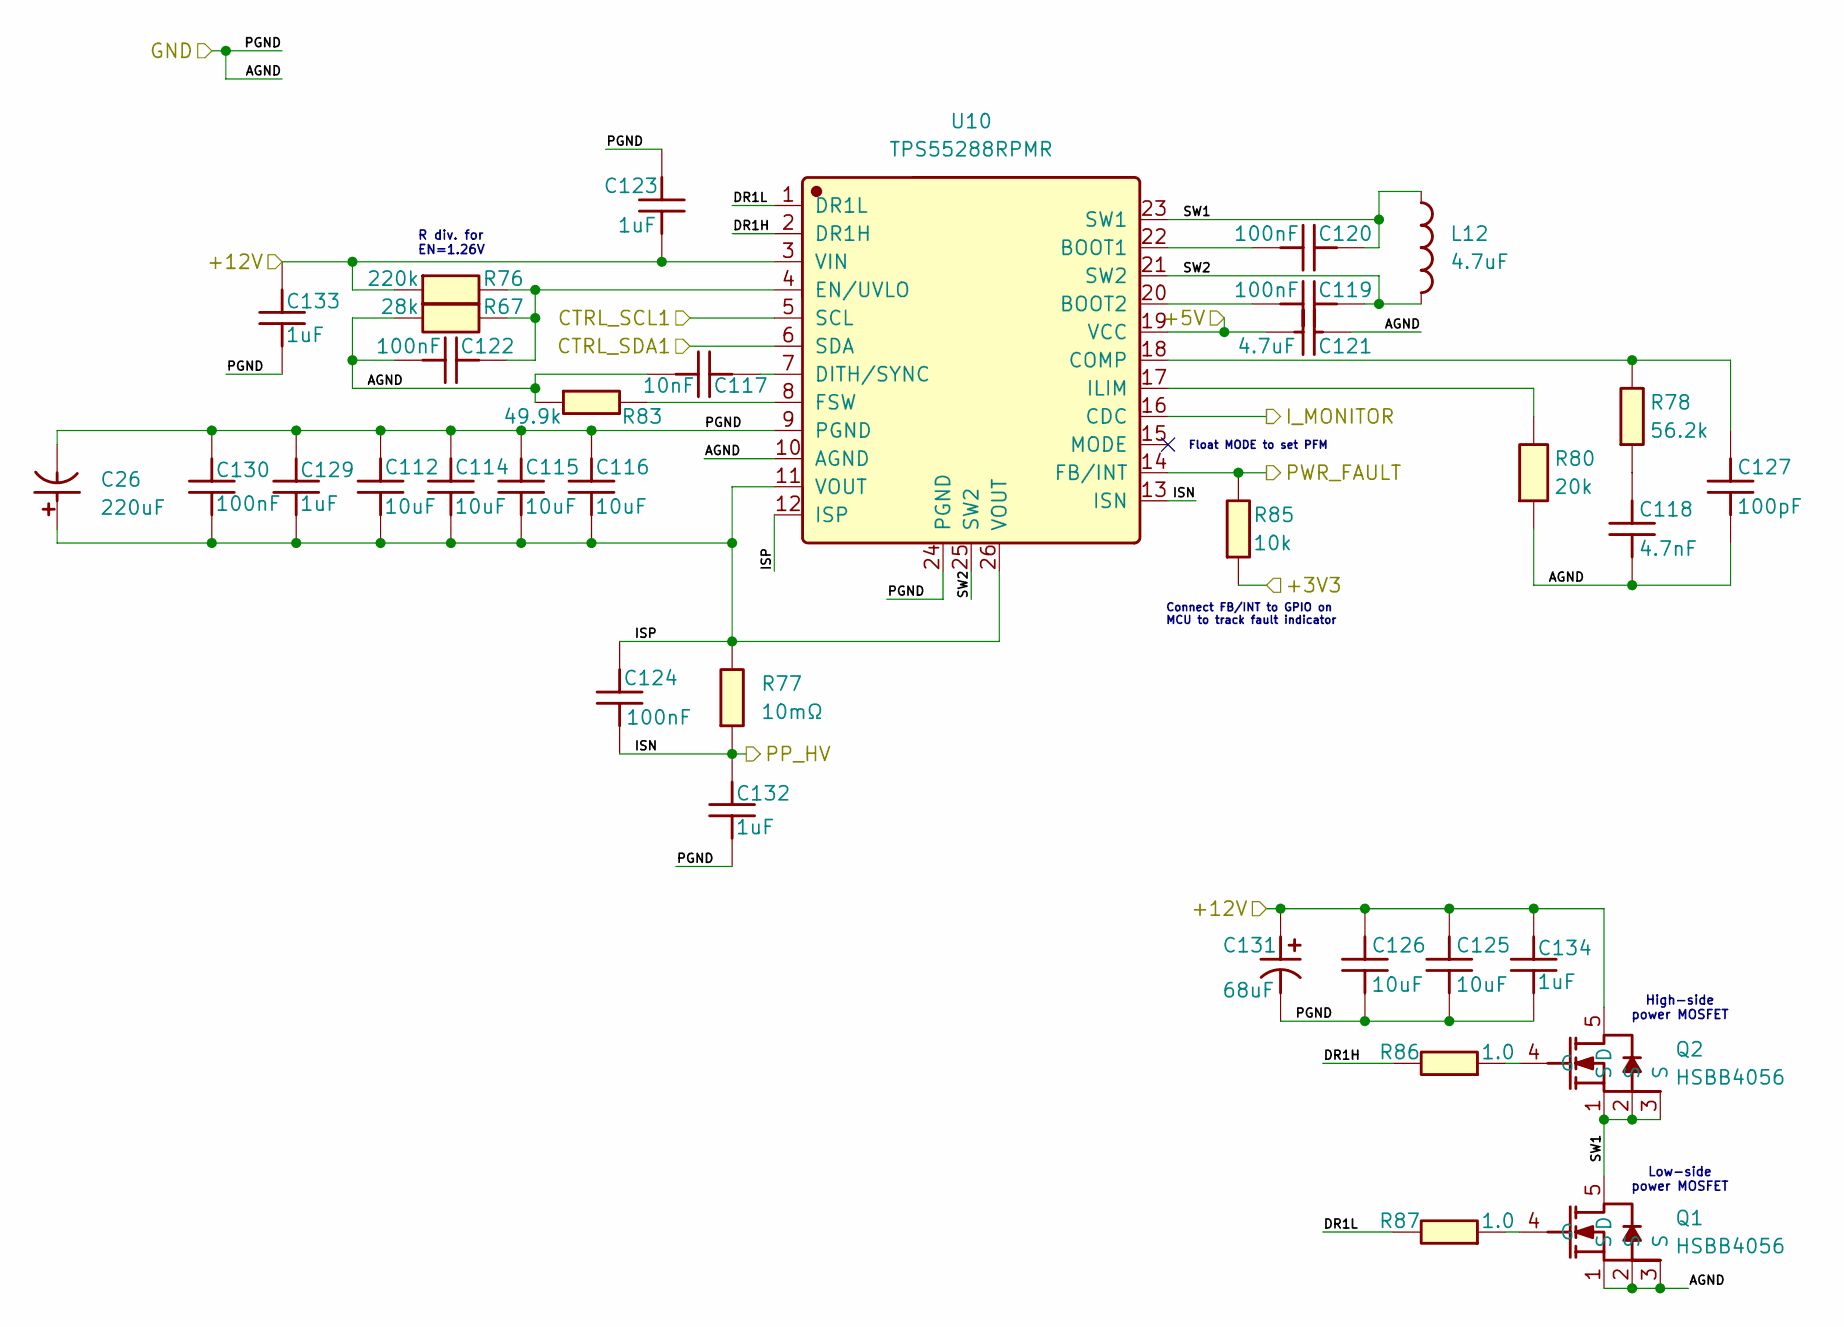
[picture p26: schematic TPS55288.kicad_sch]

Parts:
C26: 220uF; RVT1V221M0810-C72498; Manufacturer Part RVT1V221M0810; LCSC C72498
C112, C114, C115, C116: 10uF; C_0603_1608Metric; Manufacturer Part TCC0603X5R106K250CT; LCSC C7393892
C117: 10nF; C_0402_1005Metric; Manufacturer Part TCC0402X7R103M500AT; LCSC C696856
C118: 4.7nF; C_0402_1005Metric; Manufacturer Part TCC0402X7R472K500AT; LCSC C696917
C119, C120, C122, C124, C130: 100nF; C_0402_1005Metric; Manufacturer Part CL05B104KB54PNC; LCSC C307331
C121: 4.7uF; C_0805_2012Metric; Manufacturer Part CL21A475KAQNNNE; LCSC C1779
C123: 1uF; C_0603_1608Metric; Manufacturer Part CL10A105KB8NNNC; LCSC C15849
C125, C126: 10uF; C_0805_2012Metric; Manufacturer Part CL21A106KAYNNNE; LCSC C15850
C127: 100pF; C_0402_1005Metric; Manufacturer Part TCC0402COG101J101AT; LCSC C7393839
C129, C132, C133, C134: 1uF; C_0402_1005Metric; Manufacturer Part CL05A105KA5NQNC; LCSC C52923
C131: 68uF; DHG100M686G150S1AA; Manufacturer Part DHG100M686G150S1AA; LCSC C46551229
L12: 4.7uF; XR1265-4R7M; Manufacturer Part XR1265-4R7M; LCSC C5307727
Q1, Q2: HSBB4056; Manufacturer Part HSBB4056; LCSC C51025842
R67: 28k; R_0402_1005Metric; Manufacturer Part CL0402FN28KP; LCSC C52209959
R76: 220k; R_0402_1005Metric; Manufacturer Part NQ02WGF2203TCE; LCSC C965274
R77: 10mΩ; R_1206_3216Metric; Manufacturer Part STE1206M1W0R010F; LCSC C201276
R78: 56.2k; R_0402_1005Metric; Manufacturer Part CR0402FF5622G; LCSC C100481
R80: 20k; R_0402_1005Metric; Manufacturer Part CR0402J20K0Q10Z; LCSC C881394
R83: 49.9k; R_0402_1005Metric; Manufacturer Part RMS04FT4992; LCSC C208898
R85: 10k; R_0402_1005Metric; Manufacturer Part 0402WGF1002TCE; LCSC C25744
R86, R87: 1.0; R_0402_1005Metric; Manufacturer Part WR04W1R00FTL; LCSC C168208
U10: TPS55288RPMR; Manufacturer Part TPS55288RPMR; LCSC C2864583

Connections:
+3V3: R85.1
+5V: C121.2, U10.19 (VCC)
+12V: C123.1, C125.2, C126.2, C131.1, C133.2, C134.2, Q2.5 (D), R76.1, U10.3 (VIN)
AGND: C26.2, C112.1, C114.1, C115.1, C116.1, C117.1, C118.1, C121.1, C122.1, C123.2, C125.1, C126.1, C127.1, C129.2, C130.2, C131.2, C132.1, C133.1, C134.1, Q1.1 (S), Q1.2 (S), Q1.3 (S), R67.1, R80.1, R83.1, U10.9 (PGND), U10.10 (AGND), U10.24 (PGND)
CTRL_SCL1: U10.5 (SCL)
CTRL_SDA1: U10.6 (SDA)
DR1H: R86.2, U10.2 (DR1H)
DR1L: R87.2, U10.1 (DR1L)
ISN: C124.1, C132.2, R77.1, U10.13 (ISN)
ISP: C26.1, C112.2, C114.2, C115.2, C116.2, C124.2, C129.1, C130.1, R77.2, U10.11 (VOUT), U10.12 (ISP), U10.26 (VOUT)
I_MONITOR: U10.16 (CDC)
unnamed: C117.2, U10.7 (DITH/SYNC)
unnamed: C118.2, R78.1
unnamed: C119.1, U10.20 (BOOT2)
unnamed: C120.1, U10.22 (BOOT1)
unnamed: C122.2, R67.2, R76.2, U10.4 (EN/UVLO)
unnamed: C127.2, R78.2, U10.18 (COMP)
unnamed: Q1.4 (G), R87.1
unnamed: Q2.4 (G), R86.1
unnamed: R80.2, U10.17 (ILIM)
unnamed: R83.2, U10.8 (FSW)
PWR_FAULT: R85.2, U10.14 (FB/INT)
SW1: C120.2, L12.1, Q1.5 (D), Q2.1 (S), Q2.2 (S), Q2.3 (S), U10.23 (SW1)
SW2: C119.2, L12.2, U10.21 (SW2), U10.25 (SW2)

Notes on the sheet:
Float MODE to set PFM
Connect FB/INT to GPIO on MCU to track fault indicator
High-side power MOSFET
Low-side power MOSFET
R div. for EN=1.26V
