HynixCJR/LZ-1-Backplane/pcb_files/TPS65987D.kicad_sch

## KiCad design pcb_files/TPS65987D.kicad_sch (2026-08-07)

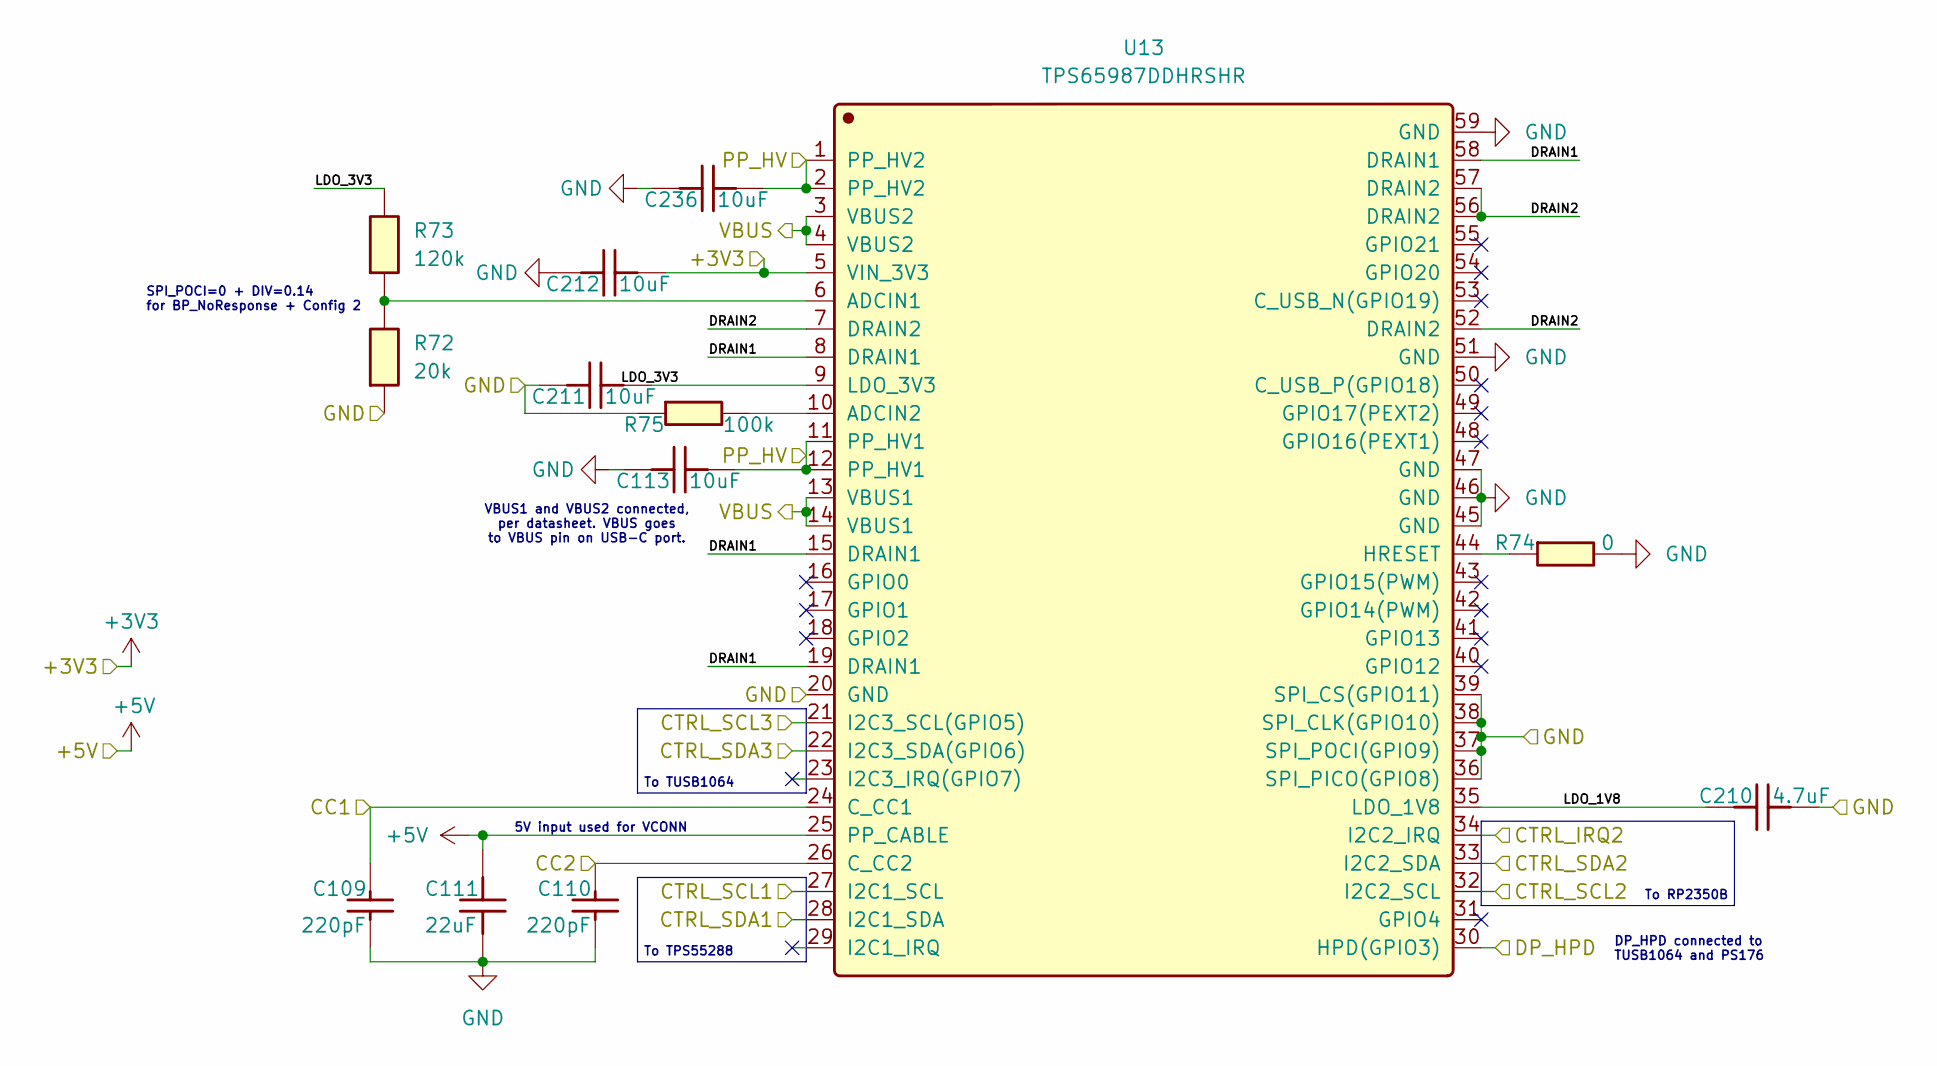
[picture p27: schematic TPS65987D.kicad_sch]

Parts:
C109, C110: 220pF; C_0402_1005Metric; Manufacturer Part 0402B221K500NT; LCSC C1530
C111: 22uF; C_0603_1608Metric; Manufacturer Part CL10A226MQ8NRNC; LCSC C59461
C113, C211, C212, C236: 10uF; C_0603_1608Metric; Manufacturer Part HGC0603R5106M350NTHJ; LCSC C22367827
C210: 4.7uF; C_0603_1608Metric; Manufacturer Part CL10A475KL8NRNC; LCSC C307467
R72: 20k; R_0402_1005Metric; Manufacturer Part 1RC0402J0203; LCSC C54531047
R73: 120k; R_0402_1005Metric; Manufacturer Part HRC0402F1203DNTO; LCSC C54920620
R74: 0; R_0402_1005Metric; Manufacturer Part 0402WGF0000TCE; LCSC C17168
R75: 100k; R_0402_1005Metric; Manufacturer Part 0402WGF1003TCE; LCSC C25741
U13: TPS65987DDHRSHR; Manufacturer Part TPS65987DDHRSHR; LCSC C2868843

Connections:
+3V3: C212.2, U13.5 (VIN_3V3)
+5V: C111.2, U13.25 (PP_CABLE)
CC1: C109.2, U13.24 (C_CC1)
CC2: C110.2, U13.26 (C_CC2)
CTRL_IRQ2: U13.34 (I2C2_IRQ)
CTRL_SCL1: U13.27 (I2C1_SCL)
CTRL_SCL2: U13.32 (I2C2_SCL)
CTRL_SCL3: U13.21 (I2C3_SCL(GPIO5))
CTRL_SDA1: U13.28 (I2C1_SDA)
CTRL_SDA2: U13.33 (I2C2_SDA)
CTRL_SDA3: U13.22 (I2C3_SDA(GPIO6))
DP_HPD: U13.30 (HPD(GPIO3))
DRAIN1: U13.8 (DRAIN1), U13.15 (DRAIN1), U13.19 (DRAIN1), U13.58 (DRAIN1)
DRAIN2: U13.7 (DRAIN2), U13.52 (DRAIN2), U13.56 (DRAIN2), U13.57 (DRAIN2)
GND: C109.1, C110.1, C111.1, C113.1, C210.2, C211.1, C212.1, C236.1, R72.1, R74.2, R75.1, U13.20 (GND), U13.36 (SPI_PICO(GPIO8)), U13.37 (SPI_POCI(GPIO9)), U13.38 (SPI_CLK(GPIO10)), U13.39 (SPI_CS(GPIO11)), U13.45 (GND), U13.46 (GND), U13.47 (GND), U13.51 (GND), U13.59 (GND)
LDO_1V8: C210.1, U13.35 (LDO_1V8)
LDO_3V3: C211.2, R73.2, U13.9 (LDO_3V3)
unnamed: R72.2, R73.1, U13.6 (ADCIN1)
unnamed: R74.1, U13.44 (HRESET)
unnamed: R75.2, U13.10 (ADCIN2)
PP_HV: C113.2, C236.2, U13.1 (PP_HV2), U13.2 (PP_HV2), U13.11 (PP_HV1), U13.12 (PP_HV1)
VBUS: U13.3 (VBUS2), U13.4 (VBUS2), U13.13 (VBUS1), U13.14 (VBUS1)

Notes on the sheet:
5V input used for VCONN
To RP2350B
SPI_POCI=0 + DIV=0.14 for BP_NoResponse + Config 2
VBUS1 and VBUS2 connected, per datasheet. VBUS goes to VBUS pin on USB-C port.
To TUSB1064
DP_HPD connected to TUSB1064 and PS176
To TPS55288
