HynixCJR/LZ-1-Backplane/pcb_files/TPS259530.kicad_sch

## KiCad design pcb_files/TPS259530.kicad_sch (2026-07-25)

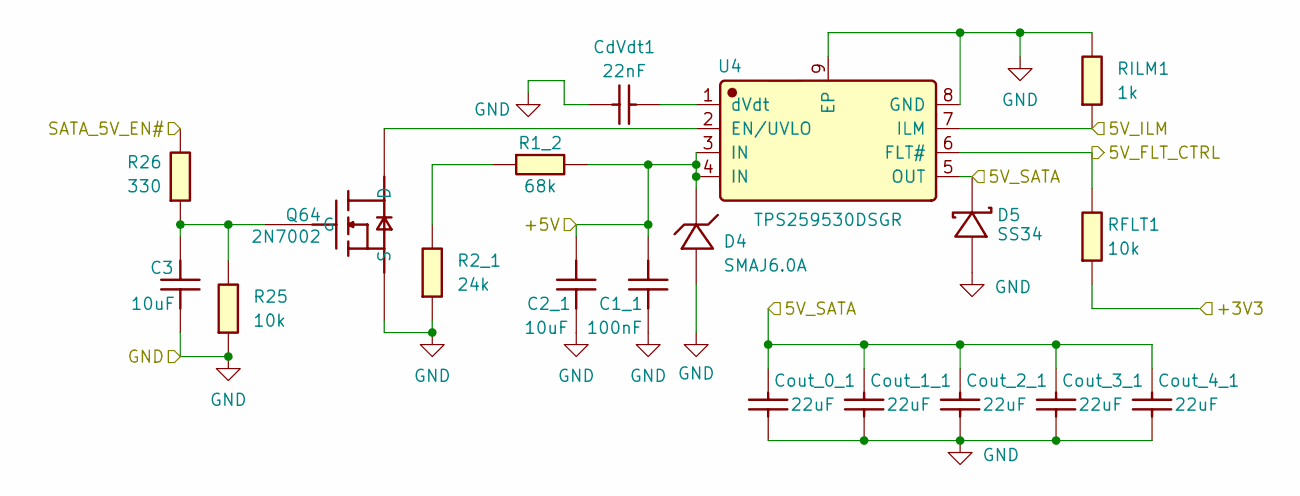
[picture p28: schematic TPS259530.kicad_sch]

Parts:
C1_1: 100nF; C_0402_1005Metric; Manufacturer Part CL05B104KB54PNC; LCSC C307331
C2_1, C3: 10uF; C_0603_1608Metric; Manufacturer Part CL10A106KP8NNNC; LCSC C19702
CdVdt1: 22nF; C_0603_1608Metric; Manufacturer Part CL10B223KB8NNNC; LCSC C21122
Cout_0_1, Cout_1_1, Cout_2_1, Cout_3_1, Cout_4_1: 22uF; C_1206_3216Metric; Manufacturer Part CL31A226KAHNNNE; LCSC C12891
D4: SMAJ6.0A; Hirose_DF40HC(3.5)-20DS-0.4V_2x10_P0.4mm; Manufacturer Part SMAJ6.0A; LCSC C353434
D5: SS34; DHVQFN-20-1EP_2.5x4.5mm_P0.5mm_EP1x3mm; Manufacturer Part SS34; LCSC C8678
Q64: 2N7002; 2N7002_C916396; Manufacturer Part 2N7002; LCSC C916396
R1_2: 68k; R_0603_1608Metric; Manufacturer Part 0603WAF6802T5E; LCSC C23231
R2_1: 24k; R_0603_1608Metric; Manufacturer Part 0603WAF2402T5E; LCSC C23352
R25: 10k; R_0402_1005Metric; Manufacturer Part 0402WGF1002TCE; LCSC C25744
R26: 330; R_0402_1005Metric; Manufacturer Part 0402WGF3300TCE; LCSC C25104
RFLT1: 10k; R_0402_1005Metric; Manufacturer Part 0402WGF1002TCE; LCSC C25744
RILM1: 1k; R_0603_1608Metric; Manufacturer Part 0603WAF1001T5E; LCSC C21190
U4: TPS259530DSGR; WSON-8-1EP_3x3mm_P0.5mm_EP1.2x2mm; Manufacturer Part TPS259530DSGR; LCSC C2155775

Connections:
5V_FLT_CTRL: RFLT1.2, U4.6 (FLT#)
5V_ILM: RILM1.1, U4.7 (ILM)
5V_SATA: Cout_0_1.2, Cout_1_1.2, Cout_2_1.2, Cout_3_1.2, Cout_4_1.2, D5.1 (K), U4.5 (OUT)
+3V3: RFLT1.1
+5V: C1_1.2, C2_1.2, D4.1 (C), R1_2.2, U4.3 (IN), U4.4 (IN)
GND: C1_1.1, C2_1.1, C3.1, CdVdt1.1, Cout_0_1.1, Cout_1_1.1, Cout_2_1.1, Cout_3_1.1, Cout_4_1.1, D4.2 (A), D5.2 (A), Q64.2 (S), R2_1.1, R25.1, RILM1.2, U4.8 (GND), U4.9 (EP)
unnamed: C3.2, Q64.1 (G), R25.2, R26.1
unnamed: CdVdt1.2, U4.1 (dVdt)
unnamed: Q64.3 (D), U4.2 (EN/UVLO)
unnamed: R1_2.1, R2_1.2
SATA_5V_EN#: R26.2
