HynixCJR/LZ-1-Backplane/pcb_files/TPS259540.kicad_sch

## KiCad design pcb_files/TPS259540.kicad_sch (2026-07-25)

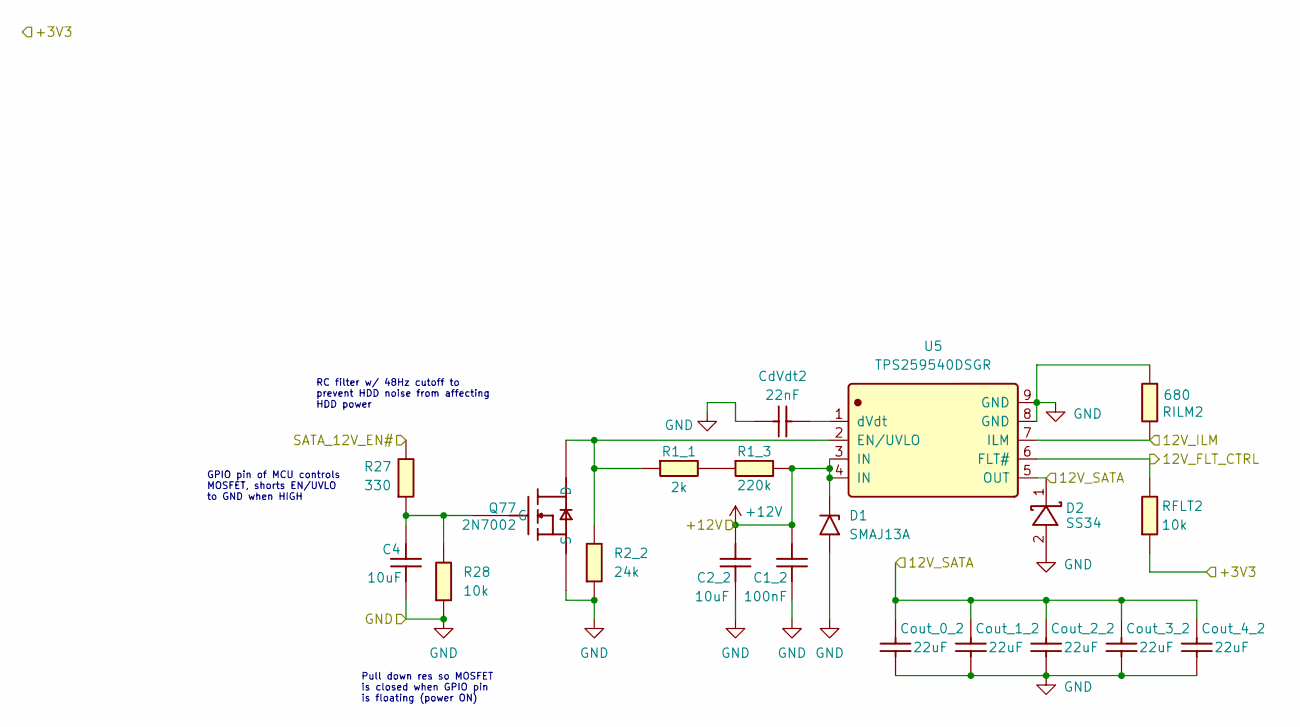
[picture p29: schematic TPS259540.kicad_sch]

Parts:
C1_2: 100nF; C_0402_1005Metric; Manufacturer Part CL05B104KB54PNC; LCSC C307331
C2_2, C4: 10uF; C_0603_1608Metric; Manufacturer Part CL10A106KP8NNNC; LCSC C19702
CdVdt2: 22nF; C_0603_1608Metric; Manufacturer Part CL10B223KB8NNNC; LCSC C21122
Cout_0_2, Cout_1_2, Cout_2_2, Cout_3_2, Cout_4_2: 22uF; C_1206_3216Metric; Manufacturer Part CL31A226KAHNNNE; LCSC C12891
D1: SMAJ13A; D_SMA
D2: SS34; DHVQFN-20-1EP_2.5x4.5mm_P0.5mm_EP1x3mm; Manufacturer Part SS34; LCSC C8678
Q77: 2N7002; 2N7002_C916396; Manufacturer Part 2N7002; LCSC C916396
R1_1: 2k; R_0603_1608Metric; Manufacturer Part 0603WAF2001T5E; LCSC C22975
R1_3: 220k; R_0603_1608Metric; Manufacturer Part 0603WAF220KT5E; LCSC C22939
R2_2: 24k; R_0603_1608Metric; Manufacturer Part 0603WAF2402T5E; LCSC C23352
R27: 330; R_0402_1005Metric; Manufacturer Part 0402WGF3300TCE; LCSC C25104
R28: 10k; R_0402_1005Metric; Manufacturer Part 0402WGF1002TCE; LCSC C25744
RFLT2: 10k; R_0402_1005Metric; Manufacturer Part 0402WGF1002TCE; LCSC C25744
RILM2: 680; R_0603_1608Metric; Manufacturer Part 0603WAF6800T5E; LCSC C23228
U5: TPS259540DSGR; WSON-8-1EP_3x3mm_P0.5mm_EP1.2x2mm; Manufacturer Part TPS259540DSGR; LCSC C2155771

Connections:
12V_FLT_CTRL: RFLT2.2, U5.6 (FLT#)
12V_ILM: RILM2.2, U5.7 (ILM)
12V_SATA: Cout_0_2.2, Cout_1_2.2, Cout_2_2.2, Cout_3_2.2, Cout_4_2.2, D2.1 (K), U5.5 (OUT)
+3V3: RFLT2.1
+12V: C1_2.2, C2_2.2, D1.1 (A1), R1_3.2, U5.3 (IN), U5.4 (IN)
GND: C1_2.1, C2_2.1, C4.1, CdVdt2.1, Cout_0_2.1, Cout_1_2.1, Cout_2_2.1, Cout_3_2.1, Cout_4_2.1, D1.2 (A2), D2.2 (A), Q77.2 (S), R2_2.1, R28.1, RILM2.1, U5.8 (GND), U5.9 (GND)
unnamed: C4.2, Q77.1 (G), R27.1, R28.2
unnamed: CdVdt2.2, U5.1 (dVdt)
unnamed: Q77.3 (D), R1_1.1, R2_2.2, U5.2 (EN/UVLO)
unnamed: R1_1.2, R1_3.1
SATA_12V_EN#: R27.2

Notes on the sheet:
RC filter w/ 48Hz cutoff to prevent HDD noise from affecting HDD power
Pull down res so MOSFET is closed when GPIO pin is floating (power ON)
GPIO pin of MCU controls MOSFET, shorts EN/UVLO to GND when HIGH
