HynixCJR/LZ-1-Backplane/pcb_files/UCS2113.kicad_sch

## KiCad design pcb_files/UCS2113.kicad_sch (2026-07-31)

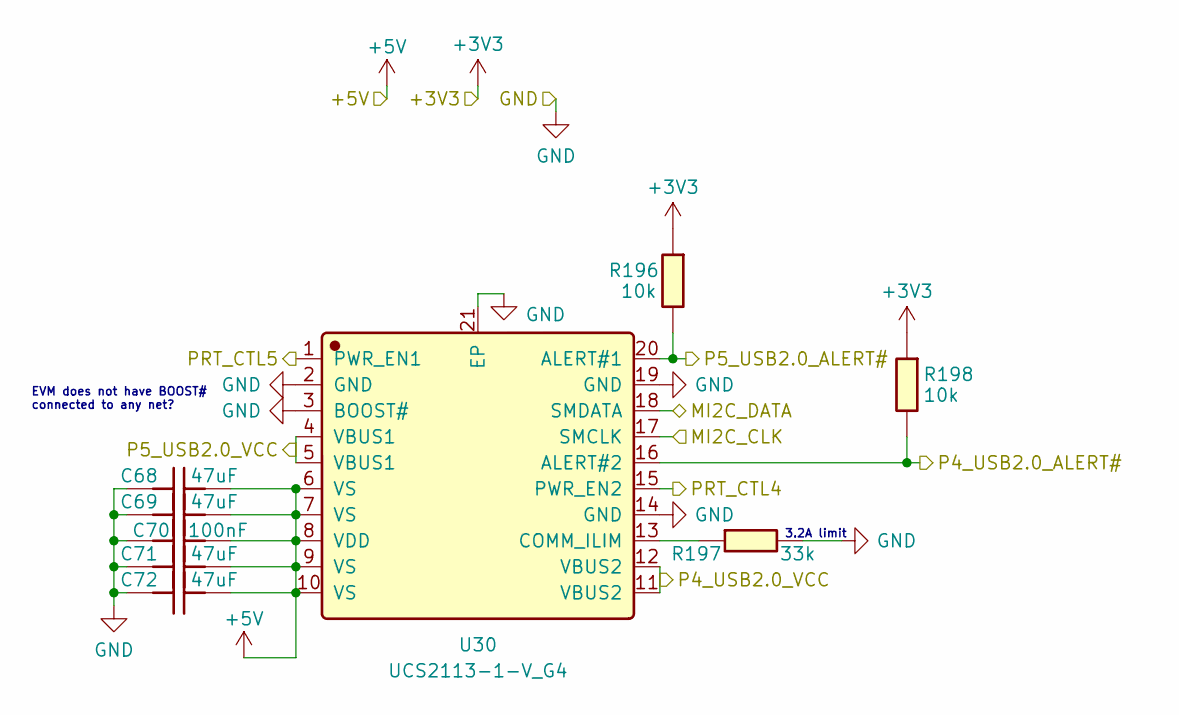
[picture p30: schematic UCS2113.kicad_sch]

Parts:
C68, C69, C71, C72: 47uF; C_1206_3216Metric; Manufacturer Part C1206B476M007T; LCSC C2991900
C70: 100nF; C_0402_1005Metric; Manufacturer Part CL05B104KB54PNC; LCSC C307331
R196, R198: 10k; R_0402_1005Metric; Manufacturer Part 0402WGF1002TCE; LCSC C25744
R197: 33k; R_0402_1005Metric; Manufacturer Part WR04X3302FTL; LCSC C163824
U30: UCS2113-1-V_G4; Manufacturer Part UCS2113-1-V/G4; LCSC C638222

Connections:
+3V3: R196.1, R198.1
+5V: C68.1, C69.1, C70.2, C71.1, C72.1, U30.6 (VS), U30.7 (VS), U30.8 (VDD), U30.9 (VS), U30.10 (VS)
GND: C68.2, C69.2, C70.1, C71.2, C72.2, R197.2, U30.2 (GND), U30.3 (BOOST#), U30.14 (GND), U30.19 (GND), U30.21 (EP)
MI2C_CLK: U30.17 (SMCLK)
MI2C_DATA: U30.18 (SMDATA)
unnamed: R197.1, U30.13 (COMM_ILIM)
P4_USB2.0_ALERT#: R198.2, U30.16 (ALERT#2)
P4_USB2.0_VCC: U30.11 (VBUS2), U30.12 (VBUS2)
P5_USB2.0_ALERT#: R196.2, U30.20 (ALERT#1)
P5_USB2.0_VCC: U30.4 (VBUS1), U30.5 (VBUS1)
PRT_CTL4: U30.15 (PWR_EN2)
PRT_CTL5: U30.1 (PWR_EN1)

Notes on the sheet:
EVM does not have BOOST# connected to any net?
3.2A limit
