HynixCJR/LZ-1-Backplane/pcb_files/USB2244i.kicad_sch

## KiCad design pcb_files/USB2244i.kicad_sch (2026-08-01)

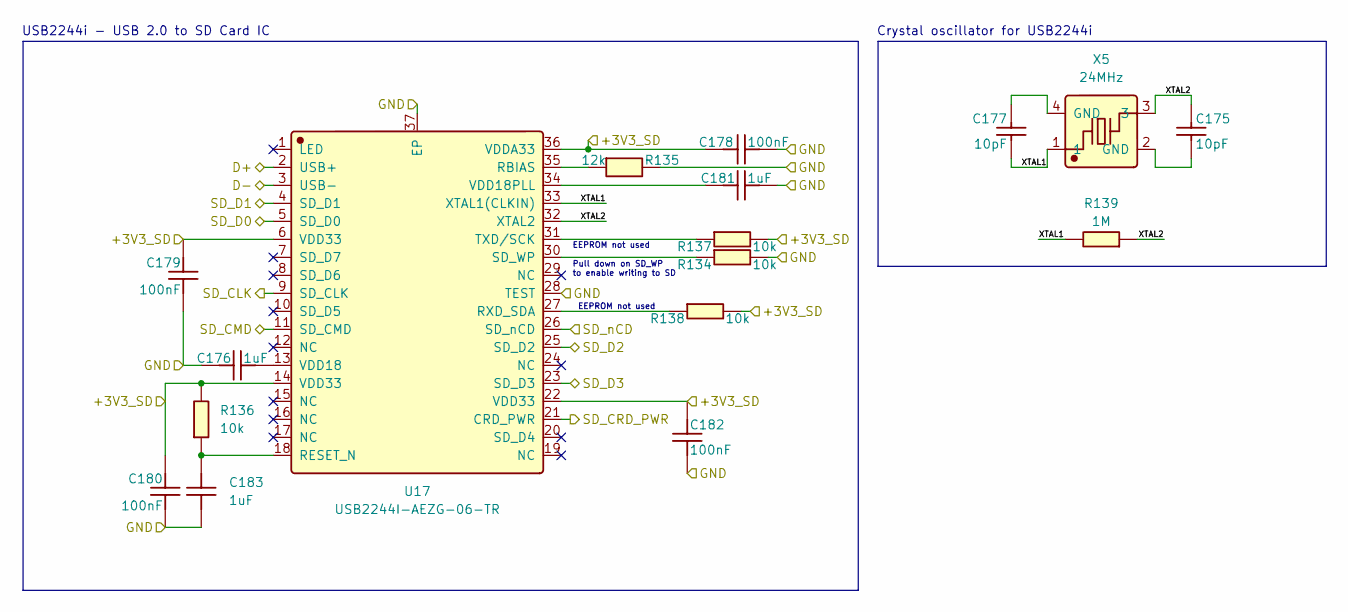
[picture p31: schematic USB2244i.kicad_sch]

Parts:
C175, C177: 10pF; C_0603_1608Metric; Manufacturer Part CL10C100JB8NNNC; LCSC C1634
C176, C181, C183: 1uF; C_0402_1005Metric; Manufacturer Part CL05A105KA5NQNC; LCSC C52923
C178, C179, C180, C182: 100nF; C_0402_1005Metric; Manufacturer Part CL05B104KB54PNC; LCSC C307331
R134, R136, R137, R138: 10k; R_0402_1005Metric; Manufacturer Part 0402WGF1002TCE; LCSC C25744
R135: 12k; R_0402_1005Metric; Manufacturer Part CR0402F12K0Q10Z; LCSC C881068
R139: 1M; R_0402_1005Metric; Manufacturer Part 0402WGF1004TCE; LCSC C26083
U17: USB2244I-AEZG-06-TR; Manufacturer Part USB2244I-AEZG-06-TR; LCSC C2674043
X5: 24MHz; XTM32024000DT00351001; Manufacturer Part XTM32024000DT00351001; LCSC C41383243

Connections:
+3V3_SD: C178.2, C179.1, C180.1, C182.2, R136.2, R137.2, R138.2, U17.6 (VDD33), U17.14 (VDD33), U17.22 (VDD33), U17.36 (VDDA33)
D+: U17.2 (USB+)
D-: U17.3 (USB-)
GND: C176.2, C178.1, C179.2, C180.2, C181.1, C182.1, C183.1, R134.2, R135.2, U17.28 (TEST), U17.37 (EP)
unnamed: C175.1, X5.2 (GND)
unnamed: C176.1, U17.13 (VDD18)
unnamed: C177.1, X5.4 (GND)
unnamed: C181.2, U17.34 (VDD18PLL)
unnamed: C183.2, R136.1, U17.18 (RESET_N)
unnamed: R134.1, U17.30 (SD_WP)
unnamed: R135.1, U17.35 (RBIAS)
unnamed: R137.1, U17.31 (TXD/SCK)
unnamed: R138.1, U17.27 (RXD_SDA)
SD_CLK: U17.9 (SD_CLK)
SD_CMD: U17.11 (SD_CMD)
SD_CRD_PWR: U17.21 (CRD_PWR)
SD_D0: U17.5 (SD_D0)
SD_D1: U17.4 (SD_D1)
SD_D2: U17.25 (SD_D2)
SD_D3: U17.23 (SD_D3)
SD_nCD: U17.26 (SD_nCD)
XTAL1: C177.2, R139.2, U17.33 (XTAL1(CLKIN)), X5.1
XTAL2: C175.2, R139.1, U17.32 (XTAL2), X5.3

Notes on the sheet:
EEPROM not used
USB2244i - USB 2.0 to SD Card IC
Crystal oscillator for USB2244i
Pull down on SD_WP to enable writing to SD
