HynixCJR/LZ-1-Backplane/pcb_files/USB7205C.kicad_sch

## KiCad design pcb_files/USB7205C.kicad_sch (2026-07-31)

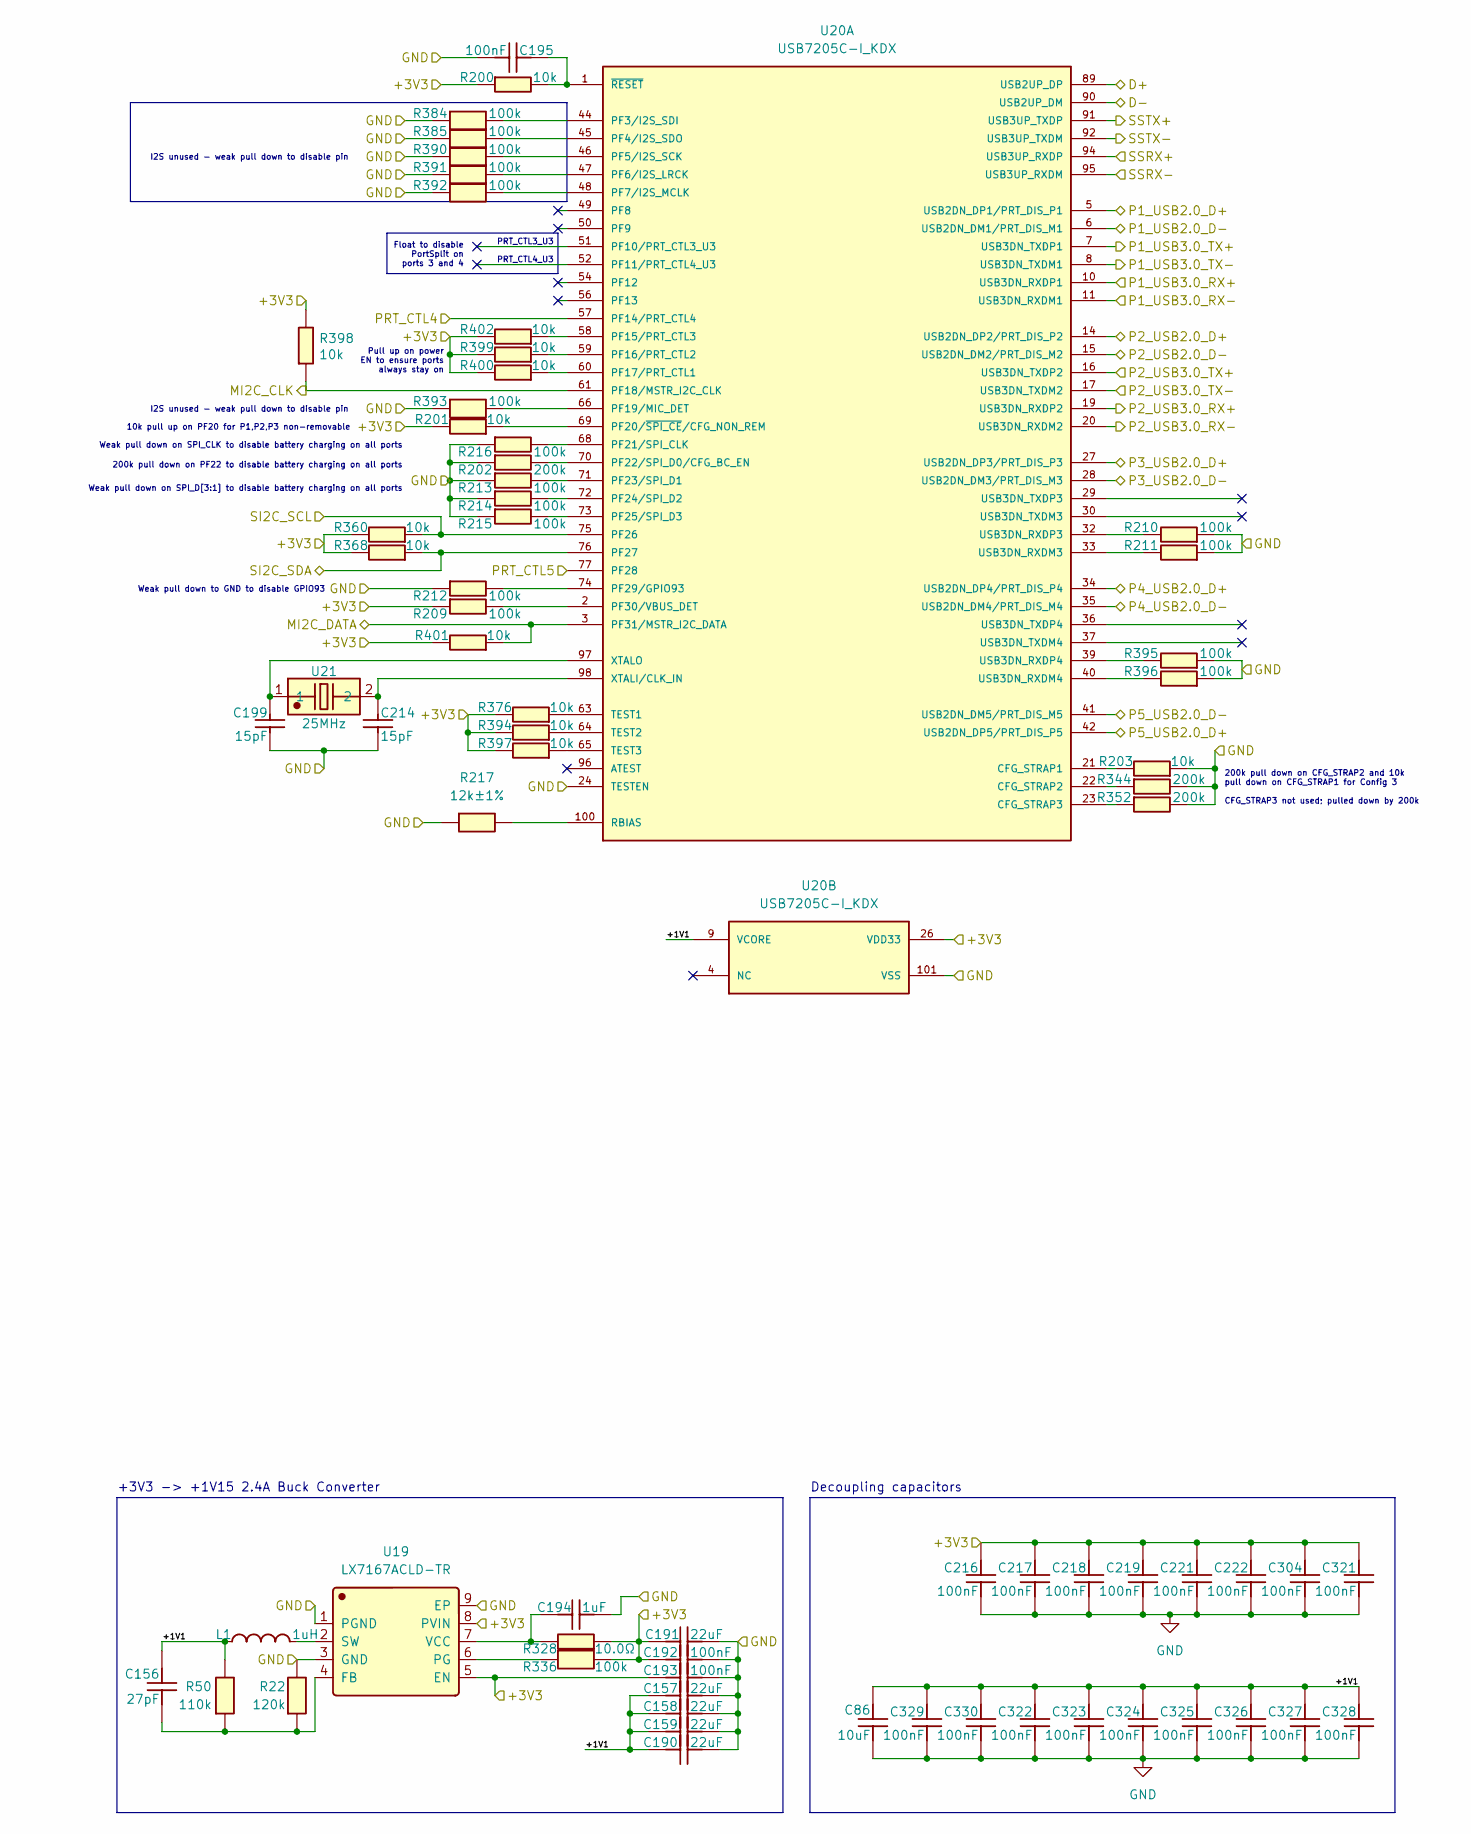
[picture p32: schematic USB7205C.kicad_sch]

Parts:
C86: 10uF; C_0805_2012Metric; Manufacturer Part CL21A106KAYNNNE; LCSC C15850
C156: 27pF; C_0402_1005Metric; Manufacturer Part TCC0402C0G270J500AT; LCSC C466227
C157, C158, C159, C190, C191: 22uF; C_0603_1608Metric; Manufacturer Part 0603DS226M4R0NT; LCSC C5445363
C192, C193, C195, C216, C217, C218, C219, C221, C222, C304, C321, C322, C323, C324, C325, C326, C327, C328, C329, C330: 100nF; C_0402_1005Metric; Manufacturer Part CL05B104KB54PNC; LCSC C307331
C194: 1uF; C_0402_1005Metric; Manufacturer Part CL05A105KA5NQNC; LCSC C52923
C199, C214: 15pF; C_0402_1005Metric; Manufacturer Part 0402CG150J500NT; LCSC C1548
L1: 1uH; PIM201608S1R0MBCA; Manufacturer Part PIM201608S1R0MBCA; LCSC C53514733
R22: 120k; R_0402_1005Metric; Manufacturer Part HRC0402F1203DNTO; LCSC C54920620
R50: 110k; R_0402_1005Metric; Manufacturer Part HRC0402F1103DNTO; LCSC C54920617
R200, R201, R203, R360, R368, R376, R394, R397, R398, R399, R400, R401, R402: 10k; R_0402_1005Metric; Manufacturer Part 0402WGF1002TCE; LCSC C25744
R202, R344, R352: 200k; R_0402_1005Metric; Manufacturer Part RC-02K204JT; LCSC C140186
R209, R210, R211, R212, R213, R214, R215, R216, R395, R396: 100k; R_0402_1005Metric; Manufacturer Part 0402WGF1003TCE; LCSC C25741
R217: 12k±1%; R_0402_1005Metric; Manufacturer Part CR0402F12K0Q10Z; LCSC C881068
R328: 10.0Ω; R_0402_1005Metric; Manufacturer Part 0402WGF100JTCE; LCSC C25077
R336, R384, R385, R390, R391, R392, R393: 100k; R_0402_1005Metric; Manufacturer Part HP02WAF1003TCE; LCSC C2759534
U19: LX7167ACLD-TR; Manufacturer Part LX7167ACLD-TR; LCSC C5229463
U20: USB7205C-I_KDX; USB7206C-I_KDX; PARTREV 00005227C
U21: 25MHz; 25M_10PF_50PPM; Manufacturer Part 25M 10PF 50PPM; LCSC C4944018

Connections:
+1V1: C86.2, C156.1, C157.2, C158.2, C159.2, C190.2, C322.1, C323.1, C324.1, C325.1, C326.1, C327.1, C328.1, C329.1, C330.1, L1.1, R50.2, U20.9 (VCORE), U20.18 (VCORE), U20.25 (VCORE), U20.31 (VCORE), U20.38 (VCORE), U20.55 (VCORE), U20.78 (VCORE), U20.85 (VCORE), U20.93 (VCORE)
+3V3: C191.2, C192.1, C193.1, C216.1, C217.1, C218.1, C219.1, C221.1, C222.1, C304.1, C321.1, R200.1, R201.2, R209.1, R328.1, R336.2, R360.2, R368.2, R376.2, R394.2, R397.2, R398.2, R399.2, R400.2, R401.2, R402.2, U19.5 (EN), U19.8 (PVIN), U20.26 (VDD33), U20.43 (VDD33), U20.53 (VDD33), U20.62 (VDD33), U20.67 (VDD33), U20.79 (VDD33), U20.81 (VDD33), U20.82 (VDD33), U20.88 (VDD33), U20.99 (VDD33)
D+: U20.89 (USB2UP_DP)
D-: U20.90 (USB2UP_DM)
GND: C86.1, C157.1, C158.1, C159.1, C190.1, C191.1, C192.2, C193.2, C194.2, C195.2, C199.1, C214.1, C216.2, C217.2, C218.2, C219.2, C221.2, C222.2, C304.2, C321.2, C322.2, C323.2, C324.2, C325.2, C326.2, C327.2, C328.2, C329.2, C330.2, R22.2, R202.1, R203.1, R210.1, R211.1, R212.1, R213.1, R214.1, R215.1, R216.1, R217.1, R344.2, R352.2, R384.1, R385.1, R390.1, R391.1, R392.1, R393.1, R395.1, R396.1, U19.1 (PGND), U19.3 (GND), U19.9 (EP), U20.24 (TESTEN), U20.101 (VSS)
MI2C_CLK: R398.1, U20.61 (PF18/MSTR_I2C_CLK)
MI2C_DATA: R401.1, U20.3 (PF31/MSTR_I2C_DATA)
unnamed: C156.2, R22.1, R50.1, U19.4 (FB)
unnamed: C194.1, R328.2, U19.7 (VCC)
unnamed: C195.1, R200.2, U20.1 (~RESET)
unnamed: C199.2, U20.97 (XTALO), U21.1
unnamed: C214.2, U20.98 (XTALI/CLK_IN), U21.2
unnamed: L1.2, U19.2 (SW)
unnamed: R201.1, U20.69 (PF20/~SPI_CE/CFG_NON_REM)
unnamed: R202.2, U20.70 (PF22/SPI_D0/CFG_BC_EN)
unnamed: R203.2, U20.21 (CFG_STRAP1)
unnamed: R209.2, U20.2 (PF30/VBUS_DET)
unnamed: R210.2, U20.32 (USB3DN_RXDP3)
unnamed: R211.2, U20.33 (USB3DN_RXDM3)
unnamed: R212.2, U20.74 (PF29/GPIO93)
unnamed: R213.2, U20.71 (PF23/SPI_D1)
unnamed: R214.2, U20.72 (PF24/SPI_D2)
unnamed: R215.2, U20.73 (PF25/SPI_D3)
unnamed: R216.2, U20.68 (PF21/SPI_CLK)
unnamed: R217.2, U20.100 (RBIAS)
unnamed: R336.1, U19.6 (PG)
unnamed: R344.1, U20.22 (CFG_STRAP2)
unnamed: R352.1, U20.23 (CFG_STRAP3)
unnamed: R376.1, U20.63 (TEST1)
unnamed: R384.2, U20.44 (PF3/I2S_SDI)
unnamed: R385.2, U20.45 (PF4/I2S_SDO)
unnamed: R390.2, U20.46 (PF5/I2S_SCK)
unnamed: R391.2, U20.47 (PF6/I2S_LRCK)
unnamed: R392.2, U20.48 (PF7/I2S_MCLK)
unnamed: R393.2, U20.66 (PF19/MIC_DET)
unnamed: R394.1, U20.64 (TEST2)
unnamed: R395.2, U20.39 (USB3DN_RXDP4)
unnamed: R396.2, U20.40 (USB3DN_RXDM4)
unnamed: R397.1, U20.65 (TEST3)
unnamed: R399.1, U20.59 (PF16/PRT_CTL2)
unnamed: R400.1, U20.60 (PF17/PRT_CTL1)
unnamed: R402.1, U20.58 (PF15/PRT_CTL3)
unnamed: U20.4 (NC), U20.12 (NC), U20.13 (NC), U20.80 (NC), U20.83 (NC), U20.84 (NC), U20.86 (NC), U20.87 (NC)
P1_USB2.0_D+: U20.5 (USB2DN_DP1/PRT_DIS_P1)
P1_USB2.0_D-: U20.6 (USB2DN_DM1/PRT_DIS_M1)
P1_USB3.0_RX+: U20.10 (USB3DN_RXDP1)
P1_USB3.0_RX-: U20.11 (USB3DN_RXDM1)
P1_USB3.0_TX+: U20.7 (USB3DN_TXDP1)
P1_USB3.0_TX-: U20.8 (USB3DN_TXDM1)
P2_USB2.0_D+: U20.14 (USB2DN_DP2/PRT_DIS_P2)
P2_USB2.0_D-: U20.15 (USB2DN_DM2/PRT_DIS_M2)
P2_USB3.0_RX+: U20.19 (USB3DN_RXDP2)
P2_USB3.0_RX-: U20.20 (USB3DN_RXDM2)
P2_USB3.0_TX+: U20.16 (USB3DN_TXDP2)
P2_USB3.0_TX-: U20.17 (USB3DN_TXDM2)
P3_USB2.0_D+: U20.27 (USB2DN_DP3/PRT_DIS_P3)
P3_USB2.0_D-: U20.28 (USB2DN_DM3/PRT_DIS_M3)
P4_USB2.0_D+: U20.34 (USB2DN_DP4/PRT_DIS_P4)
P4_USB2.0_D-: U20.35 (USB2DN_DM4/PRT_DIS_M4)
P5_USB2.0_D+: U20.42 (USB2DN_DP5/PRT_DIS_P5)
P5_USB2.0_D-: U20.41 (USB2DN_DM5/PRT_DIS_M5)
PRT_CTL4: U20.57 (PF14/PRT_CTL4)
PRT_CTL5: U20.77 (PF28)
SI2C_SCL: R360.1, U20.75 (PF26)
SI2C_SDA: R368.1, U20.76 (PF27)
SSRX+: U20.94 (USB3UP_RXDP)
SSRX-: U20.95 (USB3UP_RXDM)
SSTX+: U20.91 (USB3UP_TXDP)
SSTX-: U20.92 (USB3UP_TXDM)

Notes on the sheet:
Float to disable PortSplit on ports 3 and 4
Pull up on power EN to ensure ports always stay on
200k pull down on CFG_STRAP2 and 10k pull down on CFG_STRAP1 for Config 3 CFG_STRAP3 not used; pulled down by 200k
Weak pull down on SPI_CLK to disable battery charging on all ports
Weak pull down on SPI_D[3:1] to disable battery charging on all ports
PRT_CTL3_U3
PRT_CTL4_U3
I2S unused - weak pull down to disable pin
Decoupling capacitors
200k pull down on PF22 to disable battery charging on all ports
+3V3 -> +1V15 2.4A Buck Converter
Weak pull down to GND to disable GPIO93
10k pull up on PF20 for P1,P2,P3 non-removable
