HynixCJR/LZ-1-Backplane/pcb_files/tusb1064.kicad_sch

## KiCad design pcb_files/tusb1064.kicad_sch (2026-07-24)

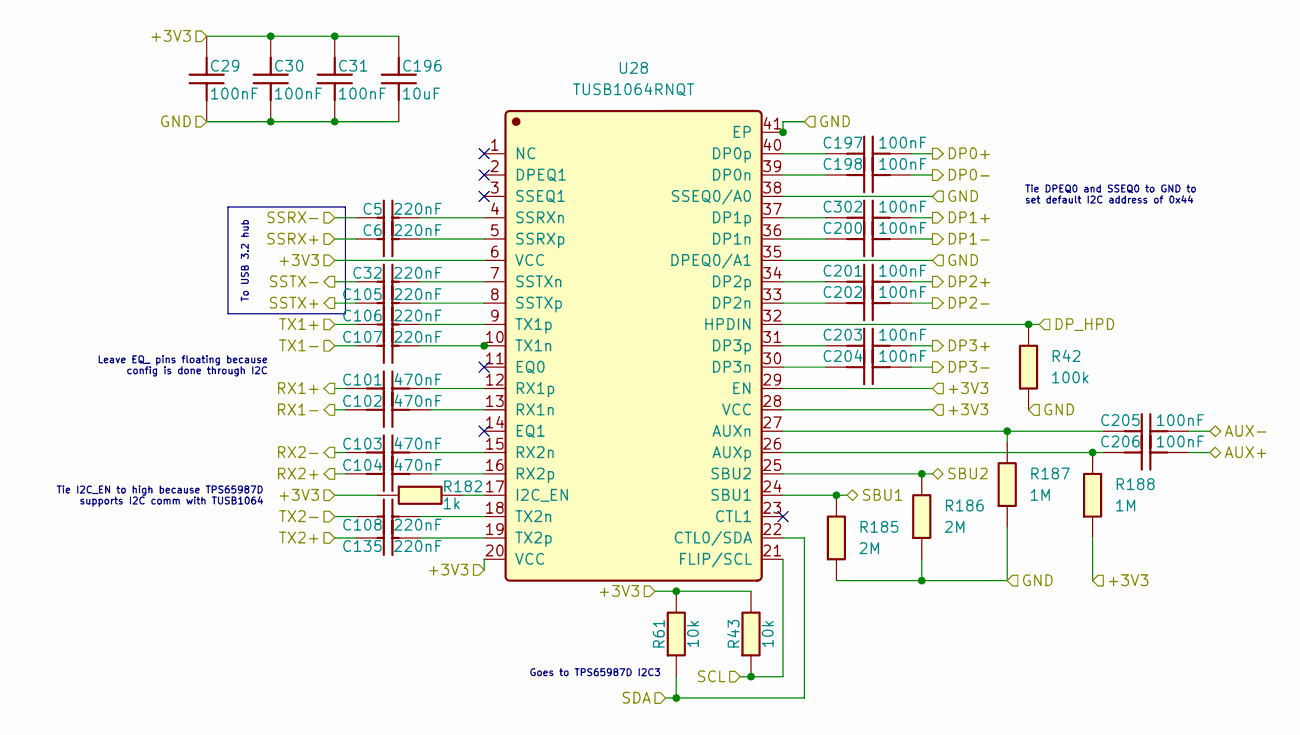
[picture p33: schematic tusb1064.kicad_sch]

Parts:
C5, C6, C32, C105, C106, C107, C108, C135: 220nF; C_0402_1005Metric; Manufacturer Part CL05B224KO5NNNC; LCSC C16772
C29, C30, C31, C197, C198, C200, C201, C202, C203, C204, C205, C206, C302: 100nF; C_0402_1005Metric; Manufacturer Part CL05B104KB54PNC; LCSC C307331
C101, C102, C103, C104: 470nF; C_0402_1005Metric; Manufacturer Part TCC0402X5R474M160AT; LCSC C7393859
C196: 10uF; C_0805_2012Metric; Manufacturer Part CL21A106KAYNNNE; LCSC C15850
R42: 100k; R_0402_1005Metric; Manufacturer Part 0402WGF1003TCE; LCSC C25741
R43, R61: 10k; R_0402_1005Metric; Manufacturer Part 0402WGF1002TCE; LCSC C25744
R182: 1k; R_0402_1005Metric; Manufacturer Part 0402WGF1001TCE; LCSC C11702
R185, R186: 2M; R_0603_1608Metric; Manufacturer Part 0603WAF2004T5E; LCSC C22976
R187, R188: 1M; R_0402_1005Metric; Manufacturer Part 0402WGF1004TCE; LCSC C26083
U28: TUSB1064RNQT; Manufacturer Part TUSB1064RNQT; LCSC C2652412

Connections:
+3V3: C29.2, C30.2, C31.2, C196.2, R43.2, R61.2, R182.1, R188.1, U28.6 (VCC), U28.20 (VCC), U28.28 (VCC), U28.29 (EN)
AUX+: C206.2
AUX-: C205.2
DP0+: C197.2
DP0-: C198.2
DP1+: C302.2
DP1-: C200.2
DP2+: C201.2
DP2-: C202.2
DP3+: C203.2
DP3-: C204.2
DP_HPD: R42.2, U28.32 (HPDIN)
GND: C29.1, C30.1, C31.1, C196.1, R42.1, R185.1, R186.1, R187.1, U28.35 (DPEQ0/A1), U28.38 (SSEQ0/A0), U28.41 (EP)
unnamed: C5.2, U28.4 (SSRXn)
unnamed: C6.2, U28.5 (SSRXp)
unnamed: C32.2, U28.7 (SSTXn)
unnamed: C101.2, U28.12 (RX1p)
unnamed: C102.2, U28.13 (RX1n)
unnamed: C103.2, U28.15 (RX2n)
unnamed: C104.2, U28.16 (RX2p)
unnamed: C105.2, U28.8 (SSTXp)
unnamed: C106.2, U28.9 (TX1p)
unnamed: C107.2, U28.10 (TX1n)
unnamed: C108.2, U28.18 (TX2n)
unnamed: C135.2, U28.19 (TX2p)
unnamed: C197.1, U28.40 (DP0p)
unnamed: C198.1, U28.39 (DP0n)
unnamed: C200.1, U28.36 (DP1n)
unnamed: C201.1, U28.34 (DP2p)
unnamed: C202.1, U28.33 (DP2n)
unnamed: C203.1, U28.31 (DP3p)
unnamed: C204.1, U28.30 (DP3n)
unnamed: C205.1, R187.2, U28.27 (AUXn)
unnamed: C206.1, R188.2, U28.26 (AUXp)
unnamed: C302.1, U28.37 (DP1p)
unnamed: R182.2, U28.17 (I2C_EN)
RX1+: C101.1
RX1-: C102.1
RX2+: C104.1
RX2-: C103.1
SBU1: R185.2, U28.24 (SBU1)
SBU2: R186.2, U28.25 (SBU2)
SCL: R43.1, U28.21 (FLIP/SCL)
SDA: R61.1, U28.22 (CTL0/SDA)
SSRX+: C6.1
SSRX-: C5.1
SSTX+: C105.1
SSTX-: C32.1
TX1+: C106.1
TX1-: C107.1
TX2+: C135.1
TX2-: C108.1

Notes on the sheet:
Tie DPEQ0 and SSEQ0 to GND to set default I2C address of 0x44
Leave EQ_ pins floating because config is done through I2C
Goes to TPS65987D I2C3
To USB 3.2 hub
Tie I2C_EN to high because TPS65987D supports I2C comm with TUSB1064
