HynixCJR/LZ-1-Backplane/pcb_files/upstream_usb-c.kicad_sch

## KiCad design pcb_files/upstream_usb-c.kicad_sch (2026-08-07)

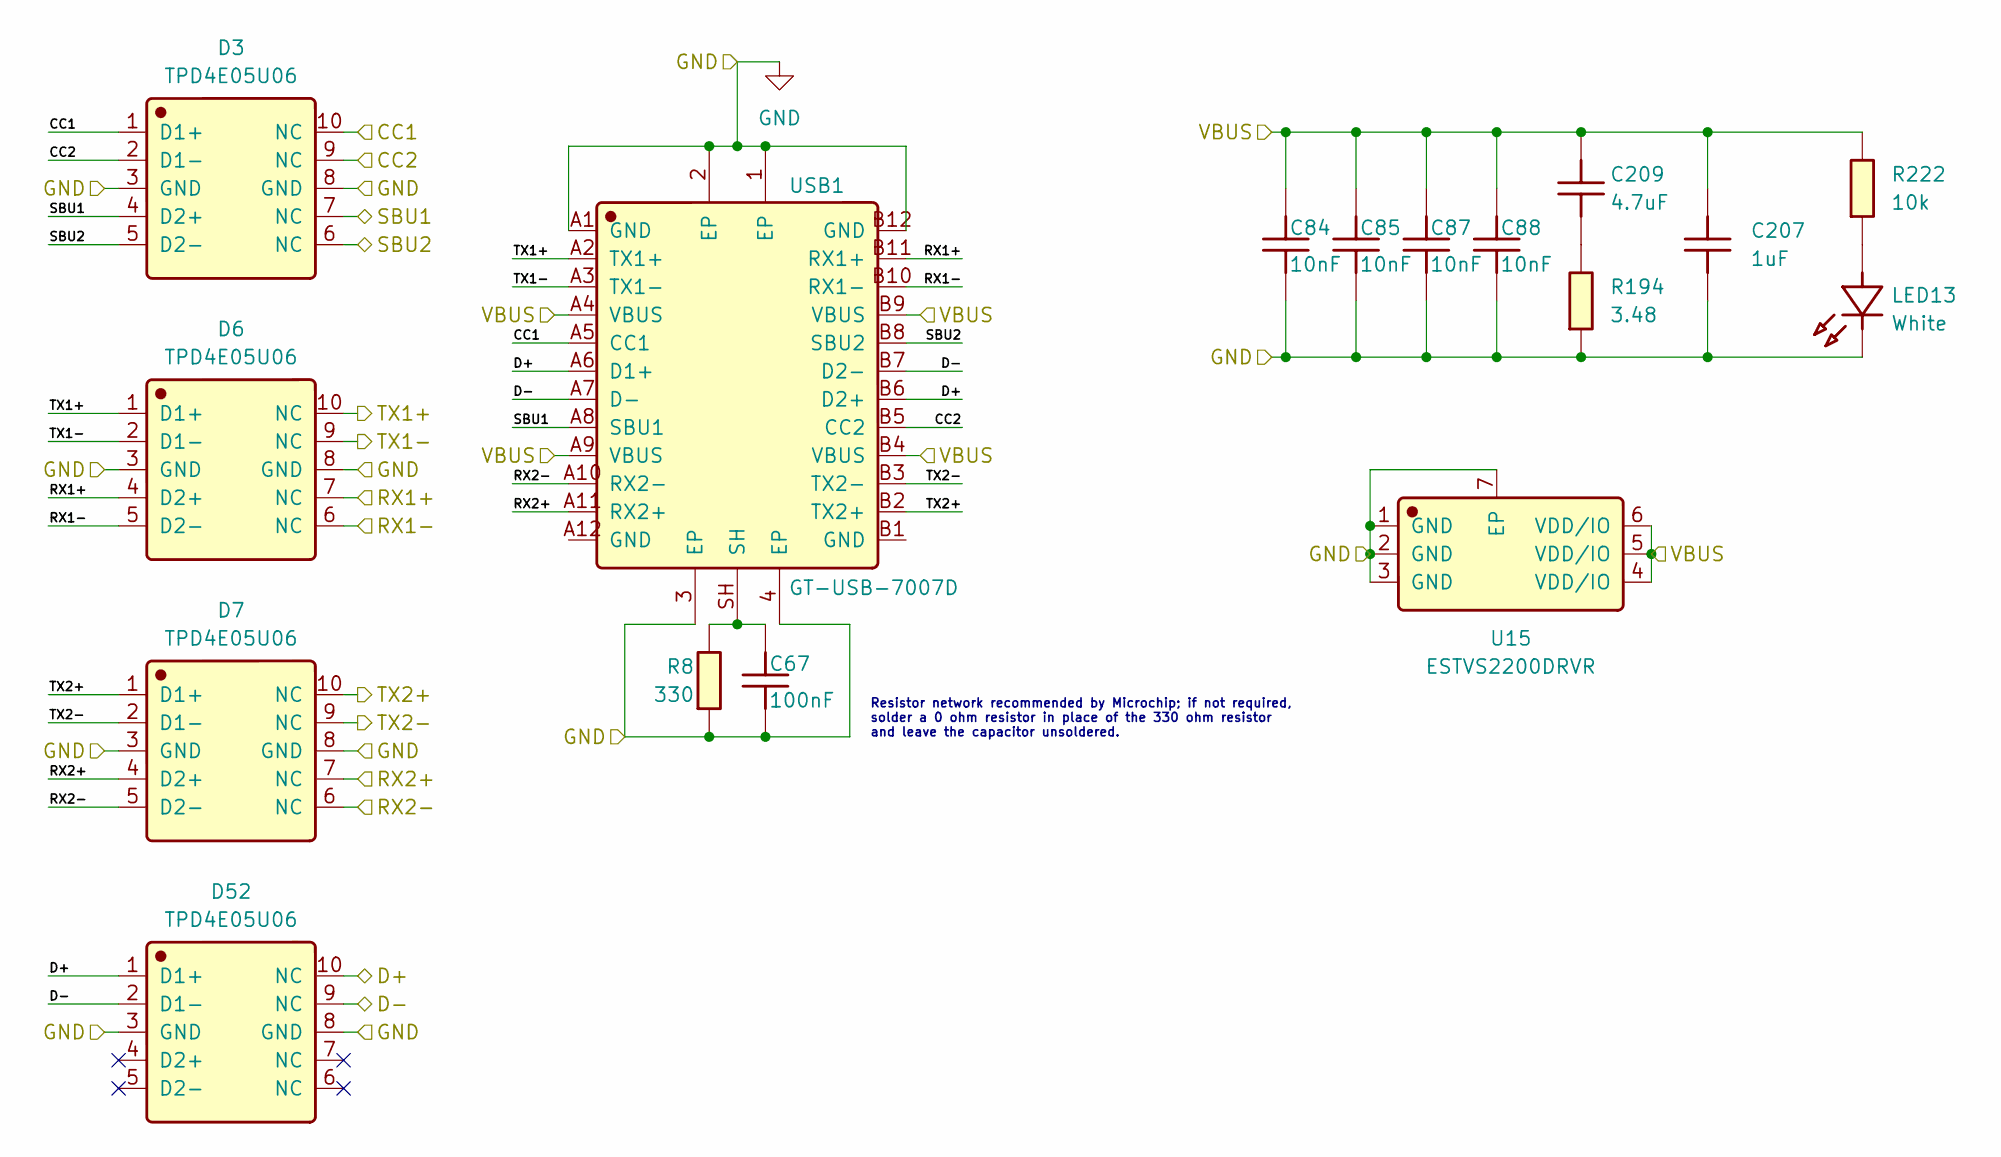
[picture p34: schematic upstream_usb-c.kicad_sch]

Parts:
C67: 100nF; C_0402_1005Metric; Manufacturer Part CL05B104KB54PNC; LCSC C307331
C84, C85, C87, C88: 10nF; C_0402_1005Metric; Manufacturer Part TCC0402X7R103M500AT; LCSC C696856
C207: 1uF; C_0603_1608Metric; Manufacturer Part CL10A105KB8NNNC; LCSC C15849
C209: 4.7uF; C_0603_1608Metric; Manufacturer Part CL10A475KL8NRNC; LCSC C307467
D3, D6, D7, D52: TPD4E05U06; TPD4E05U06DQAR_C138714; Manufacturer Part TPD4E05U06DQAR; LCSC C138714
LED13: White; GL0603UW01; Manufacturer Part GL0603UW01; LCSC C51933297
R8: 330; R_0402_1005Metric; Manufacturer Part 0402WGF3300TCE; LCSC C25104
R194: 3.48; R_0603_1608Metric; Manufacturer Part RS-03L3R48FT; LCSC C322150
R222: 10k; R_0402_1005Metric; Manufacturer Part 0402WGF1002TCE; LCSC C25744
U15: ESTVS2200DRVR; Manufacturer Part ESTVS2200DRVR; LCSC C42400188
USB1: GT-USB-7007D; USB_C_Receptacle_G-Switch_GT-USB-7025; Manufacturer Part GT-USB-7007D; LCSC C3001287

Connections:
CC1: D3.1 (D1+), D3.10 (NC), USB1.A5 (CC1)
CC2: D3.2 (D1-), D3.9 (NC), USB1.B5 (CC2)
D+: D52.1 (D1+), D52.10 (NC), USB1.A6 (D1+), USB1.B6 (D2+)
D-: D52.2 (D1-), D52.9 (NC), USB1.A7 (D-), USB1.B7 (D2-)
GND: C67.1, C84.1, C85.1, C87.1, C88.1, C207.1, D3.3 (GND), D3.8 (GND), D6.3 (GND), D6.8 (GND), D7.3 (GND), D7.8 (GND), D52.3 (GND), D52.8 (GND), LED13.2 (C), R8.1, R194.1, U15.1 (GND), U15.2 (GND), U15.3 (GND), U15.7 (EP), USB1.1 (EP), USB1.2 (EP), USB1.3 (EP), USB1.4 (EP), USB1.A1 (GND), USB1.B12 (GND)
unnamed: C67.2, R8.2, USB1.SH
unnamed: C209.2, R194.2
unnamed: LED13.1 (A), R222.1
RX1+: D6.4 (D2+), D6.7 (NC), USB1.B11 (RX1+)
RX1-: D6.5 (D2-), D6.6 (NC), USB1.B10 (RX1-)
RX2+: D7.4 (D2+), D7.7 (NC), USB1.A11 (RX2+)
RX2-: D7.5 (D2-), D7.6 (NC), USB1.A10 (RX2-)
SBU1: D3.4 (D2+), D3.7 (NC), USB1.A8 (SBU1)
SBU2: D3.5 (D2-), D3.6 (NC), USB1.B8 (SBU2)
TX1+: D6.1 (D1+), D6.10 (NC), USB1.A2 (TX1+)
TX1-: D6.2 (D1-), D6.9 (NC), USB1.A3 (TX1-)
TX2+: D7.1 (D1+), D7.10 (NC), USB1.B2 (TX2+)
TX2-: D7.2 (D1-), D7.9 (NC), USB1.B3 (TX2-)
VBUS: C84.2, C85.2, C87.2, C88.2, C207.2, C209.1, R222.2, U15.4 (VDD/IO), U15.5 (VDD/IO), U15.6 (VDD/IO), USB1.A4 (VBUS), USB1.A9 (VBUS), USB1.B4 (VBUS), USB1.B9 (VBUS)

Notes on the sheet:
Resistor network recommended by Microchip; if not required, solder a 0 ohm resistor in place of the 330 ohm resistor and leave the capacitor unsoldered.
